AlistairCheeseman/WindTunnelApparatus/Firmware/Tests/FPGA/FPGAEchoExample/GSMBS2015.2.sdk/echo_server_bsp/microblaze_0/include/xparameters.h

#ifndef XPARAMETERS_H   /* prevent circular inclusions */
#define XPARAMETERS_H   /* by using protection macros */

/* Definitions for bus frequencies */
#define XPAR_CPU_M_AXI_DP_FREQ_HZ 100000000
/******************************************************************/

/* Canonical definitions for bus frequencies */
/******************************************************************/

#define XPAR_CPU_CORE_CLOCK_FREQ_HZ 100000000
#define XPAR_MICROBLAZE_CORE_CLOCK_FREQ_HZ 100000000

/******************************************************************/


/* Definitions for peripheral MICROBLAZE_0 */
#define XPAR_MICROBLAZE_0_ADDR_TAG_BITS 10
#define XPAR_MICROBLAZE_0_ALLOW_DCACHE_WR 1
#define XPAR_MICROBLAZE_0_ALLOW_ICACHE_WR 1
#define XPAR_MICROBLAZE_0_AREA_OPTIMIZED 0
#define XPAR_MICROBLAZE_0_ASYNC_INTERRUPT 1
#define XPAR_MICROBLAZE_0_AVOID_PRIMITIVES 0
#define XPAR_MICROBLAZE_0_BASE_VECTORS 0x00000000
#define XPAR_MICROBLAZE_0_BRANCH_TARGET_CACHE_SIZE 0
#define XPAR_MICROBLAZE_0_CACHE_BYTE_SIZE 16384
#define XPAR_MICROBLAZE_0_DATA_SIZE 32
#define XPAR_MICROBLAZE_0_DCACHE_ADDR_TAG 10
#define XPAR_MICROBLAZE_0_DCACHE_ALWAYS_USED 1
#define XPAR_MICROBLAZE_0_DCACHE_BASEADDR 0x60000000
#define XPAR_MICROBLAZE_0_DCACHE_BYTE_SIZE 16384
#define XPAR_MICROBLAZE_0_DCACHE_DATA_WIDTH 0
#define XPAR_MICROBLAZE_0_DCACHE_FORCE_TAG_LUTRAM 0
#define XPAR_MICROBLAZE_0_DCACHE_HIGHADDR 0x60FFFFFF
#define XPAR_MICROBLAZE_0_DCACHE_LINE_LEN 4
#define XPAR_MICROBLAZE_0_DCACHE_USE_WRITEBACK 0
#define XPAR_MICROBLAZE_0_DCACHE_VICTIMS 0
#define XPAR_MICROBLAZE_0_DEBUG_COUNTER_WIDTH 32
#define XPAR_MICROBLAZE_0_DEBUG_ENABLED 1
#define XPAR_MICROBLAZE_0_DEBUG_EVENT_COUNTERS 5
#define XPAR_MICROBLAZE_0_DEBUG_EXTERNAL_TRACE 0
#define XPAR_MICROBLAZE_0_DEBUG_LATENCY_COUNTERS 1
#define XPAR_MICROBLAZE_0_DEBUG_PROFILE_SIZE 0
#define XPAR_MICROBLAZE_0_DEBUG_TRACE_SIZE 8192
#define XPAR_MICROBLAZE_0_DIV_ZERO_EXCEPTION 0
#define XPAR_MICROBLAZE_0_DYNAMIC_BUS_SIZING 0
#define XPAR_MICROBLAZE_0_D_AXI 1
#define XPAR_MICROBLAZE_0_D_LMB 1
#define XPAR_MICROBLAZE_0_ECC_USE_CE_EXCEPTION 0
#define XPAR_MICROBLAZE_0_EDGE_IS_POSITIVE 1
#define XPAR_MICROBLAZE_0_ENABLE_DISCRETE_PORTS 0
#define XPAR_MICROBLAZE_0_ENDIANNESS 1
#define XPAR_MICROBLAZE_0_FAULT_TOLERANT 0
#define XPAR_MICROBLAZE_0_FPU_EXCEPTION 0
#define XPAR_MICROBLAZE_0_FREQ 100000000
#define XPAR_MICROBLAZE_0_FSL_EXCEPTION 0
#define XPAR_MICROBLAZE_0_FSL_LINKS 0
#define XPAR_MICROBLAZE_0_ICACHE_ALWAYS_USED 1
#define XPAR_MICROBLAZE_0_ICACHE_BASEADDR 0x60000000
#define XPAR_MICROBLAZE_0_ICACHE_DATA_WIDTH 0
#define XPAR_MICROBLAZE_0_ICACHE_FORCE_TAG_LUTRAM 0
#define XPAR_MICROBLAZE_0_ICACHE_HIGHADDR 0x60FFFFFF
#define XPAR_MICROBLAZE_0_ICACHE_LINE_LEN 4
#define XPAR_MICROBLAZE_0_ICACHE_STREAMS 0
#define XPAR_MICROBLAZE_0_ICACHE_VICTIMS 0
#define XPAR_MICROBLAZE_0_ILL_OPCODE_EXCEPTION 0
#define XPAR_MICROBLAZE_0_IMPRECISE_EXCEPTIONS 0
#define XPAR_MICROBLAZE_0_INTERCONNECT 2
#define XPAR_MICROBLAZE_0_INTERRUPT_IS_EDGE 0
#define XPAR_MICROBLAZE_0_I_AXI 0
#define XPAR_MICROBLAZE_0_I_LMB 1
#define XPAR_MICROBLAZE_0_LOCKSTEP_SELECT 0
#define XPAR_MICROBLAZE_0_LOCKSTEP_SLAVE 0
#define XPAR_MICROBLAZE_0_M0_AXIS_DATA_WIDTH 32
#define XPAR_MICROBLAZE_0_M0_AXIS_PROTOCOL GENERIC
#define XPAR_MICROBLAZE_0_M1_AXIS_DATA_WIDTH 32
#define XPAR_MICROBLAZE_0_M1_AXIS_PROTOCOL GENERIC
#define XPAR_MICROBLAZE_0_M2_AXIS_DATA_WIDTH 32
#define XPAR_MICROBLAZE_0_M2_AXIS_PROTOCOL GENERIC
#define XPAR_MICROBLAZE_0_M3_AXIS_DATA_WIDTH 32
#define XPAR_MICROBLAZE_0_M3_AXIS_PROTOCOL GENERIC
#define XPAR_MICROBLAZE_0_M4_AXIS_DATA_WIDTH 32
#define XPAR_MICROBLAZE_0_M4_AXIS_PROTOCOL GENERIC
#define XPAR_MICROBLAZE_0_M5_AXIS_DATA_WIDTH 32
#define XPAR_MICROBLAZE_0_M5_AXIS_PROTOCOL GENERIC
#define XPAR_MICROBLAZE_0_M6_AXIS_DATA_WIDTH 32
#define XPAR_MICROBLAZE_0_M6_AXIS_PROTOCOL GENERIC
#define XPAR_MICROBLAZE_0_M7_AXIS_DATA_WIDTH 32
#define XPAR_MICROBLAZE_0_M7_AXIS_PROTOCOL GENERIC
#define XPAR_MICROBLAZE_0_M8_AXIS_DATA_WIDTH 32
#define XPAR_MICROBLAZE_0_M8_AXIS_PROTOCOL GENERIC
#define XPAR_MICROBLAZE_0_M9_AXIS_DATA_WIDTH 32
#define XPAR_MICROBLAZE_0_M9_AXIS_PROTOCOL GENERIC
#define XPAR_MICROBLAZE_0_M10_AXIS_DATA_WIDTH 32
#define XPAR_MICROBLAZE_0_M10_AXIS_PROTOCOL GENERIC
#define XPAR_MICROBLAZE_0_M11_AXIS_DATA_WIDTH 32
#define XPAR_MICROBLAZE_0_M11_AXIS_PROTOCOL GENERIC
#define XPAR_MICROBLAZE_0_M12_AXIS_DATA_WIDTH 32
#define XPAR_MICROBLAZE_0_M12_AXIS_PROTOCOL GENERIC
#define XPAR_MICROBLAZE_0_M13_AXIS_DATA_WIDTH 32
#define XPAR_MICROBLAZE_0_M13_AXIS_PROTOCOL GENERIC
#define XPAR_MICROBLAZE_0_M14_AXIS_DATA_WIDTH 32
#define XPAR_MICROBLAZE_0_M14_AXIS_PROTOCOL GENERIC
#define XPAR_MICROBLAZE_0_M15_AXIS_DATA_WIDTH 32
#define XPAR_MICROBLAZE_0_M15_AXIS_PROTOCOL GENERIC
#define XPAR_MICROBLAZE_0_MMU_DTLB_SIZE 4
#define XPAR_MICROBLAZE_0_MMU_ITLB_SIZE 2
#define XPAR_MICROBLAZE_0_MMU_PRIVILEGED_INSTR 0
#define XPAR_MICROBLAZE_0_MMU_TLB_ACCESS 3
#define XPAR_MICROBLAZE_0_MMU_ZONES 16
#define XPAR_MICROBLAZE_0_M_AXI_DC_ADDR_WIDTH 32
#define XPAR_MICROBLAZE_0_M_AXI_DC_ARUSER_WIDTH 5
#define XPAR_MICROBLAZE_0_M_AXI_DC_AWUSER_WIDTH 5
#define XPAR_MICROBLAZE_0_M_AXI_DC_BUSER_WIDTH 1
#define XPAR_MICROBLAZE_0_M_AXI_DC_DATA_WIDTH 32
#define XPAR_MICROBLAZE_0_M_AXI_DC_EXCLUSIVE_ACCESS 0
#define XPAR_MICROBLAZE_0_M_AXI_DC_RUSER_WIDTH 1
#define XPAR_MICROBLAZE_0_M_AXI_DC_THREAD_ID_WIDTH 1
#define XPAR_MICROBLAZE_0_M_AXI_DC_USER_SIGNALS 0
#define XPAR_MICROBLAZE_0_M_AXI_DC_USER_VALUE 31
#define XPAR_MICROBLAZE_0_M_AXI_DC_WUSER_WIDTH 1
#define XPAR_MICROBLAZE_0_M_AXI_DP_ADDR_WIDTH 32
#define XPAR_MICROBLAZE_0_M_AXI_DP_DATA_WIDTH 32
#define XPAR_MICROBLAZE_0_M_AXI_DP_EXCLUSIVE_ACCESS 0
#define XPAR_MICROBLAZE_0_M_AXI_DP_THREAD_ID_WIDTH 1
#define XPAR_MICROBLAZE_0_M_AXI_D_BUS_EXCEPTION 0
#define XPAR_MICROBLAZE_0_M_AXI_IC_ADDR_WIDTH 32
#define XPAR_MICROBLAZE_0_M_AXI_IC_ARUSER_WIDTH 5
#define XPAR_MICROBLAZE_0_M_AXI_IC_AWUSER_WIDTH 5
#define XPAR_MICROBLAZE_0_M_AXI_IC_BUSER_WIDTH 1
#define XPAR_MICROBLAZE_0_M_AXI_IC_DATA_WIDTH 32
#define XPAR_MICROBLAZE_0_M_AXI_IC_RUSER_WIDTH 1
#define XPAR_MICROBLAZE_0_M_AXI_IC_THREAD_ID_WIDTH 1
#define XPAR_MICROBLAZE_0_M_AXI_IC_USER_SIGNALS 0
#define XPAR_MICROBLAZE_0_M_AXI_IC_USER_VALUE 31
#define XPAR_MICROBLAZE_0_M_AXI_IC_WUSER_WIDTH 1
#define XPAR_MICROBLAZE_0_M_AXI_IP_ADDR_WIDTH 32
#define XPAR_MICROBLAZE_0_M_AXI_IP_DATA_WIDTH 32
#define XPAR_MICROBLAZE_0_M_AXI_IP_THREAD_ID_WIDTH 1
#define XPAR_MICROBLAZE_0_M_AXI_I_BUS_EXCEPTION 0
#define XPAR_MICROBLAZE_0_NUMBER_OF_PC_BRK 1
#define XPAR_MICROBLAZE_0_NUMBER_OF_RD_ADDR_BRK 0
#define XPAR_MICROBLAZE_0_NUMBER_OF_WR_ADDR_BRK 0
#define XPAR_MICROBLAZE_0_NUM_SYNC_FF_CLK 2
#define XPAR_MICROBLAZE_0_NUM_SYNC_FF_CLK_DEBUG 2
#define XPAR_MICROBLAZE_0_NUM_SYNC_FF_CLK_IRQ 1
#define XPAR_MICROBLAZE_0_NUM_SYNC_FF_DBG_CLK 1
#define XPAR_MICROBLAZE_0_OPCODE_0X0_ILLEGAL 0
#define XPAR_MICROBLAZE_0_OPTIMIZATION 0
#define XPAR_MICROBLAZE_0_PC_WIDTH 32
#define XPAR_MICROBLAZE_0_PVR 0
#define XPAR_MICROBLAZE_0_PVR_USER1 0x00
#define XPAR_MICROBLAZE_0_PVR_USER2 0x00000000
#define XPAR_MICROBLAZE_0_RESET_MSR 0x00000000
#define XPAR_MICROBLAZE_0_S0_AXIS_DATA_WIDTH 32
#define XPAR_MICROBLAZE_0_S0_AXIS_PROTOCOL GENERIC
#define XPAR_MICROBLAZE_0_S1_AXIS_DATA_WIDTH 32
#define XPAR_MICROBLAZE_0_S1_AXIS_PROTOCOL GENERIC
#define XPAR_MICROBLAZE_0_S2_AXIS_DATA_WIDTH 32
#define XPAR_MICROBLAZE_0_S2_AXIS_PROTOCOL GENERIC
#define XPAR_MICROBLAZE_0_S3_AXIS_DATA_WIDTH 32
#define XPAR_MICROBLAZE_0_S3_AXIS_PROTOCOL GENERIC
#define XPAR_MICROBLAZE_0_S4_AXIS_DATA_WIDTH 32
#define XPAR_MICROBLAZE_0_S4_AXIS_PROTOCOL GENERIC
#define XPAR_MICROBLAZE_0_S5_AXIS_DATA_WIDTH 32
#define XPAR_MICROBLAZE_0_S5_AXIS_PROTOCOL GENERIC
#define XPAR_MICROBLAZE_0_S6_AXIS_DATA_WIDTH 32
#define XPAR_MICROBLAZE_0_S6_AXIS_PROTOCOL GENERIC
#define XPAR_MICROBLAZE_0_S7_AXIS_DATA_WIDTH 32
#define XPAR_MICROBLAZE_0_S7_AXIS_PROTOCOL GENERIC
#define XPAR_MICROBLAZE_0_S8_AXIS_DATA_WIDTH 32
#define XPAR_MICROBLAZE_0_S8_AXIS_PROTOCOL GENERIC
#define XPAR_MICROBLAZE_0_S9_AXIS_DATA_WIDTH 32
#define XPAR_MICROBLAZE_0_S9_AXIS_PROTOCOL GENERIC
#define XPAR_MICROBLAZE_0_S10_AXIS_DATA_WIDTH 32
#define XPAR_MICROBLAZE_0_S10_AXIS_PROTOCOL GENERIC
#define XPAR_MICROBLAZE_0_S11_AXIS_DATA_WIDTH 32
#define XPAR_MICROBLAZE_0_S11_AXIS_PROTOCOL GENERIC
#define XPAR_MICROBLAZE_0_S12_AXIS_DATA_WIDTH 32
#define XPAR_MICROBLAZE_0_S12_AXIS_PROTOCOL GENERIC
#define XPAR_MICROBLAZE_0_S13_AXIS_DATA_WIDTH 32
#define XPAR_MICROBLAZE_0_S13_AXIS_PROTOCOL GENERIC
#define XPAR_MICROBLAZE_0_S14_AXIS_DATA_WIDTH 32
#define XPAR_MICROBLAZE_0_S14_AXIS_PROTOCOL GENERIC
#define XPAR_MICROBLAZE_0_S15_AXIS_DATA_WIDTH 32
#define XPAR_MICROBLAZE_0_S15_AXIS_PROTOCOL GENERIC
#define XPAR_MICROBLAZE_0_SCO 0
#define XPAR_MICROBLAZE_0_TRACE 0
#define XPAR_MICROBLAZE_0_UNALIGNED_EXCEPTIONS 0
#define XPAR_MICROBLAZE_0_USE_BARREL 0
#define XPAR_MICROBLAZE_0_USE_BRANCH_TARGET_CACHE 0
#define XPAR_MICROBLAZE_0_USE_CONFIG_RESET 0
#define XPAR_MICROBLAZE_0_USE_DCACHE 1
#define XPAR_MICROBLAZE_0_USE_DIV 0
#define XPAR_MICROBLAZE_0_USE_EXTENDED_FSL_INSTR 0
#define XPAR_MICROBLAZE_0_USE_EXT_BRK 0
#define XPAR_MICROBLAZE_0_USE_EXT_NM_BRK 0
#define XPAR_MICROBLAZE_0_USE_FPU 0
#define XPAR_MICROBLAZE_0_USE_HW_MUL 0
#define XPAR_MICROBLAZE_0_USE_ICACHE 1
#define XPAR_MICROBLAZE_0_USE_INTERRUPT 2
#define XPAR_MICROBLAZE_0_USE_MMU 0
#define XPAR_MICROBLAZE_0_USE_MSR_INSTR 0
#define XPAR_MICROBLAZE_0_USE_PCMP_INSTR 0
#define XPAR_MICROBLAZE_0_USE_REORDER_INSTR 1
#define XPAR_MICROBLAZE_0_USE_STACK_PROTECTION 0
#define XPAR_MICROBLAZE_0_COMPONENT_NAME design_1_microblaze_0_0
#define XPAR_MICROBLAZE_0_EDK_IPTYPE PROCESSOR
#define XPAR_MICROBLAZE_0_EDK_SPECIAL microblaze
#define XPAR_MICROBLAZE_0_G_TEMPLATE_LIST 0
#define XPAR_MICROBLAZE_0_G_USE_EXCEPTIONS 0

/******************************************************************/

#define XPAR_CPU_ID 0
#define XPAR_MICROBLAZE_ID 0
#define XPAR_MICROBLAZE_ADDR_TAG_BITS 10
#define XPAR_MICROBLAZE_ALLOW_DCACHE_WR 1
#define XPAR_MICROBLAZE_ALLOW_ICACHE_WR 1
#define XPAR_MICROBLAZE_AREA_OPTIMIZED 0
#define XPAR_MICROBLAZE_ASYNC_INTERRUPT 1
#define XPAR_MICROBLAZE_AVOID_PRIMITIVES 0
#define XPAR_MICROBLAZE_BASE_VECTORS 0x00000000
#define XPAR_MICROBLAZE_BRANCH_TARGET_CACHE_SIZE 0
#define XPAR_MICROBLAZE_CACHE_BYTE_SIZE 16384
#define XPAR_MICROBLAZE_DATA_SIZE 32
#define XPAR_MICROBLAZE_DCACHE_ADDR_TAG 10
#define XPAR_MICROBLAZE_DCACHE_ALWAYS_USED 1
#define XPAR_MICROBLAZE_DCACHE_BASEADDR 0x60000000
#define XPAR_MICROBLAZE_DCACHE_BYTE_SIZE 16384
#define XPAR_MICROBLAZE_DCACHE_DATA_WIDTH 0
#define XPAR_MICROBLAZE_DCACHE_FORCE_TAG_LUTRAM 0
#define XPAR_MICROBLAZE_DCACHE_HIGHADDR 0x60FFFFFF
#define XPAR_MICROBLAZE_DCACHE_LINE_LEN 4
#define XPAR_MICROBLAZE_DCACHE_USE_WRITEBACK 0
#define XPAR_MICROBLAZE_DCACHE_VICTIMS 0
#define XPAR_MICROBLAZE_DEBUG_COUNTER_WIDTH 32
#define XPAR_MICROBLAZE_DEBUG_ENABLED 1
#define XPAR_MICROBLAZE_DEBUG_EVENT_COUNTERS 5
#define XPAR_MICROBLAZE_DEBUG_EXTERNAL_TRACE 0
#define XPAR_MICROBLAZE_DEBUG_LATENCY_COUNTERS 1
#define XPAR_MICROBLAZE_DEBUG_PROFILE_SIZE 0
#define XPAR_MICROBLAZE_DEBUG_TRACE_SIZE 8192
#define XPAR_MICROBLAZE_DIV_ZERO_EXCEPTION 0
#define XPAR_MICROBLAZE_DYNAMIC_BUS_SIZING 0
#define XPAR_MICROBLAZE_D_AXI 1
#define XPAR_MICROBLAZE_D_LMB 1
#define XPAR_MICROBLAZE_ECC_USE_CE_EXCEPTION 0
#define XPAR_MICROBLAZE_EDGE_IS_POSITIVE 1
#define XPAR_MICROBLAZE_ENABLE_DISCRETE_PORTS 0
#define XPAR_MICROBLAZE_ENDIANNESS 1
#define XPAR_MICROBLAZE_FAULT_TOLERANT 0
#define XPAR_MICROBLAZE_FPU_EXCEPTION 0
#define XPAR_MICROBLAZE_FREQ 100000000
#define XPAR_MICROBLAZE_FSL_EXCEPTION 0
#define XPAR_MICROBLAZE_FSL_LINKS 0
#define XPAR_MICROBLAZE_ICACHE_ALWAYS_USED 1
#define XPAR_MICROBLAZE_ICACHE_BASEADDR 0x60000000
#define XPAR_MICROBLAZE_ICACHE_DATA_WIDTH 0
#define XPAR_MICROBLAZE_ICACHE_FORCE_TAG_LUTRAM 0
#define XPAR_MICROBLAZE_ICACHE_HIGHADDR 0x60FFFFFF
#define XPAR_MICROBLAZE_ICACHE_LINE_LEN 4
#define XPAR_MICROBLAZE_ICACHE_STREAMS 0
#define XPAR_MICROBLAZE_ICACHE_VICTIMS 0
#define XPAR_MICROBLAZE_ILL_OPCODE_EXCEPTION 0
#define XPAR_MICROBLAZE_IMPRECISE_EXCEPTIONS 0
#define XPAR_MICROBLAZE_INTERCONNECT 2
#define XPAR_MICROBLAZE_INTERRUPT_IS_EDGE 0
#define XPAR_MICROBLAZE_I_AXI 0
#define XPAR_MICROBLAZE_I_LMB 1
#define XPAR_MICROBLAZE_LOCKSTEP_SELECT 0
#define XPAR_MICROBLAZE_LOCKSTEP_SLAVE 0
#define XPAR_MICROBLAZE_M0_AXIS_DATA_WIDTH 32
#define XPAR_MICROBLAZE_M0_AXIS_PROTOCOL GENERIC
#define XPAR_MICROBLAZE_M1_AXIS_DATA_WIDTH 32
#define XPAR_MICROBLAZE_M1_AXIS_PROTOCOL GENERIC
#define XPAR_MICROBLAZE_M2_AXIS_DATA_WIDTH 32
#define XPAR_MICROBLAZE_M2_AXIS_PROTOCOL GENERIC
#define XPAR_MICROBLAZE_M3_AXIS_DATA_WIDTH 32
#define XPAR_MICROBLAZE_M3_AXIS_PROTOCOL GENERIC
#define XPAR_MICROBLAZE_M4_AXIS_DATA_WIDTH 32
#define XPAR_MICROBLAZE_M4_AXIS_PROTOCOL GENERIC
#define XPAR_MICROBLAZE_M5_AXIS_DATA_WIDTH 32
#define XPAR_MICROBLAZE_M5_AXIS_PROTOCOL GENERIC
#define XPAR_MICROBLAZE_M6_AXIS_DATA_WIDTH 32
#define XPAR_MICROBLAZE_M6_AXIS_PROTOCOL GENERIC
#define XPAR_MICROBLAZE_M7_AXIS_DATA_WIDTH 32
#define XPAR_MICROBLAZE_M7_AXIS_PROTOCOL GENERIC
#define XPAR_MICROBLAZE_M8_AXIS_DATA_WIDTH 32
#define XPAR_MICROBLAZE_M8_AXIS_PROTOCOL GENERIC
#define XPAR_MICROBLAZE_M9_AXIS_DATA_WIDTH 32
#define XPAR_MICROBLAZE_M9_AXIS_PROTOCOL GENERIC
#define XPAR_MICROBLAZE_M10_AXIS_DATA_WIDTH 32
#define XPAR_MICROBLAZE_M10_AXIS_PROTOCOL GENERIC
#define XPAR_MICROBLAZE_M11_AXIS_DATA_WIDTH 32
#define XPAR_MICROBLAZE_M11_AXIS_PROTOCOL GENERIC
#define XPAR_MICROBLAZE_M12_AXIS_DATA_WIDTH 32
#define XPAR_MICROBLAZE_M12_AXIS_PROTOCOL GENERIC
#define XPAR_MICROBLAZE_M13_AXIS_DATA_WIDTH 32
#define XPAR_MICROBLAZE_M13_AXIS_PROTOCOL GENERIC
#define XPAR_MICROBLAZE_M14_AXIS_DATA_WIDTH 32
#define XPAR_MICROBLAZE_M14_AXIS_PROTOCOL GENERIC
#define XPAR_MICROBLAZE_M15_AXIS_DATA_WIDTH 32
#define XPAR_MICROBLAZE_M15_AXIS_PROTOCOL GENERIC
#define XPAR_MICROBLAZE_MMU_DTLB_SIZE 4
#define XPAR_MICROBLAZE_MMU_ITLB_SIZE 2
#define XPAR_MICROBLAZE_MMU_PRIVILEGED_INSTR 0
#define XPAR_MICROBLAZE_MMU_TLB_ACCESS 3
#define XPAR_MICROBLAZE_MMU_ZONES 16
#define XPAR_MICROBLAZE_M_AXI_DC_ADDR_WIDTH 32
#define XPAR_MICROBLAZE_M_AXI_DC_ARUSER_WIDTH 5
#define XPAR_MICROBLAZE_M_AXI_DC_AWUSER_WIDTH 5
#define XPAR_MICROBLAZE_M_AXI_DC_BUSER_WIDTH 1
#define XPAR_MICROBLAZE_M_AXI_DC_DATA_WIDTH 32
#define XPAR_MICROBLAZE_M_AXI_DC_EXCLUSIVE_ACCESS 0
#define XPAR_MICROBLAZE_M_AXI_DC_RUSER_WIDTH 1
#define XPAR_MICROBLAZE_M_AXI_DC_THREAD_ID_WIDTH 1
#define XPAR_MICROBLAZE_M_AXI_DC_USER_SIGNALS 0
#define XPAR_MICROBLAZE_M_AXI_DC_USER_VALUE 31
#define XPAR_MICROBLAZE_M_AXI_DC_WUSER_WIDTH 1
#define XPAR_MICROBLAZE_M_AXI_DP_ADDR_WIDTH 32
#define XPAR_MICROBLAZE_M_AXI_DP_DATA_WIDTH 32
#define XPAR_MICROBLAZE_M_AXI_DP_EXCLUSIVE_ACCESS 0
#define XPAR_MICROBLAZE_M_AXI_DP_THREAD_ID_WIDTH 1
#define XPAR_MICROBLAZE_M_AXI_D_BUS_EXCEPTION 0
#define XPAR_MICROBLAZE_M_AXI_IC_ADDR_WIDTH 32
#define XPAR_MICROBLAZE_M_AXI_IC_ARUSER_WIDTH 5
#define XPAR_MICROBLAZE_M_AXI_IC_AWUSER_WIDTH 5
#define XPAR_MICROBLAZE_M_AXI_IC_BUSER_WIDTH 1
#define XPAR_MICROBLAZE_M_AXI_IC_DATA_WIDTH 32
#define XPAR_MICROBLAZE_M_AXI_IC_RUSER_WIDTH 1
#define XPAR_MICROBLAZE_M_AXI_IC_THREAD_ID_WIDTH 1
#define XPAR_MICROBLAZE_M_AXI_IC_USER_SIGNALS 0
#define XPAR_MICROBLAZE_M_AXI_IC_USER_VALUE 31
#define XPAR_MICROBLAZE_M_AXI_IC_WUSER_WIDTH 1
#define XPAR_MICROBLAZE_M_AXI_IP_ADDR_WIDTH 32
#define XPAR_MICROBLAZE_M_AXI_IP_DATA_WIDTH 32
#define XPAR_MICROBLAZE_M_AXI_IP_THREAD_ID_WIDTH 1
#define XPAR_MICROBLAZE_M_AXI_I_BUS_EXCEPTION 0
#define XPAR_MICROBLAZE_NUMBER_OF_PC_BRK 1
#define XPAR_MICROBLAZE_NUMBER_OF_RD_ADDR_BRK 0
#define XPAR_MICROBLAZE_NUMBER_OF_WR_ADDR_BRK 0
#define XPAR_MICROBLAZE_NUM_SYNC_FF_CLK 2
#define XPAR_MICROBLAZE_NUM_SYNC_FF_CLK_DEBUG 2
#define XPAR_MICROBLAZE_NUM_SYNC_FF_CLK_IRQ 1
#define XPAR_MICROBLAZE_NUM_SYNC_FF_DBG_CLK 1
#define XPAR_MICROBLAZE_OPCODE_0X0_ILLEGAL 0
#define XPAR_MICROBLAZE_OPTIMIZATION 0
#define XPAR_MICROBLAZE_PC_WIDTH 32
#define XPAR_MICROBLAZE_PVR 0
#define XPAR_MICROBLAZE_PVR_USER1 0x00
#define XPAR_MICROBLAZE_PVR_USER2 0x00000000
#define XPAR_MICROBLAZE_RESET_MSR 0x00000000
#define XPAR_MICROBLAZE_S0_AXIS_DATA_WIDTH 32
#define XPAR_MICROBLAZE_S0_AXIS_PROTOCOL GENERIC
#define XPAR_MICROBLAZE_S1_AXIS_DATA_WIDTH 32
#define XPAR_MICROBLAZE_S1_AXIS_PROTOCOL GENERIC
#define XPAR_MICROBLAZE_S2_AXIS_DATA_WIDTH 32
#define XPAR_MICROBLAZE_S2_AXIS_PROTOCOL GENERIC
#define XPAR_MICROBLAZE_S3_AXIS_DATA_WIDTH 32
#define XPAR_MICROBLAZE_S3_AXIS_PROTOCOL GENERIC
#define XPAR_MICROBLAZE_S4_AXIS_DATA_WIDTH 32
#define XPAR_MICROBLAZE_S4_AXIS_PROTOCOL GENERIC
#define XPAR_MICROBLAZE_S5_AXIS_DATA_WIDTH 32
#define XPAR_MICROBLAZE_S5_AXIS_PROTOCOL GENERIC
#define XPAR_MICROBLAZE_S6_AXIS_DATA_WIDTH 32
#define XPAR_MICROBLAZE_S6_AXIS_PROTOCOL GENERIC
#define XPAR_MICROBLAZE_S7_AXIS_DATA_WIDTH 32
#define XPAR_MICROBLAZE_S7_AXIS_PROTOCOL GENERIC
#define XPAR_MICROBLAZE_S8_AXIS_DATA_WIDTH 32
#define XPAR_MICROBLAZE_S8_AXIS_PROTOCOL GENERIC
#define XPAR_MICROBLAZE_S9_AXIS_DATA_WIDTH 32
#define XPAR_MICROBLAZE_S9_AXIS_PROTOCOL GENERIC
#define XPAR_MICROBLAZE_S10_AXIS_DATA_WIDTH 32
#define XPAR_MICROBLAZE_S10_AXIS_PROTOCOL GENERIC
#define XPAR_MICROBLAZE_S11_AXIS_DATA_WIDTH 32
#define XPAR_MICROBLAZE_S11_AXIS_PROTOCOL GENERIC
#define XPAR_MICROBLAZE_S12_AXIS_DATA_WIDTH 32
#define XPAR_MICROBLAZE_S12_AXIS_PROTOCOL GENERIC
#define XPAR_MICROBLAZE_S13_AXIS_DATA_WIDTH 32
#define XPAR_MICROBLAZE_S13_AXIS_PROTOCOL GENERIC
#define XPAR_MICROBLAZE_S14_AXIS_DATA_WIDTH 32
#define XPAR_MICROBLAZE_S14_AXIS_PROTOCOL GENERIC
#define XPAR_MICROBLAZE_S15_AXIS_DATA_WIDTH 32
#define XPAR_MICROBLAZE_S15_AXIS_PROTOCOL GENERIC
#define XPAR_MICROBLAZE_SCO 0
#define XPAR_MICROBLAZE_TRACE 0
#define XPAR_MICROBLAZE_UNALIGNED_EXCEPTIONS 0
#define XPAR_MICROBLAZE_USE_BARREL 0
#define XPAR_MICROBLAZE_USE_BRANCH_TARGET_CACHE 0
#define XPAR_MICROBLAZE_USE_CONFIG_RESET 0
#define XPAR_MICROBLAZE_USE_DCACHE 1
#define XPAR_MICROBLAZE_USE_DIV 0
#define XPAR_MICROBLAZE_USE_EXTENDED_FSL_INSTR 0
#define XPAR_MICROBLAZE_USE_EXT_BRK 0
#define XPAR_MICROBLAZE_USE_EXT_NM_BRK 0
#define XPAR_MICROBLAZE_USE_FPU 0
#define XPAR_MICROBLAZE_USE_HW_MUL 0
#define XPAR_MICROBLAZE_USE_ICACHE 1
#define XPAR_MICROBLAZE_USE_INTERRUPT 2
#define XPAR_MICROBLAZE_USE_MMU 0
#define XPAR_MICROBLAZE_USE_MSR_INSTR 0
#define XPAR_MICROBLAZE_USE_PCMP_INSTR 0
#define XPAR_MICROBLAZE_USE_REORDER_INSTR 1
#define XPAR_MICROBLAZE_USE_STACK_PROTECTION 0
#define XPAR_MICROBLAZE_COMPONENT_NAME design_1_microblaze_0_0
#define XPAR_MICROBLAZE_EDK_IPTYPE PROCESSOR
#define XPAR_MICROBLAZE_EDK_SPECIAL microblaze
#define XPAR_MICROBLAZE_G_TEMPLATE_LIST 0
#define XPAR_MICROBLAZE_G_USE_EXCEPTIONS 0

/******************************************************************/

#define STDIN_BASEADDRESS 0x40600000
#define STDOUT_BASEADDRESS 0x40600000

/******************************************************************/

/* Definitions for driver BRAM */
#define XPAR_XBRAM_NUM_INSTANCES 2

/* Definitions for peripheral MICROBLAZE_0_LOCAL_MEMORY_DLMB_BRAM_IF_CNTLR */
#define XPAR_MICROBLAZE_0_LOCAL_MEMORY_DLMB_BRAM_IF_CNTLR_DEVICE_ID 0
#define XPAR_MICROBLAZE_0_LOCAL_MEMORY_DLMB_BRAM_IF_CNTLR_DATA_WIDTH 32
#define XPAR_MICROBLAZE_0_LOCAL_MEMORY_DLMB_BRAM_IF_CNTLR_ECC 0
#define XPAR_MICROBLAZE_0_LOCAL_MEMORY_DLMB_BRAM_IF_CNTLR_FAULT_INJECT 0
#define XPAR_MICROBLAZE_0_LOCAL_MEMORY_DLMB_BRAM_IF_CNTLR_CE_FAILING_REGISTERS 0
#define XPAR_MICROBLAZE_0_LOCAL_MEMORY_DLMB_BRAM_IF_CNTLR_UE_FAILING_REGISTERS 0
#define XPAR_MICROBLAZE_0_LOCAL_MEMORY_DLMB_BRAM_IF_CNTLR_ECC_STATUS_REGISTERS 0
#define XPAR_MICROBLAZE_0_LOCAL_MEMORY_DLMB_BRAM_IF_CNTLR_CE_COUNTER_WIDTH 0
#define XPAR_MICROBLAZE_0_LOCAL_MEMORY_DLMB_BRAM_IF_CNTLR_ECC_ONOFF_REGISTER 0
#define XPAR_MICROBLAZE_0_LOCAL_MEMORY_DLMB_BRAM_IF_CNTLR_ECC_ONOFF_RESET_VALUE 1
#define XPAR_MICROBLAZE_0_LOCAL_MEMORY_DLMB_BRAM_IF_CNTLR_WRITE_ACCESS 2
#define XPAR_MICROBLAZE_0_LOCAL_MEMORY_DLMB_BRAM_IF_CNTLR_BASEADDR 0x00000000
#define XPAR_MICROBLAZE_0_LOCAL_MEMORY_DLMB_BRAM_IF_CNTLR_HIGHADDR 0x00007FFF
#define XPAR_MICROBLAZE_0_LOCAL_MEMORY_DLMB_BRAM_IF_CNTLR_S_AXI_CTRL_BASEADDR 0xFFFFFFFF 
#define XPAR_MICROBLAZE_0_LOCAL_MEMORY_DLMB_BRAM_IF_CNTLR_S_AXI_CTRL_HIGHADDR 0xFFFFFFFF 


/* Definitions for peripheral MICROBLAZE_0_LOCAL_MEMORY_ILMB_BRAM_IF_CNTLR */
#define XPAR_MICROBLAZE_0_LOCAL_MEMORY_ILMB_BRAM_IF_CNTLR_DEVICE_ID 1
#define XPAR_MICROBLAZE_0_LOCAL_MEMORY_ILMB_BRAM_IF_CNTLR_DATA_WIDTH 32
#define XPAR_MICROBLAZE_0_LOCAL_MEMORY_ILMB_BRAM_IF_CNTLR_ECC 0
#define XPAR_MICROBLAZE_0_LOCAL_MEMORY_ILMB_BRAM_IF_CNTLR_FAULT_INJECT 0
#define XPAR_MICROBLAZE_0_LOCAL_MEMORY_ILMB_BRAM_IF_CNTLR_CE_FAILING_REGISTERS 0
#define XPAR_MICROBLAZE_0_LOCAL_MEMORY_ILMB_BRAM_IF_CNTLR_UE_FAILING_REGISTERS 0
#define XPAR_MICROBLAZE_0_LOCAL_MEMORY_ILMB_BRAM_IF_CNTLR_ECC_STATUS_REGISTERS 0
#define XPAR_MICROBLAZE_0_LOCAL_MEMORY_ILMB_BRAM_IF_CNTLR_CE_COUNTER_WIDTH 0
#define XPAR_MICROBLAZE_0_LOCAL_MEMORY_ILMB_BRAM_IF_CNTLR_ECC_ONOFF_REGISTER 0
#define XPAR_MICROBLAZE_0_LOCAL_MEMORY_ILMB_BRAM_IF_CNTLR_ECC_ONOFF_RESET_VALUE 1
#define XPAR_MICROBLAZE_0_LOCAL_MEMORY_ILMB_BRAM_IF_CNTLR_WRITE_ACCESS 2
#define XPAR_MICROBLAZE_0_LOCAL_MEMORY_ILMB_BRAM_IF_CNTLR_BASEADDR 0x00000000
#define XPAR_MICROBLAZE_0_LOCAL_MEMORY_ILMB_BRAM_IF_CNTLR_HIGHADDR 0x00007FFF
#define XPAR_MICROBLAZE_0_LOCAL_MEMORY_ILMB_BRAM_IF_CNTLR_S_AXI_CTRL_BASEADDR 0xFFFFFFFF 
#define XPAR_MICROBLAZE_0_LOCAL_MEMORY_ILMB_BRAM_IF_CNTLR_S_AXI_CTRL_HIGHADDR 0xFFFFFFFF 


/******************************************************************/

/* Canonical definitions for peripheral MICROBLAZE_0_LOCAL_MEMORY_DLMB_BRAM_IF_CNTLR */
#define XPAR_BRAM_0_DEVICE_ID XPAR_MICROBLAZE_0_LOCAL_MEMORY_DLMB_BRAM_IF_CNTLR_DEVICE_ID
#define XPAR_BRAM_0_DATA_WIDTH 32
#define XPAR_BRAM_0_ECC 0
#define XPAR_BRAM_0_FAULT_INJECT 0
#define XPAR_BRAM_0_CE_FAILING_REGISTERS 0
#define XPAR_BRAM_0_UE_FAILING_REGISTERS 0
#define XPAR_BRAM_0_ECC_STATUS_REGISTERS 0
#define XPAR_BRAM_0_CE_COUNTER_WIDTH 0
#define XPAR_BRAM_0_ECC_ONOFF_REGISTER 0
#define XPAR_BRAM_0_ECC_ONOFF_RESET_VALUE 1
#define XPAR_BRAM_0_WRITE_ACCESS 2
#define XPAR_BRAM_0_BASEADDR 0x00000000
#define XPAR_BRAM_0_HIGHADDR 0x00007FFF

/* Canonical definitions for peripheral MICROBLAZE_0_LOCAL_MEMORY_ILMB_BRAM_IF_CNTLR */
#define XPAR_BRAM_1_DEVICE_ID XPAR_MICROBLAZE_0_LOCAL_MEMORY_ILMB_BRAM_IF_CNTLR_DEVICE_ID
#define XPAR_BRAM_1_DATA_WIDTH 32
#define XPAR_BRAM_1_ECC 0
#define XPAR_BRAM_1_FAULT_INJECT 0
#define XPAR_BRAM_1_CE_FAILING_REGISTERS 0
#define XPAR_BRAM_1_UE_FAILING_REGISTERS 0
#define XPAR_BRAM_1_ECC_STATUS_REGISTERS 0
#define XPAR_BRAM_1_CE_COUNTER_WIDTH 0
#define XPAR_BRAM_1_ECC_ONOFF_REGISTER 0
#define XPAR_BRAM_1_ECC_ONOFF_RESET_VALUE 1
#define XPAR_BRAM_1_WRITE_ACCESS 2
#define XPAR_BRAM_1_BASEADDR 0x00000000
#define XPAR_BRAM_1_HIGHADDR 0x00007FFF


/******************************************************************/

/* Definitions for driver EMACLITE */
#define XPAR_XEMACLITE_NUM_INSTANCES 1

/* Definitions for peripheral AXI_ETHERNETLITE_0 */
#define XPAR_AXI_ETHERNETLITE_0_DEVICE_ID 0
#define XPAR_AXI_ETHERNETLITE_0_BASEADDR 0x40E00000
#define XPAR_AXI_ETHERNETLITE_0_HIGHADDR 0x40E0FFFF
#define XPAR_AXI_ETHERNETLITE_0_TX_PING_PONG 1
#define XPAR_AXI_ETHERNETLITE_0_RX_PING_PONG 1
#define XPAR_AXI_ETHERNETLITE_0_INCLUDE_MDIO 1
#define XPAR_AXI_ETHERNETLITE_0_INCLUDE_INTERNAL_LOOPBACK 0


/******************************************************************/

/* Canonical definitions for peripheral AXI_ETHERNETLITE_0 */
#define XPAR_EMACLITE_0_DEVICE_ID XPAR_AXI_ETHERNETLITE_0_DEVICE_ID
#define XPAR_EMACLITE_0_BASEADDR 0x40E00000
#define XPAR_EMACLITE_0_HIGHADDR 0x40E0FFFF
#define XPAR_EMACLITE_0_TX_PING_PONG 1
#define XPAR_EMACLITE_0_RX_PING_PONG 1
#define XPAR_EMACLITE_0_INCLUDE_MDIO 1
#define XPAR_EMACLITE_0_INCLUDE_INTERNAL_LOOPBACK 0


/******************************************************************/


/* Definitions for peripheral AXI_EMC_0 */
#define XPAR_AXI_EMC_0_NUM_BANKS_MEM 1


/******************************************************************/

/* Definitions for peripheral AXI_EMC_0 */
#define XPAR_AXI_EMC_0_S_AXI_MEM0_BASEADDR 0x60000000

/******************************************************************/

/* Canonical definitions for peripheral AXI_EMC_0 */
#define XPAR_EMC_0_NUM_BANKS_MEM 1
#define XPAR_EMC_0_S_AXI_MEM0_BASEADDR 0x60000000
#define XPAR_EMC_0_S_AXI_MEM0_HIGHADDR 0x60FFFFFF

#define XPAR_AXI_EMC

/******************************************************************/

#define XPAR_INTC_MAX_NUM_INTR_INPUTS 2
#define XPAR_XINTC_HAS_IPR 1
#define XPAR_XINTC_HAS_SIE 1
#define XPAR_XINTC_HAS_CIE 1
#define XPAR_XINTC_HAS_IVR 1
/* Definitions for driver INTC */
#define XPAR_XINTC_NUM_INSTANCES 1

/* Definitions for peripheral MICROBLAZE_0_AXI_INTC */
#define XPAR_MICROBLAZE_0_AXI_INTC_DEVICE_ID 0
#define XPAR_MICROBLAZE_0_AXI_INTC_BASEADDR 0x41200000
#define XPAR_MICROBLAZE_0_AXI_INTC_HIGHADDR 0x4120FFFF
#define XPAR_MICROBLAZE_0_AXI_INTC_KIND_OF_INTR 0xFFFFFFFE
#define XPAR_MICROBLAZE_0_AXI_INTC_HAS_FAST 1
#define XPAR_MICROBLAZE_0_AXI_INTC_IVAR_RESET_VALUE 0x00000010
#define XPAR_MICROBLAZE_0_AXI_INTC_NUM_INTR_INPUTS 2


/******************************************************************/

#define XPAR_INTC_SINGLE_BASEADDR 0x41200000
#define XPAR_INTC_SINGLE_HIGHADDR 0x4120FFFF
#define XPAR_INTC_SINGLE_DEVICE_ID XPAR_MICROBLAZE_0_AXI_INTC_DEVICE_ID
#define XPAR_MICROBLAZE_0_AXI_INTC_TYPE 0
#define XPAR_AXI_TIMER_0_INTERRUPT_MASK 0X000001
#define XPAR_MICROBLAZE_0_AXI_INTC_AXI_TIMER_0_INTERRUPT_INTR 0
#define XPAR_AXI_ETHERNETLITE_0_IP2INTC_IRPT_MASK 0X000002
#define XPAR_MICROBLAZE_0_AXI_INTC_AXI_ETHERNETLITE_0_IP2INTC_IRPT_INTR 1

/******************************************************************/

/* Canonical definitions for peripheral MICROBLAZE_0_AXI_INTC */
#define XPAR_INTC_0_DEVICE_ID XPAR_MICROBLAZE_0_AXI_INTC_DEVICE_ID
#define XPAR_INTC_0_BASEADDR 0x41200000
#define XPAR_INTC_0_HIGHADDR 0x4120FFFF
#define XPAR_INTC_0_KIND_OF_INTR 0xFFFFFFFE
#define XPAR_INTC_0_HAS_FAST 1
#define XPAR_INTC_0_IVAR_RESET_VALUE 0x00000010
#define XPAR_INTC_0_NUM_INTR_INPUTS 2
#define XPAR_INTC_0_INTC_TYPE 0

#define XPAR_INTC_0_TMRCTR_0_VEC_ID XPAR_MICROBLAZE_0_AXI_INTC_AXI_TIMER_0_INTERRUPT_INTR
#define XPAR_INTC_0_EMACLITE_0_VEC_ID XPAR_MICROBLAZE_0_AXI_INTC_AXI_ETHERNETLITE_0_IP2INTC_IRPT_INTR

/******************************************************************/

/* Definitions for driver TMRCTR */
#define XPAR_XTMRCTR_NUM_INSTANCES 1

/* Definitions for peripheral AXI_TIMER_0 */
#define XPAR_AXI_TIMER_0_DEVICE_ID 0
#define XPAR_AXI_TIMER_0_BASEADDR 0x41C00000
#define XPAR_AXI_TIMER_0_HIGHADDR 0x41C0FFFF
#define XPAR_AXI_TIMER_0_CLOCK_FREQ_HZ 100000000


/******************************************************************/

/* Canonical definitions for peripheral AXI_TIMER_0 */
#define XPAR_TMRCTR_0_DEVICE_ID 0
#define XPAR_TMRCTR_0_BASEADDR 0x41C00000
#define XPAR_TMRCTR_0_HIGHADDR 0x41C0FFFF
#define XPAR_TMRCTR_0_CLOCK_FREQ_HZ XPAR_AXI_TIMER_0_CLOCK_FREQ_HZ

/******************************************************************/

/* Definitions for driver UARTLITE */
#define XPAR_XUARTLITE_NUM_INSTANCES 1

/* Definitions for peripheral AXI_UARTLITE_0 */
#define XPAR_AXI_UARTLITE_0_BASEADDR 0x40600000
#define XPAR_AXI_UARTLITE_0_HIGHADDR 0x4060FFFF
#define XPAR_AXI_UARTLITE_0_DEVICE_ID 0
#define XPAR_AXI_UARTLITE_0_BAUDRATE 9600
#define XPAR_AXI_UARTLITE_0_USE_PARITY 0
#define XPAR_AXI_UARTLITE_0_ODD_PARITY 0
#define XPAR_AXI_UARTLITE_0_DATA_BITS 8


/******************************************************************/

/* Canonical definitions for peripheral AXI_UARTLITE_0 */
#define XPAR_UARTLITE_0_DEVICE_ID XPAR_AXI_UARTLITE_0_DEVICE_ID
#define XPAR_UARTLITE_0_BASEADDR 0x40600000
#define XPAR_UARTLITE_0_HIGHADDR 0x4060FFFF
#define XPAR_UARTLITE_0_BAUDRATE 9600
#define XPAR_UARTLITE_0_USE_PARITY 0
#define XPAR_UARTLITE_0_ODD_PARITY 0
#define XPAR_UARTLITE_0_DATA_BITS 8


/******************************************************************/

#endif  /* end of protection macro */
