AlistairCheeseman/WindTunnelApparatus/Firmware/Tests/FPGA/FPGAUDPtest/GSMBS2015.2.sdk/UDPTest/src/main.c

/******************************************************************************
*
* Copyright (C) 2009 - 2014 Xilinx, Inc.  All rights reserved.
*
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
* Use of the Software is limited solely to applications:
* (a) running on a Xilinx device, or
* (b) that interact with a Xilinx device through a bus or interconnect.
*
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
* Except as contained in this notice, the name of the Xilinx shall not be used
* in advertising or otherwise to promote the sale, use or other dealings in
* this Software without prior written authorization from Xilinx.
*
******************************************************************************/

#include <stdio.h>

#include "xparameters.h"

#include "netif/xadapter.h"

#include "platform.h"
#include "platform_config.h"
#ifdef __arm__
#include "xil_printf.h"
#endif

#include "lwip/tcp.h"

#if LWIP_DHCP==1
#include "lwip/dhcp.h"
#endif

/* defined by each RAW mode application */
void print_utxperf_app_header();
int start_utxperf_application();
int transfer_utxperf_data();

/* missing declaration in lwIP */
void lwip_init();

#if LWIP_DHCP==1
extern volatile int dhcp_timoutcntr;
err_t dhcp_start(struct netif *netif);
#endif

extern volatile int TcpFastTmrFlag;
extern volatile int TcpSlowTmrFlag;
static struct netif server_netif;
struct netif *echo_netif;

void
print_ip(char *msg, struct ip_addr *ip) 
{
	print(msg);
	xil_printf("%d.%d.%d.%d\n\r", ip4_addr1(ip), ip4_addr2(ip), 
			ip4_addr3(ip), ip4_addr4(ip));
}

void
print_ip_settings(struct ip_addr *ip, struct ip_addr *mask, struct ip_addr *gw)
{

	print_ip("Board IP: ", ip);
	print_ip("Netmask : ", mask);
	print_ip("Gateway : ", gw);
}

#ifdef __arm__
#if XPAR_GIGE_PCS_PMA_SGMII_CORE_PRESENT == 1 || XPAR_GIGE_PCS_PMA_1000BASEX_CORE_PRESENT == 1
int ProgramSi5324(void);
int ProgramSfpPhy(void);
#endif
#endif
int main()
{
	struct ip_addr ipaddr, netmask, gw;

	/* the mac address of the board. this should be unique per board */
	unsigned char mac_ethernet_address[] =
	{ 0x00, 0x0a, 0x35, 0x00, 0x01, 0x02 };

	echo_netif = &server_netif;
#ifdef __arm__
#if XPAR_GIGE_PCS_PMA_SGMII_CORE_PRESENT == 1 || XPAR_GIGE_PCS_PMA_1000BASEX_CORE_PRESENT == 1
	ProgramSi5324();
	ProgramSfpPhy();
#endif
#endif

	init_platform();

#if LWIP_DHCP==1
    ipaddr.addr = 0;
	gw.addr = 0;
	netmask.addr = 0;
#else
	/* initliaze IP addresses to be used */
	IP4_ADDR(&ipaddr,  192, 168,   1, 10);
	IP4_ADDR(&netmask, 255, 255, 255,  0);
	IP4_ADDR(&gw,      192, 168,   1,  1);
#endif	
	print_utxperf_app_header();

	lwip_init();

  	/* Add network interface to the netif_list, and set it as default */
	if (!xemac_add(echo_netif, &ipaddr, &netmask,
						&gw, mac_ethernet_address,
						PLATFORM_EMAC_BASEADDR)) {
		xil_printf("Error adding N/W interface\n\r");
		return -1;
	}
	netif_set_default(echo_netif);

	/* now enable interrupts */
	platform_enable_interrupts();

	/* specify that the network if is up */
	netif_set_up(echo_netif);

#if (LWIP_DHCP==1)
	/* Create a new DHCP client for this interface.
	 * Note: you must call dhcp_fine_tmr() and dhcp_coarse_tmr() at
	 * the predefined regular intervals after starting the client.
	 */
	dhcp_start(echo_netif);
	dhcp_timoutcntr = 24;

	while(((echo_netif->ip_addr.addr) == 0) && (dhcp_timoutcntr > 0))
		xemacif_input(echo_netif);

	if (dhcp_timoutcntr <= 0) {
		if ((echo_netif->ip_addr.addr) == 0) {
			xil_printf("DHCP Timeout\r\n");
			xil_printf("Configuring default IP of 192.168.1.10\r\n");
			IP4_ADDR(&(echo_netif->ip_addr),  192, 168,   1, 10);
			IP4_ADDR(&(echo_netif->netmask), 255, 255, 255,  0);
			IP4_ADDR(&(echo_netif->gw),      192, 168,   1,  1);
		}
	}

	ipaddr.addr = echo_netif->ip_addr.addr;
	gw.addr = echo_netif->gw.addr;
	netmask.addr = echo_netif->netmask.addr;
#endif

	print_ip_settings(&ipaddr, &netmask, &gw);

	/* start the application (web server, rxtest, txtest, etc..) */
	start_utxperf_application();

	/* receive and process packets */
	while (1) {
		if (TcpFastTmrFlag) {
			tcp_fasttmr();
			TcpFastTmrFlag = 0;
		}
		if (TcpSlowTmrFlag) {
			tcp_slowtmr();
			TcpSlowTmrFlag = 0;
		}
		xemacif_input(echo_netif);
		transfer_utxperf_data();
	}
  
	/* never reached */
	cleanup_platform();

	return 0;
}
