AlistairCheeseman/WindTunnelApparatus/Firmware/Tests/FPGA/FPGAUDPtest/GSMBS2015.2.srcs/sources_1/bd/design_1/hdl/design_1.vhd

--Copyright 1986-2015 Xilinx, Inc. All Rights Reserved.
----------------------------------------------------------------------------------
--Tool Version: Vivado v.2015.2 (win64) Build 1266856 Fri Jun 26 16:35:25 MDT 2015
--Date        : Thu Nov 19 17:38:29 2015
--Host        : ALI-WORKSTATION running 64-bit major release  (build 9200)
--Command     : generate_target design_1.bd
--Design      : design_1
--Purpose     : IP block netlist
----------------------------------------------------------------------------------
library IEEE;
use IEEE.STD_LOGIC_1164.ALL;
library UNISIM;
use UNISIM.VCOMPONENTS.ALL;
entity m00_couplers_imp_1R706YB is
  port (
    M_ACLK : in STD_LOGIC;
    M_ARESETN : in STD_LOGIC_VECTOR ( 0 to 0 );
    M_AXI_araddr : out STD_LOGIC_VECTOR ( 31 downto 0 );
    M_AXI_arburst : out STD_LOGIC_VECTOR ( 1 downto 0 );
    M_AXI_arcache : out STD_LOGIC_VECTOR ( 3 downto 0 );
    M_AXI_arid : out STD_LOGIC_VECTOR ( 0 to 0 );
    M_AXI_arlen : out STD_LOGIC_VECTOR ( 7 downto 0 );
    M_AXI_arlock : out STD_LOGIC_VECTOR ( 0 to 0 );
    M_AXI_arprot : out STD_LOGIC_VECTOR ( 2 downto 0 );
    M_AXI_arready : in STD_LOGIC_VECTOR ( 0 to 0 );
    M_AXI_arsize : out STD_LOGIC_VECTOR ( 2 downto 0 );
    M_AXI_arvalid : out STD_LOGIC_VECTOR ( 0 to 0 );
    M_AXI_awaddr : out STD_LOGIC_VECTOR ( 31 downto 0 );
    M_AXI_awburst : out STD_LOGIC_VECTOR ( 1 downto 0 );
    M_AXI_awcache : out STD_LOGIC_VECTOR ( 3 downto 0 );
    M_AXI_awid : out STD_LOGIC_VECTOR ( 0 to 0 );
    M_AXI_awlen : out STD_LOGIC_VECTOR ( 7 downto 0 );
    M_AXI_awlock : out STD_LOGIC_VECTOR ( 0 to 0 );
    M_AXI_awprot : out STD_LOGIC_VECTOR ( 2 downto 0 );
    M_AXI_awready : in STD_LOGIC_VECTOR ( 0 to 0 );
    M_AXI_awsize : out STD_LOGIC_VECTOR ( 2 downto 0 );
    M_AXI_awvalid : out STD_LOGIC_VECTOR ( 0 to 0 );
    M_AXI_bid : in STD_LOGIC_VECTOR ( 0 to 0 );
    M_AXI_bready : out STD_LOGIC_VECTOR ( 0 to 0 );
    M_AXI_bresp : in STD_LOGIC_VECTOR ( 1 downto 0 );
    M_AXI_bvalid : in STD_LOGIC_VECTOR ( 0 to 0 );
    M_AXI_rdata : in STD_LOGIC_VECTOR ( 31 downto 0 );
    M_AXI_rid : in STD_LOGIC_VECTOR ( 0 to 0 );
    M_AXI_rlast : in STD_LOGIC_VECTOR ( 0 to 0 );
    M_AXI_rready : out STD_LOGIC_VECTOR ( 0 to 0 );
    M_AXI_rresp : in STD_LOGIC_VECTOR ( 1 downto 0 );
    M_AXI_rvalid : in STD_LOGIC_VECTOR ( 0 to 0 );
    M_AXI_wdata : out STD_LOGIC_VECTOR ( 31 downto 0 );
    M_AXI_wlast : out STD_LOGIC_VECTOR ( 0 to 0 );
    M_AXI_wready : in STD_LOGIC_VECTOR ( 0 to 0 );
    M_AXI_wstrb : out STD_LOGIC_VECTOR ( 3 downto 0 );
    M_AXI_wvalid : out STD_LOGIC_VECTOR ( 0 to 0 );
    S_ACLK : in STD_LOGIC;
    S_ARESETN : in STD_LOGIC_VECTOR ( 0 to 0 );
    S_AXI_araddr : in STD_LOGIC_VECTOR ( 31 downto 0 );
    S_AXI_arburst : in STD_LOGIC_VECTOR ( 1 downto 0 );
    S_AXI_arcache : in STD_LOGIC_VECTOR ( 3 downto 0 );
    S_AXI_arid : in STD_LOGIC_VECTOR ( 0 to 0 );
    S_AXI_arlen : in STD_LOGIC_VECTOR ( 7 downto 0 );
    S_AXI_arlock : in STD_LOGIC_VECTOR ( 0 to 0 );
    S_AXI_arprot : in STD_LOGIC_VECTOR ( 2 downto 0 );
    S_AXI_arready : out STD_LOGIC_VECTOR ( 0 to 0 );
    S_AXI_arsize : in STD_LOGIC_VECTOR ( 2 downto 0 );
    S_AXI_arvalid : in STD_LOGIC_VECTOR ( 0 to 0 );
    S_AXI_awaddr : in STD_LOGIC_VECTOR ( 31 downto 0 );
    S_AXI_awburst : in STD_LOGIC_VECTOR ( 1 downto 0 );
    S_AXI_awcache : in STD_LOGIC_VECTOR ( 3 downto 0 );
    S_AXI_awid : in STD_LOGIC_VECTOR ( 0 to 0 );
    S_AXI_awlen : in STD_LOGIC_VECTOR ( 7 downto 0 );
    S_AXI_awlock : in STD_LOGIC_VECTOR ( 0 to 0 );
    S_AXI_awprot : in STD_LOGIC_VECTOR ( 2 downto 0 );
    S_AXI_awready : out STD_LOGIC_VECTOR ( 0 to 0 );
    S_AXI_awsize : in STD_LOGIC_VECTOR ( 2 downto 0 );
    S_AXI_awvalid : in STD_LOGIC_VECTOR ( 0 to 0 );
    S_AXI_bid : out STD_LOGIC_VECTOR ( 0 to 0 );
    S_AXI_bready : in STD_LOGIC_VECTOR ( 0 to 0 );
    S_AXI_bresp : out STD_LOGIC_VECTOR ( 1 downto 0 );
    S_AXI_bvalid : out STD_LOGIC_VECTOR ( 0 to 0 );
    S_AXI_rdata : out STD_LOGIC_VECTOR ( 31 downto 0 );
    S_AXI_rid : out STD_LOGIC_VECTOR ( 0 to 0 );
    S_AXI_rlast : out STD_LOGIC_VECTOR ( 0 to 0 );
    S_AXI_rready : in STD_LOGIC_VECTOR ( 0 to 0 );
    S_AXI_rresp : out STD_LOGIC_VECTOR ( 1 downto 0 );
    S_AXI_rvalid : out STD_LOGIC_VECTOR ( 0 to 0 );
    S_AXI_wdata : in STD_LOGIC_VECTOR ( 31 downto 0 );
    S_AXI_wlast : in STD_LOGIC_VECTOR ( 0 to 0 );
    S_AXI_wready : out STD_LOGIC_VECTOR ( 0 to 0 );
    S_AXI_wstrb : in STD_LOGIC_VECTOR ( 3 downto 0 );
    S_AXI_wvalid : in STD_LOGIC_VECTOR ( 0 to 0 )
  );
end m00_couplers_imp_1R706YB;

architecture STRUCTURE of m00_couplers_imp_1R706YB is
  signal m00_couplers_to_m00_couplers_ARADDR : STD_LOGIC_VECTOR ( 31 downto 0 );
  signal m00_couplers_to_m00_couplers_ARBURST : STD_LOGIC_VECTOR ( 1 downto 0 );
  signal m00_couplers_to_m00_couplers_ARCACHE : STD_LOGIC_VECTOR ( 3 downto 0 );
  signal m00_couplers_to_m00_couplers_ARID : STD_LOGIC_VECTOR ( 0 to 0 );
  signal m00_couplers_to_m00_couplers_ARLEN : STD_LOGIC_VECTOR ( 7 downto 0 );
  signal m00_couplers_to_m00_couplers_ARLOCK : STD_LOGIC_VECTOR ( 0 to 0 );
  signal m00_couplers_to_m00_couplers_ARPROT : STD_LOGIC_VECTOR ( 2 downto 0 );
  signal m00_couplers_to_m00_couplers_ARREADY : STD_LOGIC_VECTOR ( 0 to 0 );
  signal m00_couplers_to_m00_couplers_ARSIZE : STD_LOGIC_VECTOR ( 2 downto 0 );
  signal m00_couplers_to_m00_couplers_ARVALID : STD_LOGIC_VECTOR ( 0 to 0 );
  signal m00_couplers_to_m00_couplers_AWADDR : STD_LOGIC_VECTOR ( 31 downto 0 );
  signal m00_couplers_to_m00_couplers_AWBURST : STD_LOGIC_VECTOR ( 1 downto 0 );
  signal m00_couplers_to_m00_couplers_AWCACHE : STD_LOGIC_VECTOR ( 3 downto 0 );
  signal m00_couplers_to_m00_couplers_AWID : STD_LOGIC_VECTOR ( 0 to 0 );
  signal m00_couplers_to_m00_couplers_AWLEN : STD_LOGIC_VECTOR ( 7 downto 0 );
  signal m00_couplers_to_m00_couplers_AWLOCK : STD_LOGIC_VECTOR ( 0 to 0 );
  signal m00_couplers_to_m00_couplers_AWPROT : STD_LOGIC_VECTOR ( 2 downto 0 );
  signal m00_couplers_to_m00_couplers_AWREADY : STD_LOGIC_VECTOR ( 0 to 0 );
  signal m00_couplers_to_m00_couplers_AWSIZE : STD_LOGIC_VECTOR ( 2 downto 0 );
  signal m00_couplers_to_m00_couplers_AWVALID : STD_LOGIC_VECTOR ( 0 to 0 );
  signal m00_couplers_to_m00_couplers_BID : STD_LOGIC_VECTOR ( 0 to 0 );
  signal m00_couplers_to_m00_couplers_BREADY : STD_LOGIC_VECTOR ( 0 to 0 );
  signal m00_couplers_to_m00_couplers_BRESP : STD_LOGIC_VECTOR ( 1 downto 0 );
  signal m00_couplers_to_m00_couplers_BVALID : STD_LOGIC_VECTOR ( 0 to 0 );
  signal m00_couplers_to_m00_couplers_RDATA : STD_LOGIC_VECTOR ( 31 downto 0 );
  signal m00_couplers_to_m00_couplers_RID : STD_LOGIC_VECTOR ( 0 to 0 );
  signal m00_couplers_to_m00_couplers_RLAST : STD_LOGIC_VECTOR ( 0 to 0 );
  signal m00_couplers_to_m00_couplers_RREADY : STD_LOGIC_VECTOR ( 0 to 0 );
  signal m00_couplers_to_m00_couplers_RRESP : STD_LOGIC_VECTOR ( 1 downto 0 );
  signal m00_couplers_to_m00_couplers_RVALID : STD_LOGIC_VECTOR ( 0 to 0 );
  signal m00_couplers_to_m00_couplers_WDATA : STD_LOGIC_VECTOR ( 31 downto 0 );
  signal m00_couplers_to_m00_couplers_WLAST : STD_LOGIC_VECTOR ( 0 to 0 );
  signal m00_couplers_to_m00_couplers_WREADY : STD_LOGIC_VECTOR ( 0 to 0 );
  signal m00_couplers_to_m00_couplers_WSTRB : STD_LOGIC_VECTOR ( 3 downto 0 );
  signal m00_couplers_to_m00_couplers_WVALID : STD_LOGIC_VECTOR ( 0 to 0 );
begin
  M_AXI_araddr(31 downto 0) <= m00_couplers_to_m00_couplers_ARADDR(31 downto 0);
  M_AXI_arburst(1 downto 0) <= m00_couplers_to_m00_couplers_ARBURST(1 downto 0);
  M_AXI_arcache(3 downto 0) <= m00_couplers_to_m00_couplers_ARCACHE(3 downto 0);
  M_AXI_arid(0) <= m00_couplers_to_m00_couplers_ARID(0);
  M_AXI_arlen(7 downto 0) <= m00_couplers_to_m00_couplers_ARLEN(7 downto 0);
  M_AXI_arlock(0) <= m00_couplers_to_m00_couplers_ARLOCK(0);
  M_AXI_arprot(2 downto 0) <= m00_couplers_to_m00_couplers_ARPROT(2 downto 0);
  M_AXI_arsize(2 downto 0) <= m00_couplers_to_m00_couplers_ARSIZE(2 downto 0);
  M_AXI_arvalid(0) <= m00_couplers_to_m00_couplers_ARVALID(0);
  M_AXI_awaddr(31 downto 0) <= m00_couplers_to_m00_couplers_AWADDR(31 downto 0);
  M_AXI_awburst(1 downto 0) <= m00_couplers_to_m00_couplers_AWBURST(1 downto 0);
  M_AXI_awcache(3 downto 0) <= m00_couplers_to_m00_couplers_AWCACHE(3 downto 0);
  M_AXI_awid(0) <= m00_couplers_to_m00_couplers_AWID(0);
  M_AXI_awlen(7 downto 0) <= m00_couplers_to_m00_couplers_AWLEN(7 downto 0);
  M_AXI_awlock(0) <= m00_couplers_to_m00_couplers_AWLOCK(0);
  M_AXI_awprot(2 downto 0) <= m00_couplers_to_m00_couplers_AWPROT(2 downto 0);
  M_AXI_awsize(2 downto 0) <= m00_couplers_to_m00_couplers_AWSIZE(2 downto 0);
  M_AXI_awvalid(0) <= m00_couplers_to_m00_couplers_AWVALID(0);
  M_AXI_bready(0) <= m00_couplers_to_m00_couplers_BREADY(0);
  M_AXI_rready(0) <= m00_couplers_to_m00_couplers_RREADY(0);
  M_AXI_wdata(31 downto 0) <= m00_couplers_to_m00_couplers_WDATA(31 downto 0);
  M_AXI_wlast(0) <= m00_couplers_to_m00_couplers_WLAST(0);
  M_AXI_wstrb(3 downto 0) <= m00_couplers_to_m00_couplers_WSTRB(3 downto 0);
  M_AXI_wvalid(0) <= m00_couplers_to_m00_couplers_WVALID(0);
  S_AXI_arready(0) <= m00_couplers_to_m00_couplers_ARREADY(0);
  S_AXI_awready(0) <= m00_couplers_to_m00_couplers_AWREADY(0);
  S_AXI_bid(0) <= m00_couplers_to_m00_couplers_BID(0);
  S_AXI_bresp(1 downto 0) <= m00_couplers_to_m00_couplers_BRESP(1 downto 0);
  S_AXI_bvalid(0) <= m00_couplers_to_m00_couplers_BVALID(0);
  S_AXI_rdata(31 downto 0) <= m00_couplers_to_m00_couplers_RDATA(31 downto 0);
  S_AXI_rid(0) <= m00_couplers_to_m00_couplers_RID(0);
  S_AXI_rlast(0) <= m00_couplers_to_m00_couplers_RLAST(0);
  S_AXI_rresp(1 downto 0) <= m00_couplers_to_m00_couplers_RRESP(1 downto 0);
  S_AXI_rvalid(0) <= m00_couplers_to_m00_couplers_RVALID(0);
  S_AXI_wready(0) <= m00_couplers_to_m00_couplers_WREADY(0);
  m00_couplers_to_m00_couplers_ARADDR(31 downto 0) <= S_AXI_araddr(31 downto 0);
  m00_couplers_to_m00_couplers_ARBURST(1 downto 0) <= S_AXI_arburst(1 downto 0);
  m00_couplers_to_m00_couplers_ARCACHE(3 downto 0) <= S_AXI_arcache(3 downto 0);
  m00_couplers_to_m00_couplers_ARID(0) <= S_AXI_arid(0);
  m00_couplers_to_m00_couplers_ARLEN(7 downto 0) <= S_AXI_arlen(7 downto 0);
  m00_couplers_to_m00_couplers_ARLOCK(0) <= S_AXI_arlock(0);
  m00_couplers_to_m00_couplers_ARPROT(2 downto 0) <= S_AXI_arprot(2 downto 0);
  m00_couplers_to_m00_couplers_ARREADY(0) <= M_AXI_arready(0);
  m00_couplers_to_m00_couplers_ARSIZE(2 downto 0) <= S_AXI_arsize(2 downto 0);
  m00_couplers_to_m00_couplers_ARVALID(0) <= S_AXI_arvalid(0);
  m00_couplers_to_m00_couplers_AWADDR(31 downto 0) <= S_AXI_awaddr(31 downto 0);
  m00_couplers_to_m00_couplers_AWBURST(1 downto 0) <= S_AXI_awburst(1 downto 0);
  m00_couplers_to_m00_couplers_AWCACHE(3 downto 0) <= S_AXI_awcache(3 downto 0);
  m00_couplers_to_m00_couplers_AWID(0) <= S_AXI_awid(0);
  m00_couplers_to_m00_couplers_AWLEN(7 downto 0) <= S_AXI_awlen(7 downto 0);
  m00_couplers_to_m00_couplers_AWLOCK(0) <= S_AXI_awlock(0);
  m00_couplers_to_m00_couplers_AWPROT(2 downto 0) <= S_AXI_awprot(2 downto 0);
  m00_couplers_to_m00_couplers_AWREADY(0) <= M_AXI_awready(0);
  m00_couplers_to_m00_couplers_AWSIZE(2 downto 0) <= S_AXI_awsize(2 downto 0);
  m00_couplers_to_m00_couplers_AWVALID(0) <= S_AXI_awvalid(0);
  m00_couplers_to_m00_couplers_BID(0) <= M_AXI_bid(0);
  m00_couplers_to_m00_couplers_BREADY(0) <= S_AXI_bready(0);
  m00_couplers_to_m00_couplers_BRESP(1 downto 0) <= M_AXI_bresp(1 downto 0);
  m00_couplers_to_m00_couplers_BVALID(0) <= M_AXI_bvalid(0);
  m00_couplers_to_m00_couplers_RDATA(31 downto 0) <= M_AXI_rdata(31 downto 0);
  m00_couplers_to_m00_couplers_RID(0) <= M_AXI_rid(0);
  m00_couplers_to_m00_couplers_RLAST(0) <= M_AXI_rlast(0);
  m00_couplers_to_m00_couplers_RREADY(0) <= S_AXI_rready(0);
  m00_couplers_to_m00_couplers_RRESP(1 downto 0) <= M_AXI_rresp(1 downto 0);
  m00_couplers_to_m00_couplers_RVALID(0) <= M_AXI_rvalid(0);
  m00_couplers_to_m00_couplers_WDATA(31 downto 0) <= S_AXI_wdata(31 downto 0);
  m00_couplers_to_m00_couplers_WLAST(0) <= S_AXI_wlast(0);
  m00_couplers_to_m00_couplers_WREADY(0) <= M_AXI_wready(0);
  m00_couplers_to_m00_couplers_WSTRB(3 downto 0) <= S_AXI_wstrb(3 downto 0);
  m00_couplers_to_m00_couplers_WVALID(0) <= S_AXI_wvalid(0);
end STRUCTURE;
library IEEE;
use IEEE.STD_LOGIC_1164.ALL;
library UNISIM;
use UNISIM.VCOMPONENTS.ALL;
entity m00_couplers_imp_8RVYHO is
  port (
    M_ACLK : in STD_LOGIC;
    M_ARESETN : in STD_LOGIC_VECTOR ( 0 to 0 );
    M_AXI_araddr : out STD_LOGIC_VECTOR ( 8 downto 0 );
    M_AXI_arready : in STD_LOGIC;
    M_AXI_arvalid : out STD_LOGIC;
    M_AXI_awaddr : out STD_LOGIC_VECTOR ( 8 downto 0 );
    M_AXI_awready : in STD_LOGIC;
    M_AXI_awvalid : out STD_LOGIC;
    M_AXI_bready : out STD_LOGIC;
    M_AXI_bresp : in STD_LOGIC_VECTOR ( 1 downto 0 );
    M_AXI_bvalid : in STD_LOGIC;
    M_AXI_rdata : in STD_LOGIC_VECTOR ( 31 downto 0 );
    M_AXI_rready : out STD_LOGIC;
    M_AXI_rresp : in STD_LOGIC_VECTOR ( 1 downto 0 );
    M_AXI_rvalid : in STD_LOGIC;
    M_AXI_wdata : out STD_LOGIC_VECTOR ( 31 downto 0 );
    M_AXI_wready : in STD_LOGIC;
    M_AXI_wstrb : out STD_LOGIC_VECTOR ( 3 downto 0 );
    M_AXI_wvalid : out STD_LOGIC;
    S_ACLK : in STD_LOGIC;
    S_ARESETN : in STD_LOGIC_VECTOR ( 0 to 0 );
    S_AXI_araddr : in STD_LOGIC_VECTOR ( 8 downto 0 );
    S_AXI_arready : out STD_LOGIC;
    S_AXI_arvalid : in STD_LOGIC;
    S_AXI_awaddr : in STD_LOGIC_VECTOR ( 8 downto 0 );
    S_AXI_awready : out STD_LOGIC;
    S_AXI_awvalid : in STD_LOGIC;
    S_AXI_bready : in STD_LOGIC;
    S_AXI_bresp : out STD_LOGIC_VECTOR ( 1 downto 0 );
    S_AXI_bvalid : out STD_LOGIC;
    S_AXI_rdata : out STD_LOGIC_VECTOR ( 31 downto 0 );
    S_AXI_rready : in STD_LOGIC;
    S_AXI_rresp : out STD_LOGIC_VECTOR ( 1 downto 0 );
    S_AXI_rvalid : out STD_LOGIC;
    S_AXI_wdata : in STD_LOGIC_VECTOR ( 31 downto 0 );
    S_AXI_wready : out STD_LOGIC;
    S_AXI_wstrb : in STD_LOGIC_VECTOR ( 3 downto 0 );
    S_AXI_wvalid : in STD_LOGIC
  );
end m00_couplers_imp_8RVYHO;

architecture STRUCTURE of m00_couplers_imp_8RVYHO is
  signal m00_couplers_to_m00_couplers_ARADDR : STD_LOGIC_VECTOR ( 8 downto 0 );
  signal m00_couplers_to_m00_couplers_ARREADY : STD_LOGIC;
  signal m00_couplers_to_m00_couplers_ARVALID : STD_LOGIC;
  signal m00_couplers_to_m00_couplers_AWADDR : STD_LOGIC_VECTOR ( 8 downto 0 );
  signal m00_couplers_to_m00_couplers_AWREADY : STD_LOGIC;
  signal m00_couplers_to_m00_couplers_AWVALID : STD_LOGIC;
  signal m00_couplers_to_m00_couplers_BREADY : STD_LOGIC;
  signal m00_couplers_to_m00_couplers_BRESP : STD_LOGIC_VECTOR ( 1 downto 0 );
  signal m00_couplers_to_m00_couplers_BVALID : STD_LOGIC;
  signal m00_couplers_to_m00_couplers_RDATA : STD_LOGIC_VECTOR ( 31 downto 0 );
  signal m00_couplers_to_m00_couplers_RREADY : STD_LOGIC;
  signal m00_couplers_to_m00_couplers_RRESP : STD_LOGIC_VECTOR ( 1 downto 0 );
  signal m00_couplers_to_m00_couplers_RVALID : STD_LOGIC;
  signal m00_couplers_to_m00_couplers_WDATA : STD_LOGIC_VECTOR ( 31 downto 0 );
  signal m00_couplers_to_m00_couplers_WREADY : STD_LOGIC;
  signal m00_couplers_to_m00_couplers_WSTRB : STD_LOGIC_VECTOR ( 3 downto 0 );
  signal m00_couplers_to_m00_couplers_WVALID : STD_LOGIC;
begin
  M_AXI_araddr(8 downto 0) <= m00_couplers_to_m00_couplers_ARADDR(8 downto 0);
  M_AXI_arvalid <= m00_couplers_to_m00_couplers_ARVALID;
  M_AXI_awaddr(8 downto 0) <= m00_couplers_to_m00_couplers_AWADDR(8 downto 0);
  M_AXI_awvalid <= m00_couplers_to_m00_couplers_AWVALID;
  M_AXI_bready <= m00_couplers_to_m00_couplers_BREADY;
  M_AXI_rready <= m00_couplers_to_m00_couplers_RREADY;
  M_AXI_wdata(31 downto 0) <= m00_couplers_to_m00_couplers_WDATA(31 downto 0);
  M_AXI_wstrb(3 downto 0) <= m00_couplers_to_m00_couplers_WSTRB(3 downto 0);
  M_AXI_wvalid <= m00_couplers_to_m00_couplers_WVALID;
  S_AXI_arready <= m00_couplers_to_m00_couplers_ARREADY;
  S_AXI_awready <= m00_couplers_to_m00_couplers_AWREADY;
  S_AXI_bresp(1 downto 0) <= m00_couplers_to_m00_couplers_BRESP(1 downto 0);
  S_AXI_bvalid <= m00_couplers_to_m00_couplers_BVALID;
  S_AXI_rdata(31 downto 0) <= m00_couplers_to_m00_couplers_RDATA(31 downto 0);
  S_AXI_rresp(1 downto 0) <= m00_couplers_to_m00_couplers_RRESP(1 downto 0);
  S_AXI_rvalid <= m00_couplers_to_m00_couplers_RVALID;
  S_AXI_wready <= m00_couplers_to_m00_couplers_WREADY;
  m00_couplers_to_m00_couplers_ARADDR(8 downto 0) <= S_AXI_araddr(8 downto 0);
  m00_couplers_to_m00_couplers_ARREADY <= M_AXI_arready;
  m00_couplers_to_m00_couplers_ARVALID <= S_AXI_arvalid;
  m00_couplers_to_m00_couplers_AWADDR(8 downto 0) <= S_AXI_awaddr(8 downto 0);
  m00_couplers_to_m00_couplers_AWREADY <= M_AXI_awready;
  m00_couplers_to_m00_couplers_AWVALID <= S_AXI_awvalid;
  m00_couplers_to_m00_couplers_BREADY <= S_AXI_bready;
  m00_couplers_to_m00_couplers_BRESP(1 downto 0) <= M_AXI_bresp(1 downto 0);
  m00_couplers_to_m00_couplers_BVALID <= M_AXI_bvalid;
  m00_couplers_to_m00_couplers_RDATA(31 downto 0) <= M_AXI_rdata(31 downto 0);
  m00_couplers_to_m00_couplers_RREADY <= S_AXI_rready;
  m00_couplers_to_m00_couplers_RRESP(1 downto 0) <= M_AXI_rresp(1 downto 0);
  m00_couplers_to_m00_couplers_RVALID <= M_AXI_rvalid;
  m00_couplers_to_m00_couplers_WDATA(31 downto 0) <= S_AXI_wdata(31 downto 0);
  m00_couplers_to_m00_couplers_WREADY <= M_AXI_wready;
  m00_couplers_to_m00_couplers_WSTRB(3 downto 0) <= S_AXI_wstrb(3 downto 0);
  m00_couplers_to_m00_couplers_WVALID <= S_AXI_wvalid;
end STRUCTURE;
library IEEE;
use IEEE.STD_LOGIC_1164.ALL;
library UNISIM;
use UNISIM.VCOMPONENTS.ALL;
entity m01_couplers_imp_1UTB3Y5 is
  port (
    M_ACLK : in STD_LOGIC;
    M_ARESETN : in STD_LOGIC_VECTOR ( 0 to 0 );
    M_AXI_araddr : out STD_LOGIC_VECTOR ( 3 downto 0 );
    M_AXI_arready : in STD_LOGIC;
    M_AXI_arvalid : out STD_LOGIC;
    M_AXI_awaddr : out STD_LOGIC_VECTOR ( 3 downto 0 );
    M_AXI_awready : in STD_LOGIC;
    M_AXI_awvalid : out STD_LOGIC;
    M_AXI_bready : out STD_LOGIC;
    M_AXI_bresp : in STD_LOGIC_VECTOR ( 1 downto 0 );
    M_AXI_bvalid : in STD_LOGIC;
    M_AXI_rdata : in STD_LOGIC_VECTOR ( 31 downto 0 );
    M_AXI_rready : out STD_LOGIC;
    M_AXI_rresp : in STD_LOGIC_VECTOR ( 1 downto 0 );
    M_AXI_rvalid : in STD_LOGIC;
    M_AXI_wdata : out STD_LOGIC_VECTOR ( 31 downto 0 );
    M_AXI_wready : in STD_LOGIC;
    M_AXI_wstrb : out STD_LOGIC_VECTOR ( 3 downto 0 );
    M_AXI_wvalid : out STD_LOGIC;
    S_ACLK : in STD_LOGIC;
    S_ARESETN : in STD_LOGIC_VECTOR ( 0 to 0 );
    S_AXI_araddr : in STD_LOGIC_VECTOR ( 3 downto 0 );
    S_AXI_arready : out STD_LOGIC;
    S_AXI_arvalid : in STD_LOGIC;
    S_AXI_awaddr : in STD_LOGIC_VECTOR ( 3 downto 0 );
    S_AXI_awready : out STD_LOGIC;
    S_AXI_awvalid : in STD_LOGIC;
    S_AXI_bready : in STD_LOGIC;
    S_AXI_bresp : out STD_LOGIC_VECTOR ( 1 downto 0 );
    S_AXI_bvalid : out STD_LOGIC;
    S_AXI_rdata : out STD_LOGIC_VECTOR ( 31 downto 0 );
    S_AXI_rready : in STD_LOGIC;
    S_AXI_rresp : out STD_LOGIC_VECTOR ( 1 downto 0 );
    S_AXI_rvalid : out STD_LOGIC;
    S_AXI_wdata : in STD_LOGIC_VECTOR ( 31 downto 0 );
    S_AXI_wready : out STD_LOGIC;
    S_AXI_wstrb : in STD_LOGIC_VECTOR ( 3 downto 0 );
    S_AXI_wvalid : in STD_LOGIC
  );
end m01_couplers_imp_1UTB3Y5;

architecture STRUCTURE of m01_couplers_imp_1UTB3Y5 is
  signal m01_couplers_to_m01_couplers_ARADDR : STD_LOGIC_VECTOR ( 3 downto 0 );
  signal m01_couplers_to_m01_couplers_ARREADY : STD_LOGIC;
  signal m01_couplers_to_m01_couplers_ARVALID : STD_LOGIC;
  signal m01_couplers_to_m01_couplers_AWADDR : STD_LOGIC_VECTOR ( 3 downto 0 );
  signal m01_couplers_to_m01_couplers_AWREADY : STD_LOGIC;
  signal m01_couplers_to_m01_couplers_AWVALID : STD_LOGIC;
  signal m01_couplers_to_m01_couplers_BREADY : STD_LOGIC;
  signal m01_couplers_to_m01_couplers_BRESP : STD_LOGIC_VECTOR ( 1 downto 0 );
  signal m01_couplers_to_m01_couplers_BVALID : STD_LOGIC;
  signal m01_couplers_to_m01_couplers_RDATA : STD_LOGIC_VECTOR ( 31 downto 0 );
  signal m01_couplers_to_m01_couplers_RREADY : STD_LOGIC;
  signal m01_couplers_to_m01_couplers_RRESP : STD_LOGIC_VECTOR ( 1 downto 0 );
  signal m01_couplers_to_m01_couplers_RVALID : STD_LOGIC;
  signal m01_couplers_to_m01_couplers_WDATA : STD_LOGIC_VECTOR ( 31 downto 0 );
  signal m01_couplers_to_m01_couplers_WREADY : STD_LOGIC;
  signal m01_couplers_to_m01_couplers_WSTRB : STD_LOGIC_VECTOR ( 3 downto 0 );
  signal m01_couplers_to_m01_couplers_WVALID : STD_LOGIC;
begin
  M_AXI_araddr(3 downto 0) <= m01_couplers_to_m01_couplers_ARADDR(3 downto 0);
  M_AXI_arvalid <= m01_couplers_to_m01_couplers_ARVALID;
  M_AXI_awaddr(3 downto 0) <= m01_couplers_to_m01_couplers_AWADDR(3 downto 0);
  M_AXI_awvalid <= m01_couplers_to_m01_couplers_AWVALID;
  M_AXI_bready <= m01_couplers_to_m01_couplers_BREADY;
  M_AXI_rready <= m01_couplers_to_m01_couplers_RREADY;
  M_AXI_wdata(31 downto 0) <= m01_couplers_to_m01_couplers_WDATA(31 downto 0);
  M_AXI_wstrb(3 downto 0) <= m01_couplers_to_m01_couplers_WSTRB(3 downto 0);
  M_AXI_wvalid <= m01_couplers_to_m01_couplers_WVALID;
  S_AXI_arready <= m01_couplers_to_m01_couplers_ARREADY;
  S_AXI_awready <= m01_couplers_to_m01_couplers_AWREADY;
  S_AXI_bresp(1 downto 0) <= m01_couplers_to_m01_couplers_BRESP(1 downto 0);
  S_AXI_bvalid <= m01_couplers_to_m01_couplers_BVALID;
  S_AXI_rdata(31 downto 0) <= m01_couplers_to_m01_couplers_RDATA(31 downto 0);
  S_AXI_rresp(1 downto 0) <= m01_couplers_to_m01_couplers_RRESP(1 downto 0);
  S_AXI_rvalid <= m01_couplers_to_m01_couplers_RVALID;
  S_AXI_wready <= m01_couplers_to_m01_couplers_WREADY;
  m01_couplers_to_m01_couplers_ARADDR(3 downto 0) <= S_AXI_araddr(3 downto 0);
  m01_couplers_to_m01_couplers_ARREADY <= M_AXI_arready;
  m01_couplers_to_m01_couplers_ARVALID <= S_AXI_arvalid;
  m01_couplers_to_m01_couplers_AWADDR(3 downto 0) <= S_AXI_awaddr(3 downto 0);
  m01_couplers_to_m01_couplers_AWREADY <= M_AXI_awready;
  m01_couplers_to_m01_couplers_AWVALID <= S_AXI_awvalid;
  m01_couplers_to_m01_couplers_BREADY <= S_AXI_bready;
  m01_couplers_to_m01_couplers_BRESP(1 downto 0) <= M_AXI_bresp(1 downto 0);
  m01_couplers_to_m01_couplers_BVALID <= M_AXI_bvalid;
  m01_couplers_to_m01_couplers_RDATA(31 downto 0) <= M_AXI_rdata(31 downto 0);
  m01_couplers_to_m01_couplers_RREADY <= S_AXI_rready;
  m01_couplers_to_m01_couplers_RRESP(1 downto 0) <= M_AXI_rresp(1 downto 0);
  m01_couplers_to_m01_couplers_RVALID <= M_AXI_rvalid;
  m01_couplers_to_m01_couplers_WDATA(31 downto 0) <= S_AXI_wdata(31 downto 0);
  m01_couplers_to_m01_couplers_WREADY <= M_AXI_wready;
  m01_couplers_to_m01_couplers_WSTRB(3 downto 0) <= S_AXI_wstrb(3 downto 0);
  m01_couplers_to_m01_couplers_WVALID <= S_AXI_wvalid;
end STRUCTURE;
library IEEE;
use IEEE.STD_LOGIC_1164.ALL;
library UNISIM;
use UNISIM.VCOMPONENTS.ALL;
entity m02_couplers_imp_7ANRHB is
  port (
    M_ACLK : in STD_LOGIC;
    M_ARESETN : in STD_LOGIC_VECTOR ( 0 to 0 );
    M_AXI_araddr : out STD_LOGIC_VECTOR ( 12 downto 0 );
    M_AXI_arready : in STD_LOGIC;
    M_AXI_arvalid : out STD_LOGIC;
    M_AXI_awaddr : out STD_LOGIC_VECTOR ( 12 downto 0 );
    M_AXI_awready : in STD_LOGIC;
    M_AXI_awvalid : out STD_LOGIC;
    M_AXI_bready : out STD_LOGIC;
    M_AXI_bresp : in STD_LOGIC_VECTOR ( 1 downto 0 );
    M_AXI_bvalid : in STD_LOGIC;
    M_AXI_rdata : in STD_LOGIC_VECTOR ( 31 downto 0 );
    M_AXI_rready : out STD_LOGIC;
    M_AXI_rresp : in STD_LOGIC_VECTOR ( 1 downto 0 );
    M_AXI_rvalid : in STD_LOGIC;
    M_AXI_wdata : out STD_LOGIC_VECTOR ( 31 downto 0 );
    M_AXI_wready : in STD_LOGIC;
    M_AXI_wstrb : out STD_LOGIC_VECTOR ( 3 downto 0 );
    M_AXI_wvalid : out STD_LOGIC;
    S_ACLK : in STD_LOGIC;
    S_ARESETN : in STD_LOGIC_VECTOR ( 0 to 0 );
    S_AXI_araddr : in STD_LOGIC_VECTOR ( 12 downto 0 );
    S_AXI_arready : out STD_LOGIC;
    S_AXI_arvalid : in STD_LOGIC;
    S_AXI_awaddr : in STD_LOGIC_VECTOR ( 12 downto 0 );
    S_AXI_awready : out STD_LOGIC;
    S_AXI_awvalid : in STD_LOGIC;
    S_AXI_bready : in STD_LOGIC;
    S_AXI_bresp : out STD_LOGIC_VECTOR ( 1 downto 0 );
    S_AXI_bvalid : out STD_LOGIC;
    S_AXI_rdata : out STD_LOGIC_VECTOR ( 31 downto 0 );
    S_AXI_rready : in STD_LOGIC;
    S_AXI_rresp : out STD_LOGIC_VECTOR ( 1 downto 0 );
    S_AXI_rvalid : out STD_LOGIC;
    S_AXI_wdata : in STD_LOGIC_VECTOR ( 31 downto 0 );
    S_AXI_wready : out STD_LOGIC;
    S_AXI_wstrb : in STD_LOGIC_VECTOR ( 3 downto 0 );
    S_AXI_wvalid : in STD_LOGIC
  );
end m02_couplers_imp_7ANRHB;

architecture STRUCTURE of m02_couplers_imp_7ANRHB is
  signal m02_couplers_to_m02_couplers_ARADDR : STD_LOGIC_VECTOR ( 12 downto 0 );
  signal m02_couplers_to_m02_couplers_ARREADY : STD_LOGIC;
  signal m02_couplers_to_m02_couplers_ARVALID : STD_LOGIC;
  signal m02_couplers_to_m02_couplers_AWADDR : STD_LOGIC_VECTOR ( 12 downto 0 );
  signal m02_couplers_to_m02_couplers_AWREADY : STD_LOGIC;
  signal m02_couplers_to_m02_couplers_AWVALID : STD_LOGIC;
  signal m02_couplers_to_m02_couplers_BREADY : STD_LOGIC;
  signal m02_couplers_to_m02_couplers_BRESP : STD_LOGIC_VECTOR ( 1 downto 0 );
  signal m02_couplers_to_m02_couplers_BVALID : STD_LOGIC;
  signal m02_couplers_to_m02_couplers_RDATA : STD_LOGIC_VECTOR ( 31 downto 0 );
  signal m02_couplers_to_m02_couplers_RREADY : STD_LOGIC;
  signal m02_couplers_to_m02_couplers_RRESP : STD_LOGIC_VECTOR ( 1 downto 0 );
  signal m02_couplers_to_m02_couplers_RVALID : STD_LOGIC;
  signal m02_couplers_to_m02_couplers_WDATA : STD_LOGIC_VECTOR ( 31 downto 0 );
  signal m02_couplers_to_m02_couplers_WREADY : STD_LOGIC;
  signal m02_couplers_to_m02_couplers_WSTRB : STD_LOGIC_VECTOR ( 3 downto 0 );
  signal m02_couplers_to_m02_couplers_WVALID : STD_LOGIC;
begin
  M_AXI_araddr(12 downto 0) <= m02_couplers_to_m02_couplers_ARADDR(12 downto 0);
  M_AXI_arvalid <= m02_couplers_to_m02_couplers_ARVALID;
  M_AXI_awaddr(12 downto 0) <= m02_couplers_to_m02_couplers_AWADDR(12 downto 0);
  M_AXI_awvalid <= m02_couplers_to_m02_couplers_AWVALID;
  M_AXI_bready <= m02_couplers_to_m02_couplers_BREADY;
  M_AXI_rready <= m02_couplers_to_m02_couplers_RREADY;
  M_AXI_wdata(31 downto 0) <= m02_couplers_to_m02_couplers_WDATA(31 downto 0);
  M_AXI_wstrb(3 downto 0) <= m02_couplers_to_m02_couplers_WSTRB(3 downto 0);
  M_AXI_wvalid <= m02_couplers_to_m02_couplers_WVALID;
  S_AXI_arready <= m02_couplers_to_m02_couplers_ARREADY;
  S_AXI_awready <= m02_couplers_to_m02_couplers_AWREADY;
  S_AXI_bresp(1 downto 0) <= m02_couplers_to_m02_couplers_BRESP(1 downto 0);
  S_AXI_bvalid <= m02_couplers_to_m02_couplers_BVALID;
  S_AXI_rdata(31 downto 0) <= m02_couplers_to_m02_couplers_RDATA(31 downto 0);
  S_AXI_rresp(1 downto 0) <= m02_couplers_to_m02_couplers_RRESP(1 downto 0);
  S_AXI_rvalid <= m02_couplers_to_m02_couplers_RVALID;
  S_AXI_wready <= m02_couplers_to_m02_couplers_WREADY;
  m02_couplers_to_m02_couplers_ARADDR(12 downto 0) <= S_AXI_araddr(12 downto 0);
  m02_couplers_to_m02_couplers_ARREADY <= M_AXI_arready;
  m02_couplers_to_m02_couplers_ARVALID <= S_AXI_arvalid;
  m02_couplers_to_m02_couplers_AWADDR(12 downto 0) <= S_AXI_awaddr(12 downto 0);
  m02_couplers_to_m02_couplers_AWREADY <= M_AXI_awready;
  m02_couplers_to_m02_couplers_AWVALID <= S_AXI_awvalid;
  m02_couplers_to_m02_couplers_BREADY <= S_AXI_bready;
  m02_couplers_to_m02_couplers_BRESP(1 downto 0) <= M_AXI_bresp(1 downto 0);
  m02_couplers_to_m02_couplers_BVALID <= M_AXI_bvalid;
  m02_couplers_to_m02_couplers_RDATA(31 downto 0) <= M_AXI_rdata(31 downto 0);
  m02_couplers_to_m02_couplers_RREADY <= S_AXI_rready;
  m02_couplers_to_m02_couplers_RRESP(1 downto 0) <= M_AXI_rresp(1 downto 0);
  m02_couplers_to_m02_couplers_RVALID <= M_AXI_rvalid;
  m02_couplers_to_m02_couplers_WDATA(31 downto 0) <= S_AXI_wdata(31 downto 0);
  m02_couplers_to_m02_couplers_WREADY <= M_AXI_wready;
  m02_couplers_to_m02_couplers_WSTRB(3 downto 0) <= S_AXI_wstrb(3 downto 0);
  m02_couplers_to_m02_couplers_WVALID <= S_AXI_wvalid;
end STRUCTURE;
library IEEE;
use IEEE.STD_LOGIC_1164.ALL;
library UNISIM;
use UNISIM.VCOMPONENTS.ALL;
entity m03_couplers_imp_1W07O72 is
  port (
    M_ACLK : in STD_LOGIC;
    M_ARESETN : in STD_LOGIC_VECTOR ( 0 to 0 );
    M_AXI_araddr : out STD_LOGIC_VECTOR ( 4 downto 0 );
    M_AXI_arready : in STD_LOGIC;
    M_AXI_arvalid : out STD_LOGIC;
    M_AXI_awaddr : out STD_LOGIC_VECTOR ( 4 downto 0 );
    M_AXI_awready : in STD_LOGIC;
    M_AXI_awvalid : out STD_LOGIC;
    M_AXI_bready : out STD_LOGIC;
    M_AXI_bresp : in STD_LOGIC_VECTOR ( 1 downto 0 );
    M_AXI_bvalid : in STD_LOGIC;
    M_AXI_rdata : in STD_LOGIC_VECTOR ( 31 downto 0 );
    M_AXI_rready : out STD_LOGIC;
    M_AXI_rresp : in STD_LOGIC_VECTOR ( 1 downto 0 );
    M_AXI_rvalid : in STD_LOGIC;
    M_AXI_wdata : out STD_LOGIC_VECTOR ( 31 downto 0 );
    M_AXI_wready : in STD_LOGIC;
    M_AXI_wstrb : out STD_LOGIC_VECTOR ( 3 downto 0 );
    M_AXI_wvalid : out STD_LOGIC;
    S_ACLK : in STD_LOGIC;
    S_ARESETN : in STD_LOGIC_VECTOR ( 0 to 0 );
    S_AXI_araddr : in STD_LOGIC_VECTOR ( 4 downto 0 );
    S_AXI_arready : out STD_LOGIC;
    S_AXI_arvalid : in STD_LOGIC;
    S_AXI_awaddr : in STD_LOGIC_VECTOR ( 4 downto 0 );
    S_AXI_awready : out STD_LOGIC;
    S_AXI_awvalid : in STD_LOGIC;
    S_AXI_bready : in STD_LOGIC;
    S_AXI_bresp : out STD_LOGIC_VECTOR ( 1 downto 0 );
    S_AXI_bvalid : out STD_LOGIC;
    S_AXI_rdata : out STD_LOGIC_VECTOR ( 31 downto 0 );
    S_AXI_rready : in STD_LOGIC;
    S_AXI_rresp : out STD_LOGIC_VECTOR ( 1 downto 0 );
    S_AXI_rvalid : out STD_LOGIC;
    S_AXI_wdata : in STD_LOGIC_VECTOR ( 31 downto 0 );
    S_AXI_wready : out STD_LOGIC;
    S_AXI_wstrb : in STD_LOGIC_VECTOR ( 3 downto 0 );
    S_AXI_wvalid : in STD_LOGIC
  );
end m03_couplers_imp_1W07O72;

architecture STRUCTURE of m03_couplers_imp_1W07O72 is
  signal m03_couplers_to_m03_couplers_ARADDR : STD_LOGIC_VECTOR ( 4 downto 0 );
  signal m03_couplers_to_m03_couplers_ARREADY : STD_LOGIC;
  signal m03_couplers_to_m03_couplers_ARVALID : STD_LOGIC;
  signal m03_couplers_to_m03_couplers_AWADDR : STD_LOGIC_VECTOR ( 4 downto 0 );
  signal m03_couplers_to_m03_couplers_AWREADY : STD_LOGIC;
  signal m03_couplers_to_m03_couplers_AWVALID : STD_LOGIC;
  signal m03_couplers_to_m03_couplers_BREADY : STD_LOGIC;
  signal m03_couplers_to_m03_couplers_BRESP : STD_LOGIC_VECTOR ( 1 downto 0 );
  signal m03_couplers_to_m03_couplers_BVALID : STD_LOGIC;
  signal m03_couplers_to_m03_couplers_RDATA : STD_LOGIC_VECTOR ( 31 downto 0 );
  signal m03_couplers_to_m03_couplers_RREADY : STD_LOGIC;
  signal m03_couplers_to_m03_couplers_RRESP : STD_LOGIC_VECTOR ( 1 downto 0 );
  signal m03_couplers_to_m03_couplers_RVALID : STD_LOGIC;
  signal m03_couplers_to_m03_couplers_WDATA : STD_LOGIC_VECTOR ( 31 downto 0 );
  signal m03_couplers_to_m03_couplers_WREADY : STD_LOGIC;
  signal m03_couplers_to_m03_couplers_WSTRB : STD_LOGIC_VECTOR ( 3 downto 0 );
  signal m03_couplers_to_m03_couplers_WVALID : STD_LOGIC;
begin
  M_AXI_araddr(4 downto 0) <= m03_couplers_to_m03_couplers_ARADDR(4 downto 0);
  M_AXI_arvalid <= m03_couplers_to_m03_couplers_ARVALID;
  M_AXI_awaddr(4 downto 0) <= m03_couplers_to_m03_couplers_AWADDR(4 downto 0);
  M_AXI_awvalid <= m03_couplers_to_m03_couplers_AWVALID;
  M_AXI_bready <= m03_couplers_to_m03_couplers_BREADY;
  M_AXI_rready <= m03_couplers_to_m03_couplers_RREADY;
  M_AXI_wdata(31 downto 0) <= m03_couplers_to_m03_couplers_WDATA(31 downto 0);
  M_AXI_wstrb(3 downto 0) <= m03_couplers_to_m03_couplers_WSTRB(3 downto 0);
  M_AXI_wvalid <= m03_couplers_to_m03_couplers_WVALID;
  S_AXI_arready <= m03_couplers_to_m03_couplers_ARREADY;
  S_AXI_awready <= m03_couplers_to_m03_couplers_AWREADY;
  S_AXI_bresp(1 downto 0) <= m03_couplers_to_m03_couplers_BRESP(1 downto 0);
  S_AXI_bvalid <= m03_couplers_to_m03_couplers_BVALID;
  S_AXI_rdata(31 downto 0) <= m03_couplers_to_m03_couplers_RDATA(31 downto 0);
  S_AXI_rresp(1 downto 0) <= m03_couplers_to_m03_couplers_RRESP(1 downto 0);
  S_AXI_rvalid <= m03_couplers_to_m03_couplers_RVALID;
  S_AXI_wready <= m03_couplers_to_m03_couplers_WREADY;
  m03_couplers_to_m03_couplers_ARADDR(4 downto 0) <= S_AXI_araddr(4 downto 0);
  m03_couplers_to_m03_couplers_ARREADY <= M_AXI_arready;
  m03_couplers_to_m03_couplers_ARVALID <= S_AXI_arvalid;
  m03_couplers_to_m03_couplers_AWADDR(4 downto 0) <= S_AXI_awaddr(4 downto 0);
  m03_couplers_to_m03_couplers_AWREADY <= M_AXI_awready;
  m03_couplers_to_m03_couplers_AWVALID <= S_AXI_awvalid;
  m03_couplers_to_m03_couplers_BREADY <= S_AXI_bready;
  m03_couplers_to_m03_couplers_BRESP(1 downto 0) <= M_AXI_bresp(1 downto 0);
  m03_couplers_to_m03_couplers_BVALID <= M_AXI_bvalid;
  m03_couplers_to_m03_couplers_RDATA(31 downto 0) <= M_AXI_rdata(31 downto 0);
  m03_couplers_to_m03_couplers_RREADY <= S_AXI_rready;
  m03_couplers_to_m03_couplers_RRESP(1 downto 0) <= M_AXI_rresp(1 downto 0);
  m03_couplers_to_m03_couplers_RVALID <= M_AXI_rvalid;
  m03_couplers_to_m03_couplers_WDATA(31 downto 0) <= S_AXI_wdata(31 downto 0);
  m03_couplers_to_m03_couplers_WREADY <= M_AXI_wready;
  m03_couplers_to_m03_couplers_WSTRB(3 downto 0) <= S_AXI_wstrb(3 downto 0);
  m03_couplers_to_m03_couplers_WVALID <= S_AXI_wvalid;
end STRUCTURE;
library IEEE;
use IEEE.STD_LOGIC_1164.ALL;
library UNISIM;
use UNISIM.VCOMPONENTS.ALL;
entity microblaze_0_local_memory_imp_1K0VQXK is
  port (
    DLMB_abus : in STD_LOGIC_VECTOR ( 0 to 31 );
    DLMB_addrstrobe : in STD_LOGIC;
    DLMB_be : in STD_LOGIC_VECTOR ( 0 to 3 );
    DLMB_ce : out STD_LOGIC;
    DLMB_readdbus : out STD_LOGIC_VECTOR ( 0 to 31 );
    DLMB_readstrobe : in STD_LOGIC;
    DLMB_ready : out STD_LOGIC;
    DLMB_ue : out STD_LOGIC;
    DLMB_wait : out STD_LOGIC;
    DLMB_writedbus : in STD_LOGIC_VECTOR ( 0 to 31 );
    DLMB_writestrobe : in STD_LOGIC;
    ILMB_abus : in STD_LOGIC_VECTOR ( 0 to 31 );
    ILMB_addrstrobe : in STD_LOGIC;
    ILMB_ce : out STD_LOGIC;
    ILMB_readdbus : out STD_LOGIC_VECTOR ( 0 to 31 );
    ILMB_readstrobe : in STD_LOGIC;
    ILMB_ready : out STD_LOGIC;
    ILMB_ue : out STD_LOGIC;
    ILMB_wait : out STD_LOGIC;
    LMB_Clk : in STD_LOGIC;
    SYS_Rst : in STD_LOGIC_VECTOR ( 0 to 0 )
  );
end microblaze_0_local_memory_imp_1K0VQXK;

architecture STRUCTURE of microblaze_0_local_memory_imp_1K0VQXK is
  component design_1_dlmb_v10_0 is
  port (
    LMB_Clk : in STD_LOGIC;
    SYS_Rst : in STD_LOGIC;
    LMB_Rst : out STD_LOGIC;
    M_ABus : in STD_LOGIC_VECTOR ( 0 to 31 );
    M_ReadStrobe : in STD_LOGIC;
    M_WriteStrobe : in STD_LOGIC;
    M_AddrStrobe : in STD_LOGIC;
    M_DBus : in STD_LOGIC_VECTOR ( 0 to 31 );
    M_BE : in STD_LOGIC_VECTOR ( 0 to 3 );
    Sl_DBus : in STD_LOGIC_VECTOR ( 0 to 31 );
    Sl_Ready : in STD_LOGIC_VECTOR ( 0 to 0 );
    Sl_Wait : in STD_LOGIC_VECTOR ( 0 to 0 );
    Sl_UE : in STD_LOGIC_VECTOR ( 0 to 0 );
    Sl_CE : in STD_LOGIC_VECTOR ( 0 to 0 );
    LMB_ABus : out STD_LOGIC_VECTOR ( 0 to 31 );
    LMB_ReadStrobe : out STD_LOGIC;
    LMB_WriteStrobe : out STD_LOGIC;
    LMB_AddrStrobe : out STD_LOGIC;
    LMB_ReadDBus : out STD_LOGIC_VECTOR ( 0 to 31 );
    LMB_WriteDBus : out STD_LOGIC_VECTOR ( 0 to 31 );
    LMB_Ready : out STD_LOGIC;
    LMB_Wait : out STD_LOGIC;
    LMB_UE : out STD_LOGIC;
    LMB_CE : out STD_LOGIC;
    LMB_BE : out STD_LOGIC_VECTOR ( 0 to 3 )
  );
  end component design_1_dlmb_v10_0;
  component design_1_ilmb_v10_0 is
  port (
    LMB_Clk : in STD_LOGIC;
    SYS_Rst : in STD_LOGIC;
    LMB_Rst : out STD_LOGIC;
    M_ABus : in STD_LOGIC_VECTOR ( 0 to 31 );
    M_ReadStrobe : in STD_LOGIC;
    M_WriteStrobe : in STD_LOGIC;
    M_AddrStrobe : in STD_LOGIC;
    M_DBus : in STD_LOGIC_VECTOR ( 0 to 31 );
    M_BE : in STD_LOGIC_VECTOR ( 0 to 3 );
    Sl_DBus : in STD_LOGIC_VECTOR ( 0 to 31 );
    Sl_Ready : in STD_LOGIC_VECTOR ( 0 to 0 );
    Sl_Wait : in STD_LOGIC_VECTOR ( 0 to 0 );
    Sl_UE : in STD_LOGIC_VECTOR ( 0 to 0 );
    Sl_CE : in STD_LOGIC_VECTOR ( 0 to 0 );
    LMB_ABus : out STD_LOGIC_VECTOR ( 0 to 31 );
    LMB_ReadStrobe : out STD_LOGIC;
    LMB_WriteStrobe : out STD_LOGIC;
    LMB_AddrStrobe : out STD_LOGIC;
    LMB_ReadDBus : out STD_LOGIC_VECTOR ( 0 to 31 );
    LMB_WriteDBus : out STD_LOGIC_VECTOR ( 0 to 31 );
    LMB_Ready : out STD_LOGIC;
    LMB_Wait : out STD_LOGIC;
    LMB_UE : out STD_LOGIC;
    LMB_CE : out STD_LOGIC;
    LMB_BE : out STD_LOGIC_VECTOR ( 0 to 3 )
  );
  end component design_1_ilmb_v10_0;
  component design_1_dlmb_bram_if_cntlr_0 is
  port (
    LMB_Clk : in STD_LOGIC;
    LMB_Rst : in STD_LOGIC;
    LMB_ABus : in STD_LOGIC_VECTOR ( 0 to 31 );
    LMB_WriteDBus : in STD_LOGIC_VECTOR ( 0 to 31 );
    LMB_AddrStrobe : in STD_LOGIC;
    LMB_ReadStrobe : in STD_LOGIC;
    LMB_WriteStrobe : in STD_LOGIC;
    LMB_BE : in STD_LOGIC_VECTOR ( 0 to 3 );
    Sl_DBus : out STD_LOGIC_VECTOR ( 0 to 31 );
    Sl_Ready : out STD_LOGIC;
    Sl_Wait : out STD_LOGIC;
    Sl_UE : out STD_LOGIC;
    Sl_CE : out STD_LOGIC;
    BRAM_Rst_A : out STD_LOGIC;
    BRAM_Clk_A : out STD_LOGIC;
    BRAM_Addr_A : out STD_LOGIC_VECTOR ( 0 to 31 );
    BRAM_EN_A : out STD_LOGIC;
    BRAM_WEN_A : out STD_LOGIC_VECTOR ( 0 to 3 );
    BRAM_Dout_A : out STD_LOGIC_VECTOR ( 0 to 31 );
    BRAM_Din_A : in STD_LOGIC_VECTOR ( 0 to 31 )
  );
  end component design_1_dlmb_bram_if_cntlr_0;
  component design_1_ilmb_bram_if_cntlr_0 is
  port (
    LMB_Clk : in STD_LOGIC;
    LMB_Rst : in STD_LOGIC;
    LMB_ABus : in STD_LOGIC_VECTOR ( 0 to 31 );
    LMB_WriteDBus : in STD_LOGIC_VECTOR ( 0 to 31 );
    LMB_AddrStrobe : in STD_LOGIC;
    LMB_ReadStrobe : in STD_LOGIC;
    LMB_WriteStrobe : in STD_LOGIC;
    LMB_BE : in STD_LOGIC_VECTOR ( 0 to 3 );
    Sl_DBus : out STD_LOGIC_VECTOR ( 0 to 31 );
    Sl_Ready : out STD_LOGIC;
    Sl_Wait : out STD_LOGIC;
    Sl_UE : out STD_LOGIC;
    Sl_CE : out STD_LOGIC;
    BRAM_Rst_A : out STD_LOGIC;
    BRAM_Clk_A : out STD_LOGIC;
    BRAM_Addr_A : out STD_LOGIC_VECTOR ( 0 to 31 );
    BRAM_EN_A : out STD_LOGIC;
    BRAM_WEN_A : out STD_LOGIC_VECTOR ( 0 to 3 );
    BRAM_Dout_A : out STD_LOGIC_VECTOR ( 0 to 31 );
    BRAM_Din_A : in STD_LOGIC_VECTOR ( 0 to 31 )
  );
  end component design_1_ilmb_bram_if_cntlr_0;
  component design_1_lmb_bram_0 is
  port (
    clka : in STD_LOGIC;
    rsta : in STD_LOGIC;
    ena : in STD_LOGIC;
    wea : in STD_LOGIC_VECTOR ( 3 downto 0 );
    addra : in STD_LOGIC_VECTOR ( 31 downto 0 );
    dina : in STD_LOGIC_VECTOR ( 31 downto 0 );
    douta : out STD_LOGIC_VECTOR ( 31 downto 0 );
    clkb : in STD_LOGIC;
    rstb : in STD_LOGIC;
    enb : in STD_LOGIC;
    web : in STD_LOGIC_VECTOR ( 3 downto 0 );
    addrb : in STD_LOGIC_VECTOR ( 31 downto 0 );
    dinb : in STD_LOGIC_VECTOR ( 31 downto 0 );
    doutb : out STD_LOGIC_VECTOR ( 31 downto 0 )
  );
  end component design_1_lmb_bram_0;
  signal GND_1 : STD_LOGIC;
  signal SYS_Rst_1 : STD_LOGIC_VECTOR ( 0 to 0 );
  signal microblaze_0_Clk : STD_LOGIC;
  signal microblaze_0_dlmb_ABUS : STD_LOGIC_VECTOR ( 0 to 31 );
  signal microblaze_0_dlmb_ADDRSTROBE : STD_LOGIC;
  signal microblaze_0_dlmb_BE : STD_LOGIC_VECTOR ( 0 to 3 );
  signal microblaze_0_dlmb_CE : STD_LOGIC;
  signal microblaze_0_dlmb_READDBUS : STD_LOGIC_VECTOR ( 0 to 31 );
  signal microblaze_0_dlmb_READSTROBE : STD_LOGIC;
  signal microblaze_0_dlmb_READY : STD_LOGIC;
  signal microblaze_0_dlmb_UE : STD_LOGIC;
  signal microblaze_0_dlmb_WAIT : STD_LOGIC;
  signal microblaze_0_dlmb_WRITEDBUS : STD_LOGIC_VECTOR ( 0 to 31 );
  signal microblaze_0_dlmb_WRITESTROBE : STD_LOGIC;
  signal microblaze_0_dlmb_bus_ABUS : STD_LOGIC_VECTOR ( 0 to 31 );
  signal microblaze_0_dlmb_bus_ADDRSTROBE : STD_LOGIC;
  signal microblaze_0_dlmb_bus_BE : STD_LOGIC_VECTOR ( 0 to 3 );
  signal microblaze_0_dlmb_bus_CE : STD_LOGIC;
  signal microblaze_0_dlmb_bus_READDBUS : STD_LOGIC_VECTOR ( 0 to 31 );
  signal microblaze_0_dlmb_bus_READSTROBE : STD_LOGIC;
  signal microblaze_0_dlmb_bus_READY : STD_LOGIC;
  signal microblaze_0_dlmb_bus_UE : STD_LOGIC;
  signal microblaze_0_dlmb_bus_WAIT : STD_LOGIC;
  signal microblaze_0_dlmb_bus_WRITEDBUS : STD_LOGIC_VECTOR ( 0 to 31 );
  signal microblaze_0_dlmb_bus_WRITESTROBE : STD_LOGIC;
  signal microblaze_0_dlmb_cntlr_ADDR : STD_LOGIC_VECTOR ( 0 to 31 );
  signal microblaze_0_dlmb_cntlr_CLK : STD_LOGIC;
  signal microblaze_0_dlmb_cntlr_DIN : STD_LOGIC_VECTOR ( 0 to 31 );
  signal microblaze_0_dlmb_cntlr_DOUT : STD_LOGIC_VECTOR ( 31 downto 0 );
  signal microblaze_0_dlmb_cntlr_EN : STD_LOGIC;
  signal microblaze_0_dlmb_cntlr_RST : STD_LOGIC;
  signal microblaze_0_dlmb_cntlr_WE : STD_LOGIC_VECTOR ( 0 to 3 );
  signal microblaze_0_ilmb_ABUS : STD_LOGIC_VECTOR ( 0 to 31 );
  signal microblaze_0_ilmb_ADDRSTROBE : STD_LOGIC;
  signal microblaze_0_ilmb_CE : STD_LOGIC;
  signal microblaze_0_ilmb_READDBUS : STD_LOGIC_VECTOR ( 0 to 31 );
  signal microblaze_0_ilmb_READSTROBE : STD_LOGIC;
  signal microblaze_0_ilmb_READY : STD_LOGIC;
  signal microblaze_0_ilmb_UE : STD_LOGIC;
  signal microblaze_0_ilmb_WAIT : STD_LOGIC;
  signal microblaze_0_ilmb_bus_ABUS : STD_LOGIC_VECTOR ( 0 to 31 );
  signal microblaze_0_ilmb_bus_ADDRSTROBE : STD_LOGIC;
  signal microblaze_0_ilmb_bus_BE : STD_LOGIC_VECTOR ( 0 to 3 );
  signal microblaze_0_ilmb_bus_CE : STD_LOGIC;
  signal microblaze_0_ilmb_bus_READDBUS : STD_LOGIC_VECTOR ( 0 to 31 );
  signal microblaze_0_ilmb_bus_READSTROBE : STD_LOGIC;
  signal microblaze_0_ilmb_bus_READY : STD_LOGIC;
  signal microblaze_0_ilmb_bus_UE : STD_LOGIC;
  signal microblaze_0_ilmb_bus_WAIT : STD_LOGIC;
  signal microblaze_0_ilmb_bus_WRITEDBUS : STD_LOGIC_VECTOR ( 0 to 31 );
  signal microblaze_0_ilmb_bus_WRITESTROBE : STD_LOGIC;
  signal microblaze_0_ilmb_cntlr_ADDR : STD_LOGIC_VECTOR ( 0 to 31 );
  signal microblaze_0_ilmb_cntlr_CLK : STD_LOGIC;
  signal microblaze_0_ilmb_cntlr_DIN : STD_LOGIC_VECTOR ( 0 to 31 );
  signal microblaze_0_ilmb_cntlr_DOUT : STD_LOGIC_VECTOR ( 31 downto 0 );
  signal microblaze_0_ilmb_cntlr_EN : STD_LOGIC;
  signal microblaze_0_ilmb_cntlr_RST : STD_LOGIC;
  signal microblaze_0_ilmb_cntlr_WE : STD_LOGIC_VECTOR ( 0 to 3 );
  signal NLW_dlmb_v10_LMB_Rst_UNCONNECTED : STD_LOGIC;
  signal NLW_ilmb_v10_LMB_Rst_UNCONNECTED : STD_LOGIC;
  attribute BMM_INFO_ADDRESS_SPACE : string;
  attribute BMM_INFO_ADDRESS_SPACE of dlmb_bram_if_cntlr : label is "byte  0x0 32 >  design_1 microblaze_0_local_memory/lmb_bram";
  attribute KEEP_HIERARCHY : string;
  attribute KEEP_HIERARCHY of dlmb_bram_if_cntlr : label is "yes";
begin
  DLMB_ce <= microblaze_0_dlmb_CE;
  DLMB_readdbus(0 to 31) <= microblaze_0_dlmb_READDBUS(0 to 31);
  DLMB_ready <= microblaze_0_dlmb_READY;
  DLMB_ue <= microblaze_0_dlmb_UE;
  DLMB_wait <= microblaze_0_dlmb_WAIT;
  ILMB_ce <= microblaze_0_ilmb_CE;
  ILMB_readdbus(0 to 31) <= microblaze_0_ilmb_READDBUS(0 to 31);
  ILMB_ready <= microblaze_0_ilmb_READY;
  ILMB_ue <= microblaze_0_ilmb_UE;
  ILMB_wait <= microblaze_0_ilmb_WAIT;
  SYS_Rst_1(0) <= SYS_Rst(0);
  microblaze_0_Clk <= LMB_Clk;
  microblaze_0_dlmb_ABUS(0 to 31) <= DLMB_abus(0 to 31);
  microblaze_0_dlmb_ADDRSTROBE <= DLMB_addrstrobe;
  microblaze_0_dlmb_BE(0 to 3) <= DLMB_be(0 to 3);
  microblaze_0_dlmb_READSTROBE <= DLMB_readstrobe;
  microblaze_0_dlmb_WRITEDBUS(0 to 31) <= DLMB_writedbus(0 to 31);
  microblaze_0_dlmb_WRITESTROBE <= DLMB_writestrobe;
  microblaze_0_ilmb_ABUS(0 to 31) <= ILMB_abus(0 to 31);
  microblaze_0_ilmb_ADDRSTROBE <= ILMB_addrstrobe;
  microblaze_0_ilmb_READSTROBE <= ILMB_readstrobe;
GND: unisim.vcomponents.GND
     port map (
      G => GND_1
    );
dlmb_bram_if_cntlr: component design_1_dlmb_bram_if_cntlr_0
     port map (
      BRAM_Addr_A(0 to 31) => microblaze_0_dlmb_cntlr_ADDR(0 to 31),
      BRAM_Clk_A => microblaze_0_dlmb_cntlr_CLK,
      BRAM_Din_A(0) => microblaze_0_dlmb_cntlr_DOUT(31),
      BRAM_Din_A(1) => microblaze_0_dlmb_cntlr_DOUT(30),
      BRAM_Din_A(2) => microblaze_0_dlmb_cntlr_DOUT(29),
      BRAM_Din_A(3) => microblaze_0_dlmb_cntlr_DOUT(28),
      BRAM_Din_A(4) => microblaze_0_dlmb_cntlr_DOUT(27),
      BRAM_Din_A(5) => microblaze_0_dlmb_cntlr_DOUT(26),
      BRAM_Din_A(6) => microblaze_0_dlmb_cntlr_DOUT(25),
      BRAM_Din_A(7) => microblaze_0_dlmb_cntlr_DOUT(24),
      BRAM_Din_A(8) => microblaze_0_dlmb_cntlr_DOUT(23),
      BRAM_Din_A(9) => microblaze_0_dlmb_cntlr_DOUT(22),
      BRAM_Din_A(10) => microblaze_0_dlmb_cntlr_DOUT(21),
      BRAM_Din_A(11) => microblaze_0_dlmb_cntlr_DOUT(20),
      BRAM_Din_A(12) => microblaze_0_dlmb_cntlr_DOUT(19),
      BRAM_Din_A(13) => microblaze_0_dlmb_cntlr_DOUT(18),
      BRAM_Din_A(14) => microblaze_0_dlmb_cntlr_DOUT(17),
      BRAM_Din_A(15) => microblaze_0_dlmb_cntlr_DOUT(16),
      BRAM_Din_A(16) => microblaze_0_dlmb_cntlr_DOUT(15),
      BRAM_Din_A(17) => microblaze_0_dlmb_cntlr_DOUT(14),
      BRAM_Din_A(18) => microblaze_0_dlmb_cntlr_DOUT(13),
      BRAM_Din_A(19) => microblaze_0_dlmb_cntlr_DOUT(12),
      BRAM_Din_A(20) => microblaze_0_dlmb_cntlr_DOUT(11),
      BRAM_Din_A(21) => microblaze_0_dlmb_cntlr_DOUT(10),
      BRAM_Din_A(22) => microblaze_0_dlmb_cntlr_DOUT(9),
      BRAM_Din_A(23) => microblaze_0_dlmb_cntlr_DOUT(8),
      BRAM_Din_A(24) => microblaze_0_dlmb_cntlr_DOUT(7),
      BRAM_Din_A(25) => microblaze_0_dlmb_cntlr_DOUT(6),
      BRAM_Din_A(26) => microblaze_0_dlmb_cntlr_DOUT(5),
      BRAM_Din_A(27) => microblaze_0_dlmb_cntlr_DOUT(4),
      BRAM_Din_A(28) => microblaze_0_dlmb_cntlr_DOUT(3),
      BRAM_Din_A(29) => microblaze_0_dlmb_cntlr_DOUT(2),
      BRAM_Din_A(30) => microblaze_0_dlmb_cntlr_DOUT(1),
      BRAM_Din_A(31) => microblaze_0_dlmb_cntlr_DOUT(0),
      BRAM_Dout_A(0 to 31) => microblaze_0_dlmb_cntlr_DIN(0 to 31),
      BRAM_EN_A => microblaze_0_dlmb_cntlr_EN,
      BRAM_Rst_A => microblaze_0_dlmb_cntlr_RST,
      BRAM_WEN_A(0 to 3) => microblaze_0_dlmb_cntlr_WE(0 to 3),
      LMB_ABus(0 to 31) => microblaze_0_dlmb_bus_ABUS(0 to 31),
      LMB_AddrStrobe => microblaze_0_dlmb_bus_ADDRSTROBE,
      LMB_BE(0 to 3) => microblaze_0_dlmb_bus_BE(0 to 3),
      LMB_Clk => microblaze_0_Clk,
      LMB_ReadStrobe => microblaze_0_dlmb_bus_READSTROBE,
      LMB_Rst => SYS_Rst_1(0),
      LMB_WriteDBus(0 to 31) => microblaze_0_dlmb_bus_WRITEDBUS(0 to 31),
      LMB_WriteStrobe => microblaze_0_dlmb_bus_WRITESTROBE,
      Sl_CE => microblaze_0_dlmb_bus_CE,
      Sl_DBus(0 to 31) => microblaze_0_dlmb_bus_READDBUS(0 to 31),
      Sl_Ready => microblaze_0_dlmb_bus_READY,
      Sl_UE => microblaze_0_dlmb_bus_UE,
      Sl_Wait => microblaze_0_dlmb_bus_WAIT
    );
dlmb_v10: component design_1_dlmb_v10_0
     port map (
      LMB_ABus(0 to 31) => microblaze_0_dlmb_bus_ABUS(0 to 31),
      LMB_AddrStrobe => microblaze_0_dlmb_bus_ADDRSTROBE,
      LMB_BE(0 to 3) => microblaze_0_dlmb_bus_BE(0 to 3),
      LMB_CE => microblaze_0_dlmb_CE,
      LMB_Clk => microblaze_0_Clk,
      LMB_ReadDBus(0 to 31) => microblaze_0_dlmb_READDBUS(0 to 31),
      LMB_ReadStrobe => microblaze_0_dlmb_bus_READSTROBE,
      LMB_Ready => microblaze_0_dlmb_READY,
      LMB_Rst => NLW_dlmb_v10_LMB_Rst_UNCONNECTED,
      LMB_UE => microblaze_0_dlmb_UE,
      LMB_Wait => microblaze_0_dlmb_WAIT,
      LMB_WriteDBus(0 to 31) => microblaze_0_dlmb_bus_WRITEDBUS(0 to 31),
      LMB_WriteStrobe => microblaze_0_dlmb_bus_WRITESTROBE,
      M_ABus(0 to 31) => microblaze_0_dlmb_ABUS(0 to 31),
      M_AddrStrobe => microblaze_0_dlmb_ADDRSTROBE,
      M_BE(0 to 3) => microblaze_0_dlmb_BE(0 to 3),
      M_DBus(0 to 31) => microblaze_0_dlmb_WRITEDBUS(0 to 31),
      M_ReadStrobe => microblaze_0_dlmb_READSTROBE,
      M_WriteStrobe => microblaze_0_dlmb_WRITESTROBE,
      SYS_Rst => SYS_Rst_1(0),
      Sl_CE(0) => microblaze_0_dlmb_bus_CE,
      Sl_DBus(0 to 31) => microblaze_0_dlmb_bus_READDBUS(0 to 31),
      Sl_Ready(0) => microblaze_0_dlmb_bus_READY,
      Sl_UE(0) => microblaze_0_dlmb_bus_UE,
      Sl_Wait(0) => microblaze_0_dlmb_bus_WAIT
    );
ilmb_bram_if_cntlr: component design_1_ilmb_bram_if_cntlr_0
     port map (
      BRAM_Addr_A(0 to 31) => microblaze_0_ilmb_cntlr_ADDR(0 to 31),
      BRAM_Clk_A => microblaze_0_ilmb_cntlr_CLK,
      BRAM_Din_A(0) => microblaze_0_ilmb_cntlr_DOUT(31),
      BRAM_Din_A(1) => microblaze_0_ilmb_cntlr_DOUT(30),
      BRAM_Din_A(2) => microblaze_0_ilmb_cntlr_DOUT(29),
      BRAM_Din_A(3) => microblaze_0_ilmb_cntlr_DOUT(28),
      BRAM_Din_A(4) => microblaze_0_ilmb_cntlr_DOUT(27),
      BRAM_Din_A(5) => microblaze_0_ilmb_cntlr_DOUT(26),
      BRAM_Din_A(6) => microblaze_0_ilmb_cntlr_DOUT(25),
      BRAM_Din_A(7) => microblaze_0_ilmb_cntlr_DOUT(24),
      BRAM_Din_A(8) => microblaze_0_ilmb_cntlr_DOUT(23),
      BRAM_Din_A(9) => microblaze_0_ilmb_cntlr_DOUT(22),
      BRAM_Din_A(10) => microblaze_0_ilmb_cntlr_DOUT(21),
      BRAM_Din_A(11) => microblaze_0_ilmb_cntlr_DOUT(20),
      BRAM_Din_A(12) => microblaze_0_ilmb_cntlr_DOUT(19),
      BRAM_Din_A(13) => microblaze_0_ilmb_cntlr_DOUT(18),
      BRAM_Din_A(14) => microblaze_0_ilmb_cntlr_DOUT(17),
      BRAM_Din_A(15) => microblaze_0_ilmb_cntlr_DOUT(16),
      BRAM_Din_A(16) => microblaze_0_ilmb_cntlr_DOUT(15),
      BRAM_Din_A(17) => microblaze_0_ilmb_cntlr_DOUT(14),
      BRAM_Din_A(18) => microblaze_0_ilmb_cntlr_DOUT(13),
      BRAM_Din_A(19) => microblaze_0_ilmb_cntlr_DOUT(12),
      BRAM_Din_A(20) => microblaze_0_ilmb_cntlr_DOUT(11),
      BRAM_Din_A(21) => microblaze_0_ilmb_cntlr_DOUT(10),
      BRAM_Din_A(22) => microblaze_0_ilmb_cntlr_DOUT(9),
      BRAM_Din_A(23) => microblaze_0_ilmb_cntlr_DOUT(8),
      BRAM_Din_A(24) => microblaze_0_ilmb_cntlr_DOUT(7),
      BRAM_Din_A(25) => microblaze_0_ilmb_cntlr_DOUT(6),
      BRAM_Din_A(26) => microblaze_0_ilmb_cntlr_DOUT(5),
      BRAM_Din_A(27) => microblaze_0_ilmb_cntlr_DOUT(4),
      BRAM_Din_A(28) => microblaze_0_ilmb_cntlr_DOUT(3),
      BRAM_Din_A(29) => microblaze_0_ilmb_cntlr_DOUT(2),
      BRAM_Din_A(30) => microblaze_0_ilmb_cntlr_DOUT(1),
      BRAM_Din_A(31) => microblaze_0_ilmb_cntlr_DOUT(0),
      BRAM_Dout_A(0 to 31) => microblaze_0_ilmb_cntlr_DIN(0 to 31),
      BRAM_EN_A => microblaze_0_ilmb_cntlr_EN,
      BRAM_Rst_A => microblaze_0_ilmb_cntlr_RST,
      BRAM_WEN_A(0 to 3) => microblaze_0_ilmb_cntlr_WE(0 to 3),
      LMB_ABus(0 to 31) => microblaze_0_ilmb_bus_ABUS(0 to 31),
      LMB_AddrStrobe => microblaze_0_ilmb_bus_ADDRSTROBE,
      LMB_BE(0 to 3) => microblaze_0_ilmb_bus_BE(0 to 3),
      LMB_Clk => microblaze_0_Clk,
      LMB_ReadStrobe => microblaze_0_ilmb_bus_READSTROBE,
      LMB_Rst => SYS_Rst_1(0),
      LMB_WriteDBus(0 to 31) => microblaze_0_ilmb_bus_WRITEDBUS(0 to 31),
      LMB_WriteStrobe => microblaze_0_ilmb_bus_WRITESTROBE,
      Sl_CE => microblaze_0_ilmb_bus_CE,
      Sl_DBus(0 to 31) => microblaze_0_ilmb_bus_READDBUS(0 to 31),
      Sl_Ready => microblaze_0_ilmb_bus_READY,
      Sl_UE => microblaze_0_ilmb_bus_UE,
      Sl_Wait => microblaze_0_ilmb_bus_WAIT
    );
ilmb_v10: component design_1_ilmb_v10_0
     port map (
      LMB_ABus(0 to 31) => microblaze_0_ilmb_bus_ABUS(0 to 31),
      LMB_AddrStrobe => microblaze_0_ilmb_bus_ADDRSTROBE,
      LMB_BE(0 to 3) => microblaze_0_ilmb_bus_BE(0 to 3),
      LMB_CE => microblaze_0_ilmb_CE,
      LMB_Clk => microblaze_0_Clk,
      LMB_ReadDBus(0 to 31) => microblaze_0_ilmb_READDBUS(0 to 31),
      LMB_ReadStrobe => microblaze_0_ilmb_bus_READSTROBE,
      LMB_Ready => microblaze_0_ilmb_READY,
      LMB_Rst => NLW_ilmb_v10_LMB_Rst_UNCONNECTED,
      LMB_UE => microblaze_0_ilmb_UE,
      LMB_Wait => microblaze_0_ilmb_WAIT,
      LMB_WriteDBus(0 to 31) => microblaze_0_ilmb_bus_WRITEDBUS(0 to 31),
      LMB_WriteStrobe => microblaze_0_ilmb_bus_WRITESTROBE,
      M_ABus(0 to 31) => microblaze_0_ilmb_ABUS(0 to 31),
      M_AddrStrobe => microblaze_0_ilmb_ADDRSTROBE,
      M_BE(0) => GND_1,
      M_BE(1) => GND_1,
      M_BE(2) => GND_1,
      M_BE(3) => GND_1,
      M_DBus(0) => GND_1,
      M_DBus(1) => GND_1,
      M_DBus(2) => GND_1,
      M_DBus(3) => GND_1,
      M_DBus(4) => GND_1,
      M_DBus(5) => GND_1,
      M_DBus(6) => GND_1,
      M_DBus(7) => GND_1,
      M_DBus(8) => GND_1,
      M_DBus(9) => GND_1,
      M_DBus(10) => GND_1,
      M_DBus(11) => GND_1,
      M_DBus(12) => GND_1,
      M_DBus(13) => GND_1,
      M_DBus(14) => GND_1,
      M_DBus(15) => GND_1,
      M_DBus(16) => GND_1,
      M_DBus(17) => GND_1,
      M_DBus(18) => GND_1,
      M_DBus(19) => GND_1,
      M_DBus(20) => GND_1,
      M_DBus(21) => GND_1,
      M_DBus(22) => GND_1,
      M_DBus(23) => GND_1,
      M_DBus(24) => GND_1,
      M_DBus(25) => GND_1,
      M_DBus(26) => GND_1,
      M_DBus(27) => GND_1,
      M_DBus(28) => GND_1,
      M_DBus(29) => GND_1,
      M_DBus(30) => GND_1,
      M_DBus(31) => GND_1,
      M_ReadStrobe => microblaze_0_ilmb_READSTROBE,
      M_WriteStrobe => GND_1,
      SYS_Rst => SYS_Rst_1(0),
      Sl_CE(0) => microblaze_0_ilmb_bus_CE,
      Sl_DBus(0 to 31) => microblaze_0_ilmb_bus_READDBUS(0 to 31),
      Sl_Ready(0) => microblaze_0_ilmb_bus_READY,
      Sl_UE(0) => microblaze_0_ilmb_bus_UE,
      Sl_Wait(0) => microblaze_0_ilmb_bus_WAIT
    );
lmb_bram: component design_1_lmb_bram_0
     port map (
      addra(31) => microblaze_0_dlmb_cntlr_ADDR(0),
      addra(30) => microblaze_0_dlmb_cntlr_ADDR(1),
      addra(29) => microblaze_0_dlmb_cntlr_ADDR(2),
      addra(28) => microblaze_0_dlmb_cntlr_ADDR(3),
      addra(27) => microblaze_0_dlmb_cntlr_ADDR(4),
      addra(26) => microblaze_0_dlmb_cntlr_ADDR(5),
      addra(25) => microblaze_0_dlmb_cntlr_ADDR(6),
      addra(24) => microblaze_0_dlmb_cntlr_ADDR(7),
      addra(23) => microblaze_0_dlmb_cntlr_ADDR(8),
      addra(22) => microblaze_0_dlmb_cntlr_ADDR(9),
      addra(21) => microblaze_0_dlmb_cntlr_ADDR(10),
      addra(20) => microblaze_0_dlmb_cntlr_ADDR(11),
      addra(19) => microblaze_0_dlmb_cntlr_ADDR(12),
      addra(18) => microblaze_0_dlmb_cntlr_ADDR(13),
      addra(17) => microblaze_0_dlmb_cntlr_ADDR(14),
      addra(16) => microblaze_0_dlmb_cntlr_ADDR(15),
      addra(15) => microblaze_0_dlmb_cntlr_ADDR(16),
      addra(14) => microblaze_0_dlmb_cntlr_ADDR(17),
      addra(13) => microblaze_0_dlmb_cntlr_ADDR(18),
      addra(12) => microblaze_0_dlmb_cntlr_ADDR(19),
      addra(11) => microblaze_0_dlmb_cntlr_ADDR(20),
      addra(10) => microblaze_0_dlmb_cntlr_ADDR(21),
      addra(9) => microblaze_0_dlmb_cntlr_ADDR(22),
      addra(8) => microblaze_0_dlmb_cntlr_ADDR(23),
      addra(7) => microblaze_0_dlmb_cntlr_ADDR(24),
      addra(6) => microblaze_0_dlmb_cntlr_ADDR(25),
      addra(5) => microblaze_0_dlmb_cntlr_ADDR(26),
      addra(4) => microblaze_0_dlmb_cntlr_ADDR(27),
      addra(3) => microblaze_0_dlmb_cntlr_ADDR(28),
      addra(2) => microblaze_0_dlmb_cntlr_ADDR(29),
      addra(1) => microblaze_0_dlmb_cntlr_ADDR(30),
      addra(0) => microblaze_0_dlmb_cntlr_ADDR(31),
      addrb(31) => microblaze_0_ilmb_cntlr_ADDR(0),
      addrb(30) => microblaze_0_ilmb_cntlr_ADDR(1),
      addrb(29) => microblaze_0_ilmb_cntlr_ADDR(2),
      addrb(28) => microblaze_0_ilmb_cntlr_ADDR(3),
      addrb(27) => microblaze_0_ilmb_cntlr_ADDR(4),
      addrb(26) => microblaze_0_ilmb_cntlr_ADDR(5),
      addrb(25) => microblaze_0_ilmb_cntlr_ADDR(6),
      addrb(24) => microblaze_0_ilmb_cntlr_ADDR(7),
      addrb(23) => microblaze_0_ilmb_cntlr_ADDR(8),
      addrb(22) => microblaze_0_ilmb_cntlr_ADDR(9),
      addrb(21) => microblaze_0_ilmb_cntlr_ADDR(10),
      addrb(20) => microblaze_0_ilmb_cntlr_ADDR(11),
      addrb(19) => microblaze_0_ilmb_cntlr_ADDR(12),
      addrb(18) => microblaze_0_ilmb_cntlr_ADDR(13),
      addrb(17) => microblaze_0_ilmb_cntlr_ADDR(14),
      addrb(16) => microblaze_0_ilmb_cntlr_ADDR(15),
      addrb(15) => microblaze_0_ilmb_cntlr_ADDR(16),
      addrb(14) => microblaze_0_ilmb_cntlr_ADDR(17),
      addrb(13) => microblaze_0_ilmb_cntlr_ADDR(18),
      addrb(12) => microblaze_0_ilmb_cntlr_ADDR(19),
      addrb(11) => microblaze_0_ilmb_cntlr_ADDR(20),
      addrb(10) => microblaze_0_ilmb_cntlr_ADDR(21),
      addrb(9) => microblaze_0_ilmb_cntlr_ADDR(22),
      addrb(8) => microblaze_0_ilmb_cntlr_ADDR(23),
      addrb(7) => microblaze_0_ilmb_cntlr_ADDR(24),
      addrb(6) => microblaze_0_ilmb_cntlr_ADDR(25),
      addrb(5) => microblaze_0_ilmb_cntlr_ADDR(26),
      addrb(4) => microblaze_0_ilmb_cntlr_ADDR(27),
      addrb(3) => microblaze_0_ilmb_cntlr_ADDR(28),
      addrb(2) => microblaze_0_ilmb_cntlr_ADDR(29),
      addrb(1) => microblaze_0_ilmb_cntlr_ADDR(30),
      addrb(0) => microblaze_0_ilmb_cntlr_ADDR(31),
      clka => microblaze_0_dlmb_cntlr_CLK,
      clkb => microblaze_0_ilmb_cntlr_CLK,
      dina(31) => microblaze_0_dlmb_cntlr_DIN(0),
      dina(30) => microblaze_0_dlmb_cntlr_DIN(1),
      dina(29) => microblaze_0_dlmb_cntlr_DIN(2),
      dina(28) => microblaze_0_dlmb_cntlr_DIN(3),
      dina(27) => microblaze_0_dlmb_cntlr_DIN(4),
      dina(26) => microblaze_0_dlmb_cntlr_DIN(5),
      dina(25) => microblaze_0_dlmb_cntlr_DIN(6),
      dina(24) => microblaze_0_dlmb_cntlr_DIN(7),
      dina(23) => microblaze_0_dlmb_cntlr_DIN(8),
      dina(22) => microblaze_0_dlmb_cntlr_DIN(9),
      dina(21) => microblaze_0_dlmb_cntlr_DIN(10),
      dina(20) => microblaze_0_dlmb_cntlr_DIN(11),
      dina(19) => microblaze_0_dlmb_cntlr_DIN(12),
      dina(18) => microblaze_0_dlmb_cntlr_DIN(13),
      dina(17) => microblaze_0_dlmb_cntlr_DIN(14),
      dina(16) => microblaze_0_dlmb_cntlr_DIN(15),
      dina(15) => microblaze_0_dlmb_cntlr_DIN(16),
      dina(14) => microblaze_0_dlmb_cntlr_DIN(17),
      dina(13) => microblaze_0_dlmb_cntlr_DIN(18),
      dina(12) => microblaze_0_dlmb_cntlr_DIN(19),
      dina(11) => microblaze_0_dlmb_cntlr_DIN(20),
      dina(10) => microblaze_0_dlmb_cntlr_DIN(21),
      dina(9) => microblaze_0_dlmb_cntlr_DIN(22),
      dina(8) => microblaze_0_dlmb_cntlr_DIN(23),
      dina(7) => microblaze_0_dlmb_cntlr_DIN(24),
      dina(6) => microblaze_0_dlmb_cntlr_DIN(25),
      dina(5) => microblaze_0_dlmb_cntlr_DIN(26),
      dina(4) => microblaze_0_dlmb_cntlr_DIN(27),
      dina(3) => microblaze_0_dlmb_cntlr_DIN(28),
      dina(2) => microblaze_0_dlmb_cntlr_DIN(29),
      dina(1) => microblaze_0_dlmb_cntlr_DIN(30),
      dina(0) => microblaze_0_dlmb_cntlr_DIN(31),
      dinb(31) => microblaze_0_ilmb_cntlr_DIN(0),
      dinb(30) => microblaze_0_ilmb_cntlr_DIN(1),
      dinb(29) => microblaze_0_ilmb_cntlr_DIN(2),
      dinb(28) => microblaze_0_ilmb_cntlr_DIN(3),
      dinb(27) => microblaze_0_ilmb_cntlr_DIN(4),
      dinb(26) => microblaze_0_ilmb_cntlr_DIN(5),
      dinb(25) => microblaze_0_ilmb_cntlr_DIN(6),
      dinb(24) => microblaze_0_ilmb_cntlr_DIN(7),
      dinb(23) => microblaze_0_ilmb_cntlr_DIN(8),
      dinb(22) => microblaze_0_ilmb_cntlr_DIN(9),
      dinb(21) => microblaze_0_ilmb_cntlr_DIN(10),
      dinb(20) => microblaze_0_ilmb_cntlr_DIN(11),
      dinb(19) => microblaze_0_ilmb_cntlr_DIN(12),
      dinb(18) => microblaze_0_ilmb_cntlr_DIN(13),
      dinb(17) => microblaze_0_ilmb_cntlr_DIN(14),
      dinb(16) => microblaze_0_ilmb_cntlr_DIN(15),
      dinb(15) => microblaze_0_ilmb_cntlr_DIN(16),
      dinb(14) => microblaze_0_ilmb_cntlr_DIN(17),
      dinb(13) => microblaze_0_ilmb_cntlr_DIN(18),
      dinb(12) => microblaze_0_ilmb_cntlr_DIN(19),
      dinb(11) => microblaze_0_ilmb_cntlr_DIN(20),
      dinb(10) => microblaze_0_ilmb_cntlr_DIN(21),
      dinb(9) => microblaze_0_ilmb_cntlr_DIN(22),
      dinb(8) => microblaze_0_ilmb_cntlr_DIN(23),
      dinb(7) => microblaze_0_ilmb_cntlr_DIN(24),
      dinb(6) => microblaze_0_ilmb_cntlr_DIN(25),
      dinb(5) => microblaze_0_ilmb_cntlr_DIN(26),
      dinb(4) => microblaze_0_ilmb_cntlr_DIN(27),
      dinb(3) => microblaze_0_ilmb_cntlr_DIN(28),
      dinb(2) => microblaze_0_ilmb_cntlr_DIN(29),
      dinb(1) => microblaze_0_ilmb_cntlr_DIN(30),
      dinb(0) => microblaze_0_ilmb_cntlr_DIN(31),
      douta(31 downto 0) => microblaze_0_dlmb_cntlr_DOUT(31 downto 0),
      doutb(31 downto 0) => microblaze_0_ilmb_cntlr_DOUT(31 downto 0),
      ena => microblaze_0_dlmb_cntlr_EN,
      enb => microblaze_0_ilmb_cntlr_EN,
      rsta => microblaze_0_dlmb_cntlr_RST,
      rstb => microblaze_0_ilmb_cntlr_RST,
      wea(3) => microblaze_0_dlmb_cntlr_WE(0),
      wea(2) => microblaze_0_dlmb_cntlr_WE(1),
      wea(1) => microblaze_0_dlmb_cntlr_WE(2),
      wea(0) => microblaze_0_dlmb_cntlr_WE(3),
      web(3) => microblaze_0_ilmb_cntlr_WE(0),
      web(2) => microblaze_0_ilmb_cntlr_WE(1),
      web(1) => microblaze_0_ilmb_cntlr_WE(2),
      web(0) => microblaze_0_ilmb_cntlr_WE(3)
    );
end STRUCTURE;
library IEEE;
use IEEE.STD_LOGIC_1164.ALL;
library UNISIM;
use UNISIM.VCOMPONENTS.ALL;
entity s00_couplers_imp_1RZP34U is
  port (
    M_ACLK : in STD_LOGIC;
    M_ARESETN : in STD_LOGIC_VECTOR ( 0 to 0 );
    M_AXI_araddr : out STD_LOGIC_VECTOR ( 31 downto 0 );
    M_AXI_arprot : out STD_LOGIC_VECTOR ( 2 downto 0 );
    M_AXI_arready : in STD_LOGIC_VECTOR ( 0 to 0 );
    M_AXI_arvalid : out STD_LOGIC_VECTOR ( 0 to 0 );
    M_AXI_awaddr : out STD_LOGIC_VECTOR ( 31 downto 0 );
    M_AXI_awprot : out STD_LOGIC_VECTOR ( 2 downto 0 );
    M_AXI_awready : in STD_LOGIC_VECTOR ( 0 to 0 );
    M_AXI_awvalid : out STD_LOGIC_VECTOR ( 0 to 0 );
    M_AXI_bready : out STD_LOGIC_VECTOR ( 0 to 0 );
    M_AXI_bresp : in STD_LOGIC_VECTOR ( 1 downto 0 );
    M_AXI_bvalid : in STD_LOGIC_VECTOR ( 0 to 0 );
    M_AXI_rdata : in STD_LOGIC_VECTOR ( 31 downto 0 );
    M_AXI_rready : out STD_LOGIC_VECTOR ( 0 to 0 );
    M_AXI_rresp : in STD_LOGIC_VECTOR ( 1 downto 0 );
    M_AXI_rvalid : in STD_LOGIC_VECTOR ( 0 to 0 );
    M_AXI_wdata : out STD_LOGIC_VECTOR ( 31 downto 0 );
    M_AXI_wready : in STD_LOGIC_VECTOR ( 0 to 0 );
    M_AXI_wstrb : out STD_LOGIC_VECTOR ( 3 downto 0 );
    M_AXI_wvalid : out STD_LOGIC_VECTOR ( 0 to 0 );
    S_ACLK : in STD_LOGIC;
    S_ARESETN : in STD_LOGIC_VECTOR ( 0 to 0 );
    S_AXI_araddr : in STD_LOGIC_VECTOR ( 31 downto 0 );
    S_AXI_arprot : in STD_LOGIC_VECTOR ( 2 downto 0 );
    S_AXI_arready : out STD_LOGIC_VECTOR ( 0 to 0 );
    S_AXI_arvalid : in STD_LOGIC_VECTOR ( 0 to 0 );
    S_AXI_awaddr : in STD_LOGIC_VECTOR ( 31 downto 0 );
    S_AXI_awprot : in STD_LOGIC_VECTOR ( 2 downto 0 );
    S_AXI_awready : out STD_LOGIC_VECTOR ( 0 to 0 );
    S_AXI_awvalid : in STD_LOGIC_VECTOR ( 0 to 0 );
    S_AXI_bready : in STD_LOGIC_VECTOR ( 0 to 0 );
    S_AXI_bresp : out STD_LOGIC_VECTOR ( 1 downto 0 );
    S_AXI_bvalid : out STD_LOGIC_VECTOR ( 0 to 0 );
    S_AXI_rdata : out STD_LOGIC_VECTOR ( 31 downto 0 );
    S_AXI_rready : in STD_LOGIC_VECTOR ( 0 to 0 );
    S_AXI_rresp : out STD_LOGIC_VECTOR ( 1 downto 0 );
    S_AXI_rvalid : out STD_LOGIC_VECTOR ( 0 to 0 );
    S_AXI_wdata : in STD_LOGIC_VECTOR ( 31 downto 0 );
    S_AXI_wready : out STD_LOGIC_VECTOR ( 0 to 0 );
    S_AXI_wstrb : in STD_LOGIC_VECTOR ( 3 downto 0 );
    S_AXI_wvalid : in STD_LOGIC_VECTOR ( 0 to 0 )
  );
end s00_couplers_imp_1RZP34U;

architecture STRUCTURE of s00_couplers_imp_1RZP34U is
  signal s00_couplers_to_s00_couplers_ARADDR : STD_LOGIC_VECTOR ( 31 downto 0 );
  signal s00_couplers_to_s00_couplers_ARPROT : STD_LOGIC_VECTOR ( 2 downto 0 );
  signal s00_couplers_to_s00_couplers_ARREADY : STD_LOGIC_VECTOR ( 0 to 0 );
  signal s00_couplers_to_s00_couplers_ARVALID : STD_LOGIC_VECTOR ( 0 to 0 );
  signal s00_couplers_to_s00_couplers_AWADDR : STD_LOGIC_VECTOR ( 31 downto 0 );
  signal s00_couplers_to_s00_couplers_AWPROT : STD_LOGIC_VECTOR ( 2 downto 0 );
  signal s00_couplers_to_s00_couplers_AWREADY : STD_LOGIC_VECTOR ( 0 to 0 );
  signal s00_couplers_to_s00_couplers_AWVALID : STD_LOGIC_VECTOR ( 0 to 0 );
  signal s00_couplers_to_s00_couplers_BREADY : STD_LOGIC_VECTOR ( 0 to 0 );
  signal s00_couplers_to_s00_couplers_BRESP : STD_LOGIC_VECTOR ( 1 downto 0 );
  signal s00_couplers_to_s00_couplers_BVALID : STD_LOGIC_VECTOR ( 0 to 0 );
  signal s00_couplers_to_s00_couplers_RDATA : STD_LOGIC_VECTOR ( 31 downto 0 );
  signal s00_couplers_to_s00_couplers_RREADY : STD_LOGIC_VECTOR ( 0 to 0 );
  signal s00_couplers_to_s00_couplers_RRESP : STD_LOGIC_VECTOR ( 1 downto 0 );
  signal s00_couplers_to_s00_couplers_RVALID : STD_LOGIC_VECTOR ( 0 to 0 );
  signal s00_couplers_to_s00_couplers_WDATA : STD_LOGIC_VECTOR ( 31 downto 0 );
  signal s00_couplers_to_s00_couplers_WREADY : STD_LOGIC_VECTOR ( 0 to 0 );
  signal s00_couplers_to_s00_couplers_WSTRB : STD_LOGIC_VECTOR ( 3 downto 0 );
  signal s00_couplers_to_s00_couplers_WVALID : STD_LOGIC_VECTOR ( 0 to 0 );
begin
  M_AXI_araddr(31 downto 0) <= s00_couplers_to_s00_couplers_ARADDR(31 downto 0);
  M_AXI_arprot(2 downto 0) <= s00_couplers_to_s00_couplers_ARPROT(2 downto 0);
  M_AXI_arvalid(0) <= s00_couplers_to_s00_couplers_ARVALID(0);
  M_AXI_awaddr(31 downto 0) <= s00_couplers_to_s00_couplers_AWADDR(31 downto 0);
  M_AXI_awprot(2 downto 0) <= s00_couplers_to_s00_couplers_AWPROT(2 downto 0);
  M_AXI_awvalid(0) <= s00_couplers_to_s00_couplers_AWVALID(0);
  M_AXI_bready(0) <= s00_couplers_to_s00_couplers_BREADY(0);
  M_AXI_rready(0) <= s00_couplers_to_s00_couplers_RREADY(0);
  M_AXI_wdata(31 downto 0) <= s00_couplers_to_s00_couplers_WDATA(31 downto 0);
  M_AXI_wstrb(3 downto 0) <= s00_couplers_to_s00_couplers_WSTRB(3 downto 0);
  M_AXI_wvalid(0) <= s00_couplers_to_s00_couplers_WVALID(0);
  S_AXI_arready(0) <= s00_couplers_to_s00_couplers_ARREADY(0);
  S_AXI_awready(0) <= s00_couplers_to_s00_couplers_AWREADY(0);
  S_AXI_bresp(1 downto 0) <= s00_couplers_to_s00_couplers_BRESP(1 downto 0);
  S_AXI_bvalid(0) <= s00_couplers_to_s00_couplers_BVALID(0);
  S_AXI_rdata(31 downto 0) <= s00_couplers_to_s00_couplers_RDATA(31 downto 0);
  S_AXI_rresp(1 downto 0) <= s00_couplers_to_s00_couplers_RRESP(1 downto 0);
  S_AXI_rvalid(0) <= s00_couplers_to_s00_couplers_RVALID(0);
  S_AXI_wready(0) <= s00_couplers_to_s00_couplers_WREADY(0);
  s00_couplers_to_s00_couplers_ARADDR(31 downto 0) <= S_AXI_araddr(31 downto 0);
  s00_couplers_to_s00_couplers_ARPROT(2 downto 0) <= S_AXI_arprot(2 downto 0);
  s00_couplers_to_s00_couplers_ARREADY(0) <= M_AXI_arready(0);
  s00_couplers_to_s00_couplers_ARVALID(0) <= S_AXI_arvalid(0);
  s00_couplers_to_s00_couplers_AWADDR(31 downto 0) <= S_AXI_awaddr(31 downto 0);
  s00_couplers_to_s00_couplers_AWPROT(2 downto 0) <= S_AXI_awprot(2 downto 0);
  s00_couplers_to_s00_couplers_AWREADY(0) <= M_AXI_awready(0);
  s00_couplers_to_s00_couplers_AWVALID(0) <= S_AXI_awvalid(0);
  s00_couplers_to_s00_couplers_BREADY(0) <= S_AXI_bready(0);
  s00_couplers_to_s00_couplers_BRESP(1 downto 0) <= M_AXI_bresp(1 downto 0);
  s00_couplers_to_s00_couplers_BVALID(0) <= M_AXI_bvalid(0);
  s00_couplers_to_s00_couplers_RDATA(31 downto 0) <= M_AXI_rdata(31 downto 0);
  s00_couplers_to_s00_couplers_RREADY(0) <= S_AXI_rready(0);
  s00_couplers_to_s00_couplers_RRESP(1 downto 0) <= M_AXI_rresp(1 downto 0);
  s00_couplers_to_s00_couplers_RVALID(0) <= M_AXI_rvalid(0);
  s00_couplers_to_s00_couplers_WDATA(31 downto 0) <= S_AXI_wdata(31 downto 0);
  s00_couplers_to_s00_couplers_WREADY(0) <= M_AXI_wready(0);
  s00_couplers_to_s00_couplers_WSTRB(3 downto 0) <= S_AXI_wstrb(3 downto 0);
  s00_couplers_to_s00_couplers_WVALID(0) <= S_AXI_wvalid(0);
end STRUCTURE;
library IEEE;
use IEEE.STD_LOGIC_1164.ALL;
library UNISIM;
use UNISIM.VCOMPONENTS.ALL;
entity s00_couplers_imp_7HNO1D is
  port (
    M_ACLK : in STD_LOGIC;
    M_ARESETN : in STD_LOGIC_VECTOR ( 0 to 0 );
    M_AXI_araddr : out STD_LOGIC_VECTOR ( 31 downto 0 );
    M_AXI_arburst : out STD_LOGIC_VECTOR ( 1 downto 0 );
    M_AXI_arcache : out STD_LOGIC_VECTOR ( 3 downto 0 );
    M_AXI_arid : out STD_LOGIC_VECTOR ( 0 to 0 );
    M_AXI_arlen : out STD_LOGIC_VECTOR ( 7 downto 0 );
    M_AXI_arlock : out STD_LOGIC_VECTOR ( 0 to 0 );
    M_AXI_arprot : out STD_LOGIC_VECTOR ( 2 downto 0 );
    M_AXI_arqos : out STD_LOGIC_VECTOR ( 3 downto 0 );
    M_AXI_arready : in STD_LOGIC_VECTOR ( 0 to 0 );
    M_AXI_arsize : out STD_LOGIC_VECTOR ( 2 downto 0 );
    M_AXI_arvalid : out STD_LOGIC_VECTOR ( 0 to 0 );
    M_AXI_awaddr : out STD_LOGIC_VECTOR ( 31 downto 0 );
    M_AXI_awburst : out STD_LOGIC_VECTOR ( 1 downto 0 );
    M_AXI_awcache : out STD_LOGIC_VECTOR ( 3 downto 0 );
    M_AXI_awid : out STD_LOGIC_VECTOR ( 0 to 0 );
    M_AXI_awlen : out STD_LOGIC_VECTOR ( 7 downto 0 );
    M_AXI_awlock : out STD_LOGIC_VECTOR ( 0 to 0 );
    M_AXI_awprot : out STD_LOGIC_VECTOR ( 2 downto 0 );
    M_AXI_awqos : out STD_LOGIC_VECTOR ( 3 downto 0 );
    M_AXI_awready : in STD_LOGIC_VECTOR ( 0 to 0 );
    M_AXI_awsize : out STD_LOGIC_VECTOR ( 2 downto 0 );
    M_AXI_awvalid : out STD_LOGIC_VECTOR ( 0 to 0 );
    M_AXI_bid : in STD_LOGIC_VECTOR ( 0 to 0 );
    M_AXI_bready : out STD_LOGIC_VECTOR ( 0 to 0 );
    M_AXI_bresp : in STD_LOGIC_VECTOR ( 1 downto 0 );
    M_AXI_bvalid : in STD_LOGIC_VECTOR ( 0 to 0 );
    M_AXI_rdata : in STD_LOGIC_VECTOR ( 31 downto 0 );
    M_AXI_rid : in STD_LOGIC_VECTOR ( 0 to 0 );
    M_AXI_rlast : in STD_LOGIC_VECTOR ( 0 to 0 );
    M_AXI_rready : out STD_LOGIC_VECTOR ( 0 to 0 );
    M_AXI_rresp : in STD_LOGIC_VECTOR ( 1 downto 0 );
    M_AXI_rvalid : in STD_LOGIC_VECTOR ( 0 to 0 );
    M_AXI_wdata : out STD_LOGIC_VECTOR ( 31 downto 0 );
    M_AXI_wlast : out STD_LOGIC_VECTOR ( 0 to 0 );
    M_AXI_wready : in STD_LOGIC_VECTOR ( 0 to 0 );
    M_AXI_wstrb : out STD_LOGIC_VECTOR ( 3 downto 0 );
    M_AXI_wvalid : out STD_LOGIC_VECTOR ( 0 to 0 );
    S_ACLK : in STD_LOGIC;
    S_ARESETN : in STD_LOGIC_VECTOR ( 0 to 0 );
    S_AXI_araddr : in STD_LOGIC_VECTOR ( 31 downto 0 );
    S_AXI_arburst : in STD_LOGIC_VECTOR ( 1 downto 0 );
    S_AXI_arcache : in STD_LOGIC_VECTOR ( 3 downto 0 );
    S_AXI_arid : in STD_LOGIC_VECTOR ( 0 to 0 );
    S_AXI_arlen : in STD_LOGIC_VECTOR ( 7 downto 0 );
    S_AXI_arlock : in STD_LOGIC_VECTOR ( 0 to 0 );
    S_AXI_arprot : in STD_LOGIC_VECTOR ( 2 downto 0 );
    S_AXI_arqos : in STD_LOGIC_VECTOR ( 3 downto 0 );
    S_AXI_arready : out STD_LOGIC_VECTOR ( 0 to 0 );
    S_AXI_arsize : in STD_LOGIC_VECTOR ( 2 downto 0 );
    S_AXI_arvalid : in STD_LOGIC_VECTOR ( 0 to 0 );
    S_AXI_awaddr : in STD_LOGIC_VECTOR ( 31 downto 0 );
    S_AXI_awburst : in STD_LOGIC_VECTOR ( 1 downto 0 );
    S_AXI_awcache : in STD_LOGIC_VECTOR ( 3 downto 0 );
    S_AXI_awid : in STD_LOGIC_VECTOR ( 0 to 0 );
    S_AXI_awlen : in STD_LOGIC_VECTOR ( 7 downto 0 );
    S_AXI_awlock : in STD_LOGIC_VECTOR ( 0 to 0 );
    S_AXI_awprot : in STD_LOGIC_VECTOR ( 2 downto 0 );
    S_AXI_awqos : in STD_LOGIC_VECTOR ( 3 downto 0 );
    S_AXI_awready : out STD_LOGIC_VECTOR ( 0 to 0 );
    S_AXI_awsize : in STD_LOGIC_VECTOR ( 2 downto 0 );
    S_AXI_awvalid : in STD_LOGIC_VECTOR ( 0 to 0 );
    S_AXI_bid : out STD_LOGIC_VECTOR ( 0 to 0 );
    S_AXI_bready : in STD_LOGIC_VECTOR ( 0 to 0 );
    S_AXI_bresp : out STD_LOGIC_VECTOR ( 1 downto 0 );
    S_AXI_bvalid : out STD_LOGIC_VECTOR ( 0 to 0 );
    S_AXI_rdata : out STD_LOGIC_VECTOR ( 31 downto 0 );
    S_AXI_rid : out STD_LOGIC_VECTOR ( 0 to 0 );
    S_AXI_rlast : out STD_LOGIC_VECTOR ( 0 to 0 );
    S_AXI_rready : in STD_LOGIC_VECTOR ( 0 to 0 );
    S_AXI_rresp : out STD_LOGIC_VECTOR ( 1 downto 0 );
    S_AXI_rvalid : out STD_LOGIC_VECTOR ( 0 to 0 );
    S_AXI_wdata : in STD_LOGIC_VECTOR ( 31 downto 0 );
    S_AXI_wlast : in STD_LOGIC_VECTOR ( 0 to 0 );
    S_AXI_wready : out STD_LOGIC_VECTOR ( 0 to 0 );
    S_AXI_wstrb : in STD_LOGIC_VECTOR ( 3 downto 0 );
    S_AXI_wvalid : in STD_LOGIC_VECTOR ( 0 to 0 )
  );
end s00_couplers_imp_7HNO1D;

architecture STRUCTURE of s00_couplers_imp_7HNO1D is
  signal s00_couplers_to_s00_couplers_ARADDR : STD_LOGIC_VECTOR ( 31 downto 0 );
  signal s00_couplers_to_s00_couplers_ARBURST : STD_LOGIC_VECTOR ( 1 downto 0 );
  signal s00_couplers_to_s00_couplers_ARCACHE : STD_LOGIC_VECTOR ( 3 downto 0 );
  signal s00_couplers_to_s00_couplers_ARID : STD_LOGIC_VECTOR ( 0 to 0 );
  signal s00_couplers_to_s00_couplers_ARLEN : STD_LOGIC_VECTOR ( 7 downto 0 );
  signal s00_couplers_to_s00_couplers_ARLOCK : STD_LOGIC_VECTOR ( 0 to 0 );
  signal s00_couplers_to_s00_couplers_ARPROT : STD_LOGIC_VECTOR ( 2 downto 0 );
  signal s00_couplers_to_s00_couplers_ARQOS : STD_LOGIC_VECTOR ( 3 downto 0 );
  signal s00_couplers_to_s00_couplers_ARREADY : STD_LOGIC_VECTOR ( 0 to 0 );
  signal s00_couplers_to_s00_couplers_ARSIZE : STD_LOGIC_VECTOR ( 2 downto 0 );
  signal s00_couplers_to_s00_couplers_ARVALID : STD_LOGIC_VECTOR ( 0 to 0 );
  signal s00_couplers_to_s00_couplers_AWADDR : STD_LOGIC_VECTOR ( 31 downto 0 );
  signal s00_couplers_to_s00_couplers_AWBURST : STD_LOGIC_VECTOR ( 1 downto 0 );
  signal s00_couplers_to_s00_couplers_AWCACHE : STD_LOGIC_VECTOR ( 3 downto 0 );
  signal s00_couplers_to_s00_couplers_AWID : STD_LOGIC_VECTOR ( 0 to 0 );
  signal s00_couplers_to_s00_couplers_AWLEN : STD_LOGIC_VECTOR ( 7 downto 0 );
  signal s00_couplers_to_s00_couplers_AWLOCK : STD_LOGIC_VECTOR ( 0 to 0 );
  signal s00_couplers_to_s00_couplers_AWPROT : STD_LOGIC_VECTOR ( 2 downto 0 );
  signal s00_couplers_to_s00_couplers_AWQOS : STD_LOGIC_VECTOR ( 3 downto 0 );
  signal s00_couplers_to_s00_couplers_AWREADY : STD_LOGIC_VECTOR ( 0 to 0 );
  signal s00_couplers_to_s00_couplers_AWSIZE : STD_LOGIC_VECTOR ( 2 downto 0 );
  signal s00_couplers_to_s00_couplers_AWVALID : STD_LOGIC_VECTOR ( 0 to 0 );
  signal s00_couplers_to_s00_couplers_BID : STD_LOGIC_VECTOR ( 0 to 0 );
  signal s00_couplers_to_s00_couplers_BREADY : STD_LOGIC_VECTOR ( 0 to 0 );
  signal s00_couplers_to_s00_couplers_BRESP : STD_LOGIC_VECTOR ( 1 downto 0 );
  signal s00_couplers_to_s00_couplers_BVALID : STD_LOGIC_VECTOR ( 0 to 0 );
  signal s00_couplers_to_s00_couplers_RDATA : STD_LOGIC_VECTOR ( 31 downto 0 );
  signal s00_couplers_to_s00_couplers_RID : STD_LOGIC_VECTOR ( 0 to 0 );
  signal s00_couplers_to_s00_couplers_RLAST : STD_LOGIC_VECTOR ( 0 to 0 );
  signal s00_couplers_to_s00_couplers_RREADY : STD_LOGIC_VECTOR ( 0 to 0 );
  signal s00_couplers_to_s00_couplers_RRESP : STD_LOGIC_VECTOR ( 1 downto 0 );
  signal s00_couplers_to_s00_couplers_RVALID : STD_LOGIC_VECTOR ( 0 to 0 );
  signal s00_couplers_to_s00_couplers_WDATA : STD_LOGIC_VECTOR ( 31 downto 0 );
  signal s00_couplers_to_s00_couplers_WLAST : STD_LOGIC_VECTOR ( 0 to 0 );
  signal s00_couplers_to_s00_couplers_WREADY : STD_LOGIC_VECTOR ( 0 to 0 );
  signal s00_couplers_to_s00_couplers_WSTRB : STD_LOGIC_VECTOR ( 3 downto 0 );
  signal s00_couplers_to_s00_couplers_WVALID : STD_LOGIC_VECTOR ( 0 to 0 );
begin
  M_AXI_araddr(31 downto 0) <= s00_couplers_to_s00_couplers_ARADDR(31 downto 0);
  M_AXI_arburst(1 downto 0) <= s00_couplers_to_s00_couplers_ARBURST(1 downto 0);
  M_AXI_arcache(3 downto 0) <= s00_couplers_to_s00_couplers_ARCACHE(3 downto 0);
  M_AXI_arid(0) <= s00_couplers_to_s00_couplers_ARID(0);
  M_AXI_arlen(7 downto 0) <= s00_couplers_to_s00_couplers_ARLEN(7 downto 0);
  M_AXI_arlock(0) <= s00_couplers_to_s00_couplers_ARLOCK(0);
  M_AXI_arprot(2 downto 0) <= s00_couplers_to_s00_couplers_ARPROT(2 downto 0);
  M_AXI_arqos(3 downto 0) <= s00_couplers_to_s00_couplers_ARQOS(3 downto 0);
  M_AXI_arsize(2 downto 0) <= s00_couplers_to_s00_couplers_ARSIZE(2 downto 0);
  M_AXI_arvalid(0) <= s00_couplers_to_s00_couplers_ARVALID(0);
  M_AXI_awaddr(31 downto 0) <= s00_couplers_to_s00_couplers_AWADDR(31 downto 0);
  M_AXI_awburst(1 downto 0) <= s00_couplers_to_s00_couplers_AWBURST(1 downto 0);
  M_AXI_awcache(3 downto 0) <= s00_couplers_to_s00_couplers_AWCACHE(3 downto 0);
  M_AXI_awid(0) <= s00_couplers_to_s00_couplers_AWID(0);
  M_AXI_awlen(7 downto 0) <= s00_couplers_to_s00_couplers_AWLEN(7 downto 0);
  M_AXI_awlock(0) <= s00_couplers_to_s00_couplers_AWLOCK(0);
  M_AXI_awprot(2 downto 0) <= s00_couplers_to_s00_couplers_AWPROT(2 downto 0);
  M_AXI_awqos(3 downto 0) <= s00_couplers_to_s00_couplers_AWQOS(3 downto 0);
  M_AXI_awsize(2 downto 0) <= s00_couplers_to_s00_couplers_AWSIZE(2 downto 0);
  M_AXI_awvalid(0) <= s00_couplers_to_s00_couplers_AWVALID(0);
  M_AXI_bready(0) <= s00_couplers_to_s00_couplers_BREADY(0);
  M_AXI_rready(0) <= s00_couplers_to_s00_couplers_RREADY(0);
  M_AXI_wdata(31 downto 0) <= s00_couplers_to_s00_couplers_WDATA(31 downto 0);
  M_AXI_wlast(0) <= s00_couplers_to_s00_couplers_WLAST(0);
  M_AXI_wstrb(3 downto 0) <= s00_couplers_to_s00_couplers_WSTRB(3 downto 0);
  M_AXI_wvalid(0) <= s00_couplers_to_s00_couplers_WVALID(0);
  S_AXI_arready(0) <= s00_couplers_to_s00_couplers_ARREADY(0);
  S_AXI_awready(0) <= s00_couplers_to_s00_couplers_AWREADY(0);
  S_AXI_bid(0) <= s00_couplers_to_s00_couplers_BID(0);
  S_AXI_bresp(1 downto 0) <= s00_couplers_to_s00_couplers_BRESP(1 downto 0);
  S_AXI_bvalid(0) <= s00_couplers_to_s00_couplers_BVALID(0);
  S_AXI_rdata(31 downto 0) <= s00_couplers_to_s00_couplers_RDATA(31 downto 0);
  S_AXI_rid(0) <= s00_couplers_to_s00_couplers_RID(0);
  S_AXI_rlast(0) <= s00_couplers_to_s00_couplers_RLAST(0);
  S_AXI_rresp(1 downto 0) <= s00_couplers_to_s00_couplers_RRESP(1 downto 0);
  S_AXI_rvalid(0) <= s00_couplers_to_s00_couplers_RVALID(0);
  S_AXI_wready(0) <= s00_couplers_to_s00_couplers_WREADY(0);
  s00_couplers_to_s00_couplers_ARADDR(31 downto 0) <= S_AXI_araddr(31 downto 0);
  s00_couplers_to_s00_couplers_ARBURST(1 downto 0) <= S_AXI_arburst(1 downto 0);
  s00_couplers_to_s00_couplers_ARCACHE(3 downto 0) <= S_AXI_arcache(3 downto 0);
  s00_couplers_to_s00_couplers_ARID(0) <= S_AXI_arid(0);
  s00_couplers_to_s00_couplers_ARLEN(7 downto 0) <= S_AXI_arlen(7 downto 0);
  s00_couplers_to_s00_couplers_ARLOCK(0) <= S_AXI_arlock(0);
  s00_couplers_to_s00_couplers_ARPROT(2 downto 0) <= S_AXI_arprot(2 downto 0);
  s00_couplers_to_s00_couplers_ARQOS(3 downto 0) <= S_AXI_arqos(3 downto 0);
  s00_couplers_to_s00_couplers_ARREADY(0) <= M_AXI_arready(0);
  s00_couplers_to_s00_couplers_ARSIZE(2 downto 0) <= S_AXI_arsize(2 downto 0);
  s00_couplers_to_s00_couplers_ARVALID(0) <= S_AXI_arvalid(0);
  s00_couplers_to_s00_couplers_AWADDR(31 downto 0) <= S_AXI_awaddr(31 downto 0);
  s00_couplers_to_s00_couplers_AWBURST(1 downto 0) <= S_AXI_awburst(1 downto 0);
  s00_couplers_to_s00_couplers_AWCACHE(3 downto 0) <= S_AXI_awcache(3 downto 0);
  s00_couplers_to_s00_couplers_AWID(0) <= S_AXI_awid(0);
  s00_couplers_to_s00_couplers_AWLEN(7 downto 0) <= S_AXI_awlen(7 downto 0);
  s00_couplers_to_s00_couplers_AWLOCK(0) <= S_AXI_awlock(0);
  s00_couplers_to_s00_couplers_AWPROT(2 downto 0) <= S_AXI_awprot(2 downto 0);
  s00_couplers_to_s00_couplers_AWQOS(3 downto 0) <= S_AXI_awqos(3 downto 0);
  s00_couplers_to_s00_couplers_AWREADY(0) <= M_AXI_awready(0);
  s00_couplers_to_s00_couplers_AWSIZE(2 downto 0) <= S_AXI_awsize(2 downto 0);
  s00_couplers_to_s00_couplers_AWVALID(0) <= S_AXI_awvalid(0);
  s00_couplers_to_s00_couplers_BID(0) <= M_AXI_bid(0);
  s00_couplers_to_s00_couplers_BREADY(0) <= S_AXI_bready(0);
  s00_couplers_to_s00_couplers_BRESP(1 downto 0) <= M_AXI_bresp(1 downto 0);
  s00_couplers_to_s00_couplers_BVALID(0) <= M_AXI_bvalid(0);
  s00_couplers_to_s00_couplers_RDATA(31 downto 0) <= M_AXI_rdata(31 downto 0);
  s00_couplers_to_s00_couplers_RID(0) <= M_AXI_rid(0);
  s00_couplers_to_s00_couplers_RLAST(0) <= M_AXI_rlast(0);
  s00_couplers_to_s00_couplers_RREADY(0) <= S_AXI_rready(0);
  s00_couplers_to_s00_couplers_RRESP(1 downto 0) <= M_AXI_rresp(1 downto 0);
  s00_couplers_to_s00_couplers_RVALID(0) <= M_AXI_rvalid(0);
  s00_couplers_to_s00_couplers_WDATA(31 downto 0) <= S_AXI_wdata(31 downto 0);
  s00_couplers_to_s00_couplers_WLAST(0) <= S_AXI_wlast(0);
  s00_couplers_to_s00_couplers_WREADY(0) <= M_AXI_wready(0);
  s00_couplers_to_s00_couplers_WSTRB(3 downto 0) <= S_AXI_wstrb(3 downto 0);
  s00_couplers_to_s00_couplers_WVALID(0) <= S_AXI_wvalid(0);
end STRUCTURE;
library IEEE;
use IEEE.STD_LOGIC_1164.ALL;
library UNISIM;
use UNISIM.VCOMPONENTS.ALL;
entity s01_couplers_imp_1W60HW0 is
  port (
    M_ACLK : in STD_LOGIC;
    M_ARESETN : in STD_LOGIC_VECTOR ( 0 to 0 );
    M_AXI_araddr : out STD_LOGIC_VECTOR ( 31 downto 0 );
    M_AXI_arburst : out STD_LOGIC_VECTOR ( 1 downto 0 );
    M_AXI_arcache : out STD_LOGIC_VECTOR ( 3 downto 0 );
    M_AXI_arid : out STD_LOGIC_VECTOR ( 0 to 0 );
    M_AXI_arlen : out STD_LOGIC_VECTOR ( 7 downto 0 );
    M_AXI_arlock : out STD_LOGIC_VECTOR ( 0 to 0 );
    M_AXI_arprot : out STD_LOGIC_VECTOR ( 2 downto 0 );
    M_AXI_arqos : out STD_LOGIC_VECTOR ( 3 downto 0 );
    M_AXI_arready : in STD_LOGIC_VECTOR ( 0 to 0 );
    M_AXI_arsize : out STD_LOGIC_VECTOR ( 2 downto 0 );
    M_AXI_arvalid : out STD_LOGIC_VECTOR ( 0 to 0 );
    M_AXI_awaddr : out STD_LOGIC_VECTOR ( 31 downto 0 );
    M_AXI_awburst : out STD_LOGIC_VECTOR ( 1 downto 0 );
    M_AXI_awcache : out STD_LOGIC_VECTOR ( 3 downto 0 );
    M_AXI_awid : out STD_LOGIC_VECTOR ( 0 to 0 );
    M_AXI_awlen : out STD_LOGIC_VECTOR ( 7 downto 0 );
    M_AXI_awlock : out STD_LOGIC_VECTOR ( 0 to 0 );
    M_AXI_awprot : out STD_LOGIC_VECTOR ( 2 downto 0 );
    M_AXI_awqos : out STD_LOGIC_VECTOR ( 3 downto 0 );
    M_AXI_awready : in STD_LOGIC_VECTOR ( 0 to 0 );
    M_AXI_awsize : out STD_LOGIC_VECTOR ( 2 downto 0 );
    M_AXI_awvalid : out STD_LOGIC_VECTOR ( 0 to 0 );
    M_AXI_bid : in STD_LOGIC_VECTOR ( 0 to 0 );
    M_AXI_bready : out STD_LOGIC_VECTOR ( 0 to 0 );
    M_AXI_bresp : in STD_LOGIC_VECTOR ( 1 downto 0 );
    M_AXI_bvalid : in STD_LOGIC_VECTOR ( 0 to 0 );
    M_AXI_rdata : in STD_LOGIC_VECTOR ( 31 downto 0 );
    M_AXI_rid : in STD_LOGIC_VECTOR ( 0 to 0 );
    M_AXI_rlast : in STD_LOGIC_VECTOR ( 0 to 0 );
    M_AXI_rready : out STD_LOGIC_VECTOR ( 0 to 0 );
    M_AXI_rresp : in STD_LOGIC_VECTOR ( 1 downto 0 );
    M_AXI_rvalid : in STD_LOGIC_VECTOR ( 0 to 0 );
    M_AXI_wdata : out STD_LOGIC_VECTOR ( 31 downto 0 );
    M_AXI_wlast : out STD_LOGIC_VECTOR ( 0 to 0 );
    M_AXI_wready : in STD_LOGIC_VECTOR ( 0 to 0 );
    M_AXI_wstrb : out STD_LOGIC_VECTOR ( 3 downto 0 );
    M_AXI_wvalid : out STD_LOGIC_VECTOR ( 0 to 0 );
    S_ACLK : in STD_LOGIC;
    S_ARESETN : in STD_LOGIC_VECTOR ( 0 to 0 );
    S_AXI_araddr : in STD_LOGIC_VECTOR ( 31 downto 0 );
    S_AXI_arburst : in STD_LOGIC_VECTOR ( 1 downto 0 );
    S_AXI_arcache : in STD_LOGIC_VECTOR ( 3 downto 0 );
    S_AXI_arid : in STD_LOGIC_VECTOR ( 0 to 0 );
    S_AXI_arlen : in STD_LOGIC_VECTOR ( 7 downto 0 );
    S_AXI_arlock : in STD_LOGIC_VECTOR ( 0 to 0 );
    S_AXI_arprot : in STD_LOGIC_VECTOR ( 2 downto 0 );
    S_AXI_arqos : in STD_LOGIC_VECTOR ( 3 downto 0 );
    S_AXI_arready : out STD_LOGIC_VECTOR ( 0 to 0 );
    S_AXI_arsize : in STD_LOGIC_VECTOR ( 2 downto 0 );
    S_AXI_arvalid : in STD_LOGIC_VECTOR ( 0 to 0 );
    S_AXI_awaddr : in STD_LOGIC_VECTOR ( 31 downto 0 );
    S_AXI_awburst : in STD_LOGIC_VECTOR ( 1 downto 0 );
    S_AXI_awcache : in STD_LOGIC_VECTOR ( 3 downto 0 );
    S_AXI_awid : in STD_LOGIC_VECTOR ( 0 to 0 );
    S_AXI_awlen : in STD_LOGIC_VECTOR ( 7 downto 0 );
    S_AXI_awlock : in STD_LOGIC_VECTOR ( 0 to 0 );
    S_AXI_awprot : in STD_LOGIC_VECTOR ( 2 downto 0 );
    S_AXI_awqos : in STD_LOGIC_VECTOR ( 3 downto 0 );
    S_AXI_awready : out STD_LOGIC_VECTOR ( 0 to 0 );
    S_AXI_awsize : in STD_LOGIC_VECTOR ( 2 downto 0 );
    S_AXI_awvalid : in STD_LOGIC_VECTOR ( 0 to 0 );
    S_AXI_bid : out STD_LOGIC_VECTOR ( 0 to 0 );
    S_AXI_bready : in STD_LOGIC_VECTOR ( 0 to 0 );
    S_AXI_bresp : out STD_LOGIC_VECTOR ( 1 downto 0 );
    S_AXI_bvalid : out STD_LOGIC_VECTOR ( 0 to 0 );
    S_AXI_rdata : out STD_LOGIC_VECTOR ( 31 downto 0 );
    S_AXI_rid : out STD_LOGIC_VECTOR ( 0 to 0 );
    S_AXI_rlast : out STD_LOGIC_VECTOR ( 0 to 0 );
    S_AXI_rready : in STD_LOGIC_VECTOR ( 0 to 0 );
    S_AXI_rresp : out STD_LOGIC_VECTOR ( 1 downto 0 );
    S_AXI_rvalid : out STD_LOGIC_VECTOR ( 0 to 0 );
    S_AXI_wdata : in STD_LOGIC_VECTOR ( 31 downto 0 );
    S_AXI_wlast : in STD_LOGIC_VECTOR ( 0 to 0 );
    S_AXI_wready : out STD_LOGIC_VECTOR ( 0 to 0 );
    S_AXI_wstrb : in STD_LOGIC_VECTOR ( 3 downto 0 );
    S_AXI_wvalid : in STD_LOGIC_VECTOR ( 0 to 0 )
  );
end s01_couplers_imp_1W60HW0;

architecture STRUCTURE of s01_couplers_imp_1W60HW0 is
  signal s01_couplers_to_s01_couplers_ARADDR : STD_LOGIC_VECTOR ( 31 downto 0 );
  signal s01_couplers_to_s01_couplers_ARBURST : STD_LOGIC_VECTOR ( 1 downto 0 );
  signal s01_couplers_to_s01_couplers_ARCACHE : STD_LOGIC_VECTOR ( 3 downto 0 );
  signal s01_couplers_to_s01_couplers_ARID : STD_LOGIC_VECTOR ( 0 to 0 );
  signal s01_couplers_to_s01_couplers_ARLEN : STD_LOGIC_VECTOR ( 7 downto 0 );
  signal s01_couplers_to_s01_couplers_ARLOCK : STD_LOGIC_VECTOR ( 0 to 0 );
  signal s01_couplers_to_s01_couplers_ARPROT : STD_LOGIC_VECTOR ( 2 downto 0 );
  signal s01_couplers_to_s01_couplers_ARQOS : STD_LOGIC_VECTOR ( 3 downto 0 );
  signal s01_couplers_to_s01_couplers_ARREADY : STD_LOGIC_VECTOR ( 0 to 0 );
  signal s01_couplers_to_s01_couplers_ARSIZE : STD_LOGIC_VECTOR ( 2 downto 0 );
  signal s01_couplers_to_s01_couplers_ARVALID : STD_LOGIC_VECTOR ( 0 to 0 );
  signal s01_couplers_to_s01_couplers_AWADDR : STD_LOGIC_VECTOR ( 31 downto 0 );
  signal s01_couplers_to_s01_couplers_AWBURST : STD_LOGIC_VECTOR ( 1 downto 0 );
  signal s01_couplers_to_s01_couplers_AWCACHE : STD_LOGIC_VECTOR ( 3 downto 0 );
  signal s01_couplers_to_s01_couplers_AWID : STD_LOGIC_VECTOR ( 0 to 0 );
  signal s01_couplers_to_s01_couplers_AWLEN : STD_LOGIC_VECTOR ( 7 downto 0 );
  signal s01_couplers_to_s01_couplers_AWLOCK : STD_LOGIC_VECTOR ( 0 to 0 );
  signal s01_couplers_to_s01_couplers_AWPROT : STD_LOGIC_VECTOR ( 2 downto 0 );
  signal s01_couplers_to_s01_couplers_AWQOS : STD_LOGIC_VECTOR ( 3 downto 0 );
  signal s01_couplers_to_s01_couplers_AWREADY : STD_LOGIC_VECTOR ( 0 to 0 );
  signal s01_couplers_to_s01_couplers_AWSIZE : STD_LOGIC_VECTOR ( 2 downto 0 );
  signal s01_couplers_to_s01_couplers_AWVALID : STD_LOGIC_VECTOR ( 0 to 0 );
  signal s01_couplers_to_s01_couplers_BID : STD_LOGIC_VECTOR ( 0 to 0 );
  signal s01_couplers_to_s01_couplers_BREADY : STD_LOGIC_VECTOR ( 0 to 0 );
  signal s01_couplers_to_s01_couplers_BRESP : STD_LOGIC_VECTOR ( 1 downto 0 );
  signal s01_couplers_to_s01_couplers_BVALID : STD_LOGIC_VECTOR ( 0 to 0 );
  signal s01_couplers_to_s01_couplers_RDATA : STD_LOGIC_VECTOR ( 31 downto 0 );
  signal s01_couplers_to_s01_couplers_RID : STD_LOGIC_VECTOR ( 0 to 0 );
  signal s01_couplers_to_s01_couplers_RLAST : STD_LOGIC_VECTOR ( 0 to 0 );
  signal s01_couplers_to_s01_couplers_RREADY : STD_LOGIC_VECTOR ( 0 to 0 );
  signal s01_couplers_to_s01_couplers_RRESP : STD_LOGIC_VECTOR ( 1 downto 0 );
  signal s01_couplers_to_s01_couplers_RVALID : STD_LOGIC_VECTOR ( 0 to 0 );
  signal s01_couplers_to_s01_couplers_WDATA : STD_LOGIC_VECTOR ( 31 downto 0 );
  signal s01_couplers_to_s01_couplers_WLAST : STD_LOGIC_VECTOR ( 0 to 0 );
  signal s01_couplers_to_s01_couplers_WREADY : STD_LOGIC_VECTOR ( 0 to 0 );
  signal s01_couplers_to_s01_couplers_WSTRB : STD_LOGIC_VECTOR ( 3 downto 0 );
  signal s01_couplers_to_s01_couplers_WVALID : STD_LOGIC_VECTOR ( 0 to 0 );
begin
  M_AXI_araddr(31 downto 0) <= s01_couplers_to_s01_couplers_ARADDR(31 downto 0);
  M_AXI_arburst(1 downto 0) <= s01_couplers_to_s01_couplers_ARBURST(1 downto 0);
  M_AXI_arcache(3 downto 0) <= s01_couplers_to_s01_couplers_ARCACHE(3 downto 0);
  M_AXI_arid(0) <= s01_couplers_to_s01_couplers_ARID(0);
  M_AXI_arlen(7 downto 0) <= s01_couplers_to_s01_couplers_ARLEN(7 downto 0);
  M_AXI_arlock(0) <= s01_couplers_to_s01_couplers_ARLOCK(0);
  M_AXI_arprot(2 downto 0) <= s01_couplers_to_s01_couplers_ARPROT(2 downto 0);
  M_AXI_arqos(3 downto 0) <= s01_couplers_to_s01_couplers_ARQOS(3 downto 0);
  M_AXI_arsize(2 downto 0) <= s01_couplers_to_s01_couplers_ARSIZE(2 downto 0);
  M_AXI_arvalid(0) <= s01_couplers_to_s01_couplers_ARVALID(0);
  M_AXI_awaddr(31 downto 0) <= s01_couplers_to_s01_couplers_AWADDR(31 downto 0);
  M_AXI_awburst(1 downto 0) <= s01_couplers_to_s01_couplers_AWBURST(1 downto 0);
  M_AXI_awcache(3 downto 0) <= s01_couplers_to_s01_couplers_AWCACHE(3 downto 0);
  M_AXI_awid(0) <= s01_couplers_to_s01_couplers_AWID(0);
  M_AXI_awlen(7 downto 0) <= s01_couplers_to_s01_couplers_AWLEN(7 downto 0);
  M_AXI_awlock(0) <= s01_couplers_to_s01_couplers_AWLOCK(0);
  M_AXI_awprot(2 downto 0) <= s01_couplers_to_s01_couplers_AWPROT(2 downto 0);
  M_AXI_awqos(3 downto 0) <= s01_couplers_to_s01_couplers_AWQOS(3 downto 0);
  M_AXI_awsize(2 downto 0) <= s01_couplers_to_s01_couplers_AWSIZE(2 downto 0);
  M_AXI_awvalid(0) <= s01_couplers_to_s01_couplers_AWVALID(0);
  M_AXI_bready(0) <= s01_couplers_to_s01_couplers_BREADY(0);
  M_AXI_rready(0) <= s01_couplers_to_s01_couplers_RREADY(0);
  M_AXI_wdata(31 downto 0) <= s01_couplers_to_s01_couplers_WDATA(31 downto 0);
  M_AXI_wlast(0) <= s01_couplers_to_s01_couplers_WLAST(0);
  M_AXI_wstrb(3 downto 0) <= s01_couplers_to_s01_couplers_WSTRB(3 downto 0);
  M_AXI_wvalid(0) <= s01_couplers_to_s01_couplers_WVALID(0);
  S_AXI_arready(0) <= s01_couplers_to_s01_couplers_ARREADY(0);
  S_AXI_awready(0) <= s01_couplers_to_s01_couplers_AWREADY(0);
  S_AXI_bid(0) <= s01_couplers_to_s01_couplers_BID(0);
  S_AXI_bresp(1 downto 0) <= s01_couplers_to_s01_couplers_BRESP(1 downto 0);
  S_AXI_bvalid(0) <= s01_couplers_to_s01_couplers_BVALID(0);
  S_AXI_rdata(31 downto 0) <= s01_couplers_to_s01_couplers_RDATA(31 downto 0);
  S_AXI_rid(0) <= s01_couplers_to_s01_couplers_RID(0);
  S_AXI_rlast(0) <= s01_couplers_to_s01_couplers_RLAST(0);
  S_AXI_rresp(1 downto 0) <= s01_couplers_to_s01_couplers_RRESP(1 downto 0);
  S_AXI_rvalid(0) <= s01_couplers_to_s01_couplers_RVALID(0);
  S_AXI_wready(0) <= s01_couplers_to_s01_couplers_WREADY(0);
  s01_couplers_to_s01_couplers_ARADDR(31 downto 0) <= S_AXI_araddr(31 downto 0);
  s01_couplers_to_s01_couplers_ARBURST(1 downto 0) <= S_AXI_arburst(1 downto 0);
  s01_couplers_to_s01_couplers_ARCACHE(3 downto 0) <= S_AXI_arcache(3 downto 0);
  s01_couplers_to_s01_couplers_ARID(0) <= S_AXI_arid(0);
  s01_couplers_to_s01_couplers_ARLEN(7 downto 0) <= S_AXI_arlen(7 downto 0);
  s01_couplers_to_s01_couplers_ARLOCK(0) <= S_AXI_arlock(0);
  s01_couplers_to_s01_couplers_ARPROT(2 downto 0) <= S_AXI_arprot(2 downto 0);
  s01_couplers_to_s01_couplers_ARQOS(3 downto 0) <= S_AXI_arqos(3 downto 0);
  s01_couplers_to_s01_couplers_ARREADY(0) <= M_AXI_arready(0);
  s01_couplers_to_s01_couplers_ARSIZE(2 downto 0) <= S_AXI_arsize(2 downto 0);
  s01_couplers_to_s01_couplers_ARVALID(0) <= S_AXI_arvalid(0);
  s01_couplers_to_s01_couplers_AWADDR(31 downto 0) <= S_AXI_awaddr(31 downto 0);
  s01_couplers_to_s01_couplers_AWBURST(1 downto 0) <= S_AXI_awburst(1 downto 0);
  s01_couplers_to_s01_couplers_AWCACHE(3 downto 0) <= S_AXI_awcache(3 downto 0);
  s01_couplers_to_s01_couplers_AWID(0) <= S_AXI_awid(0);
  s01_couplers_to_s01_couplers_AWLEN(7 downto 0) <= S_AXI_awlen(7 downto 0);
  s01_couplers_to_s01_couplers_AWLOCK(0) <= S_AXI_awlock(0);
  s01_couplers_to_s01_couplers_AWPROT(2 downto 0) <= S_AXI_awprot(2 downto 0);
  s01_couplers_to_s01_couplers_AWQOS(3 downto 0) <= S_AXI_awqos(3 downto 0);
  s01_couplers_to_s01_couplers_AWREADY(0) <= M_AXI_awready(0);
  s01_couplers_to_s01_couplers_AWSIZE(2 downto 0) <= S_AXI_awsize(2 downto 0);
  s01_couplers_to_s01_couplers_AWVALID(0) <= S_AXI_awvalid(0);
  s01_couplers_to_s01_couplers_BID(0) <= M_AXI_bid(0);
  s01_couplers_to_s01_couplers_BREADY(0) <= S_AXI_bready(0);
  s01_couplers_to_s01_couplers_BRESP(1 downto 0) <= M_AXI_bresp(1 downto 0);
  s01_couplers_to_s01_couplers_BVALID(0) <= M_AXI_bvalid(0);
  s01_couplers_to_s01_couplers_RDATA(31 downto 0) <= M_AXI_rdata(31 downto 0);
  s01_couplers_to_s01_couplers_RID(0) <= M_AXI_rid(0);
  s01_couplers_to_s01_couplers_RLAST(0) <= M_AXI_rlast(0);
  s01_couplers_to_s01_couplers_RREADY(0) <= S_AXI_rready(0);
  s01_couplers_to_s01_couplers_RRESP(1 downto 0) <= M_AXI_rresp(1 downto 0);
  s01_couplers_to_s01_couplers_RVALID(0) <= M_AXI_rvalid(0);
  s01_couplers_to_s01_couplers_WDATA(31 downto 0) <= S_AXI_wdata(31 downto 0);
  s01_couplers_to_s01_couplers_WLAST(0) <= S_AXI_wlast(0);
  s01_couplers_to_s01_couplers_WREADY(0) <= M_AXI_wready(0);
  s01_couplers_to_s01_couplers_WSTRB(3 downto 0) <= S_AXI_wstrb(3 downto 0);
  s01_couplers_to_s01_couplers_WVALID(0) <= S_AXI_wvalid(0);
end STRUCTURE;
library IEEE;
use IEEE.STD_LOGIC_1164.ALL;
library UNISIM;
use UNISIM.VCOMPONENTS.ALL;
entity design_1_axi_mem_intercon_0 is
  port (
    ACLK : in STD_LOGIC;
    ARESETN : in STD_LOGIC_VECTOR ( 0 to 0 );
    M00_ACLK : in STD_LOGIC;
    M00_ARESETN : in STD_LOGIC_VECTOR ( 0 to 0 );
    M00_AXI_araddr : out STD_LOGIC_VECTOR ( 31 downto 0 );
    M00_AXI_arburst : out STD_LOGIC_VECTOR ( 1 downto 0 );
    M00_AXI_arcache : out STD_LOGIC_VECTOR ( 3 downto 0 );
    M00_AXI_arid : out STD_LOGIC_VECTOR ( 0 to 0 );
    M00_AXI_arlen : out STD_LOGIC_VECTOR ( 7 downto 0 );
    M00_AXI_arlock : out STD_LOGIC_VECTOR ( 0 to 0 );
    M00_AXI_arprot : out STD_LOGIC_VECTOR ( 2 downto 0 );
    M00_AXI_arready : in STD_LOGIC_VECTOR ( 0 to 0 );
    M00_AXI_arsize : out STD_LOGIC_VECTOR ( 2 downto 0 );
    M00_AXI_arvalid : out STD_LOGIC_VECTOR ( 0 to 0 );
    M00_AXI_awaddr : out STD_LOGIC_VECTOR ( 31 downto 0 );
    M00_AXI_awburst : out STD_LOGIC_VECTOR ( 1 downto 0 );
    M00_AXI_awcache : out STD_LOGIC_VECTOR ( 3 downto 0 );
    M00_AXI_awid : out STD_LOGIC_VECTOR ( 0 to 0 );
    M00_AXI_awlen : out STD_LOGIC_VECTOR ( 7 downto 0 );
    M00_AXI_awlock : out STD_LOGIC_VECTOR ( 0 to 0 );
    M00_AXI_awprot : out STD_LOGIC_VECTOR ( 2 downto 0 );
    M00_AXI_awready : in STD_LOGIC_VECTOR ( 0 to 0 );
    M00_AXI_awsize : out STD_LOGIC_VECTOR ( 2 downto 0 );
    M00_AXI_awvalid : out STD_LOGIC_VECTOR ( 0 to 0 );
    M00_AXI_bid : in STD_LOGIC_VECTOR ( 0 to 0 );
    M00_AXI_bready : out STD_LOGIC_VECTOR ( 0 to 0 );
    M00_AXI_bresp : in STD_LOGIC_VECTOR ( 1 downto 0 );
    M00_AXI_bvalid : in STD_LOGIC_VECTOR ( 0 to 0 );
    M00_AXI_rdata : in STD_LOGIC_VECTOR ( 31 downto 0 );
    M00_AXI_rid : in STD_LOGIC_VECTOR ( 0 to 0 );
    M00_AXI_rlast : in STD_LOGIC_VECTOR ( 0 to 0 );
    M00_AXI_rready : out STD_LOGIC_VECTOR ( 0 to 0 );
    M00_AXI_rresp : in STD_LOGIC_VECTOR ( 1 downto 0 );
    M00_AXI_rvalid : in STD_LOGIC_VECTOR ( 0 to 0 );
    M00_AXI_wdata : out STD_LOGIC_VECTOR ( 31 downto 0 );
    M00_AXI_wlast : out STD_LOGIC_VECTOR ( 0 to 0 );
    M00_AXI_wready : in STD_LOGIC_VECTOR ( 0 to 0 );
    M00_AXI_wstrb : out STD_LOGIC_VECTOR ( 3 downto 0 );
    M00_AXI_wvalid : out STD_LOGIC_VECTOR ( 0 to 0 );
    S00_ACLK : in STD_LOGIC;
    S00_ARESETN : in STD_LOGIC_VECTOR ( 0 to 0 );
    S00_AXI_araddr : in STD_LOGIC_VECTOR ( 31 downto 0 );
    S00_AXI_arburst : in STD_LOGIC_VECTOR ( 1 downto 0 );
    S00_AXI_arcache : in STD_LOGIC_VECTOR ( 3 downto 0 );
    S00_AXI_arid : in STD_LOGIC_VECTOR ( 0 to 0 );
    S00_AXI_arlen : in STD_LOGIC_VECTOR ( 7 downto 0 );
    S00_AXI_arlock : in STD_LOGIC_VECTOR ( 0 to 0 );
    S00_AXI_arprot : in STD_LOGIC_VECTOR ( 2 downto 0 );
    S00_AXI_arqos : in STD_LOGIC_VECTOR ( 3 downto 0 );
    S00_AXI_arready : out STD_LOGIC_VECTOR ( 0 to 0 );
    S00_AXI_arsize : in STD_LOGIC_VECTOR ( 2 downto 0 );
    S00_AXI_arvalid : in STD_LOGIC_VECTOR ( 0 to 0 );
    S00_AXI_awaddr : in STD_LOGIC_VECTOR ( 31 downto 0 );
    S00_AXI_awburst : in STD_LOGIC_VECTOR ( 1 downto 0 );
    S00_AXI_awcache : in STD_LOGIC_VECTOR ( 3 downto 0 );
    S00_AXI_awid : in STD_LOGIC_VECTOR ( 0 to 0 );
    S00_AXI_awlen : in STD_LOGIC_VECTOR ( 7 downto 0 );
    S00_AXI_awlock : in STD_LOGIC_VECTOR ( 0 to 0 );
    S00_AXI_awprot : in STD_LOGIC_VECTOR ( 2 downto 0 );
    S00_AXI_awqos : in STD_LOGIC_VECTOR ( 3 downto 0 );
    S00_AXI_awready : out STD_LOGIC_VECTOR ( 0 to 0 );
    S00_AXI_awsize : in STD_LOGIC_VECTOR ( 2 downto 0 );
    S00_AXI_awvalid : in STD_LOGIC_VECTOR ( 0 to 0 );
    S00_AXI_bid : out STD_LOGIC_VECTOR ( 0 to 0 );
    S00_AXI_bready : in STD_LOGIC_VECTOR ( 0 to 0 );
    S00_AXI_bresp : out STD_LOGIC_VECTOR ( 1 downto 0 );
    S00_AXI_bvalid : out STD_LOGIC_VECTOR ( 0 to 0 );
    S00_AXI_rdata : out STD_LOGIC_VECTOR ( 31 downto 0 );
    S00_AXI_rid : out STD_LOGIC_VECTOR ( 0 to 0 );
    S00_AXI_rlast : out STD_LOGIC_VECTOR ( 0 to 0 );
    S00_AXI_rready : in STD_LOGIC_VECTOR ( 0 to 0 );
    S00_AXI_rresp : out STD_LOGIC_VECTOR ( 1 downto 0 );
    S00_AXI_rvalid : out STD_LOGIC_VECTOR ( 0 to 0 );
    S00_AXI_wdata : in STD_LOGIC_VECTOR ( 31 downto 0 );
    S00_AXI_wlast : in STD_LOGIC_VECTOR ( 0 to 0 );
    S00_AXI_wready : out STD_LOGIC_VECTOR ( 0 to 0 );
    S00_AXI_wstrb : in STD_LOGIC_VECTOR ( 3 downto 0 );
    S00_AXI_wvalid : in STD_LOGIC_VECTOR ( 0 to 0 );
    S01_ACLK : in STD_LOGIC;
    S01_ARESETN : in STD_LOGIC_VECTOR ( 0 to 0 );
    S01_AXI_araddr : in STD_LOGIC_VECTOR ( 31 downto 0 );
    S01_AXI_arburst : in STD_LOGIC_VECTOR ( 1 downto 0 );
    S01_AXI_arcache : in STD_LOGIC_VECTOR ( 3 downto 0 );
    S01_AXI_arid : in STD_LOGIC_VECTOR ( 0 to 0 );
    S01_AXI_arlen : in STD_LOGIC_VECTOR ( 7 downto 0 );
    S01_AXI_arlock : in STD_LOGIC_VECTOR ( 0 to 0 );
    S01_AXI_arprot : in STD_LOGIC_VECTOR ( 2 downto 0 );
    S01_AXI_arqos : in STD_LOGIC_VECTOR ( 3 downto 0 );
    S01_AXI_arready : out STD_LOGIC_VECTOR ( 0 to 0 );
    S01_AXI_arsize : in STD_LOGIC_VECTOR ( 2 downto 0 );
    S01_AXI_arvalid : in STD_LOGIC_VECTOR ( 0 to 0 );
    S01_AXI_awaddr : in STD_LOGIC_VECTOR ( 31 downto 0 );
    S01_AXI_awburst : in STD_LOGIC_VECTOR ( 1 downto 0 );
    S01_AXI_awcache : in STD_LOGIC_VECTOR ( 3 downto 0 );
    S01_AXI_awid : in STD_LOGIC_VECTOR ( 0 to 0 );
    S01_AXI_awlen : in STD_LOGIC_VECTOR ( 7 downto 0 );
    S01_AXI_awlock : in STD_LOGIC_VECTOR ( 0 to 0 );
    S01_AXI_awprot : in STD_LOGIC_VECTOR ( 2 downto 0 );
    S01_AXI_awqos : in STD_LOGIC_VECTOR ( 3 downto 0 );
    S01_AXI_awready : out STD_LOGIC_VECTOR ( 0 to 0 );
    S01_AXI_awsize : in STD_LOGIC_VECTOR ( 2 downto 0 );
    S01_AXI_awvalid : in STD_LOGIC_VECTOR ( 0 to 0 );
    S01_AXI_bid : out STD_LOGIC_VECTOR ( 0 to 0 );
    S01_AXI_bready : in STD_LOGIC_VECTOR ( 0 to 0 );
    S01_AXI_bresp : out STD_LOGIC_VECTOR ( 1 downto 0 );
    S01_AXI_bvalid : out STD_LOGIC_VECTOR ( 0 to 0 );
    S01_AXI_rdata : out STD_LOGIC_VECTOR ( 31 downto 0 );
    S01_AXI_rid : out STD_LOGIC_VECTOR ( 0 to 0 );
    S01_AXI_rlast : out STD_LOGIC_VECTOR ( 0 to 0 );
    S01_AXI_rready : in STD_LOGIC_VECTOR ( 0 to 0 );
    S01_AXI_rresp : out STD_LOGIC_VECTOR ( 1 downto 0 );
    S01_AXI_rvalid : out STD_LOGIC_VECTOR ( 0 to 0 );
    S01_AXI_wdata : in STD_LOGIC_VECTOR ( 31 downto 0 );
    S01_AXI_wlast : in STD_LOGIC_VECTOR ( 0 to 0 );
    S01_AXI_wready : out STD_LOGIC_VECTOR ( 0 to 0 );
    S01_AXI_wstrb : in STD_LOGIC_VECTOR ( 3 downto 0 );
    S01_AXI_wvalid : in STD_LOGIC_VECTOR ( 0 to 0 )
  );
end design_1_axi_mem_intercon_0;
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
