AlistairCheeseman/WindTunnelApparatus/Firmware/Tests/FPGA/FPGAUDPtest/GSMBS2015.2.srcs/sources_1/bd/design_1/hdl/design_1_wrapper.vhd

--Copyright 1986-2015 Xilinx, Inc. All Rights Reserved.
----------------------------------------------------------------------------------
--Tool Version: Vivado v.2015.2 (win64) Build 1266856 Fri Jun 26 16:35:25 MDT 2015
--Date        : Thu Nov 19 17:38:29 2015
--Host        : ALI-WORKSTATION running 64-bit major release  (build 9200)
--Command     : generate_target design_1_wrapper.bd
--Design      : design_1_wrapper
--Purpose     : IP block netlist
----------------------------------------------------------------------------------
library IEEE;
use IEEE.STD_LOGIC_1164.ALL;
library UNISIM;
use UNISIM.VCOMPONENTS.ALL;
entity design_1_wrapper is
  port (
    cellular_ram_addr : out STD_LOGIC_VECTOR ( 22 downto 0 );
    cellular_ram_adv_ldn : out STD_LOGIC;
    cellular_ram_ben : out STD_LOGIC_VECTOR ( 1 downto 0 );
    cellular_ram_ce_n : out STD_LOGIC;
    cellular_ram_cre : out STD_LOGIC;
    cellular_ram_dq_io : inout STD_LOGIC_VECTOR ( 15 downto 0 );
    cellular_ram_oen : out STD_LOGIC;
    cellular_ram_wait : in STD_LOGIC;
    cellular_ram_wen : out STD_LOGIC;
    eth_mdio_mdc_mdc : out STD_LOGIC;
    eth_mdio_mdc_mdio_io : inout STD_LOGIC;
    eth_ref_clk : out STD_LOGIC;
    eth_rmii_crs_dv : in STD_LOGIC;
    eth_rmii_rx_er : in STD_LOGIC;
    eth_rmii_rxd : in STD_LOGIC_VECTOR ( 1 downto 0 );
    eth_rmii_tx_en : out STD_LOGIC;
    eth_rmii_txd : out STD_LOGIC_VECTOR ( 1 downto 0 );
    reset : in STD_LOGIC;
    sys_clock : in STD_LOGIC;
    usb_uart_rxd : in STD_LOGIC;
    usb_uart_txd : out STD_LOGIC
  );
end design_1_wrapper;

architecture STRUCTURE of design_1_wrapper is
  component design_1 is
  port (
    cellular_ram_addr : out STD_LOGIC_VECTOR ( 22 downto 0 );
    cellular_ram_adv_ldn : out STD_LOGIC;
    cellular_ram_ben : out STD_LOGIC_VECTOR ( 1 downto 0 );
    cellular_ram_ce_n : out STD_LOGIC;
    cellular_ram_cre : out STD_LOGIC;
    cellular_ram_dq_i : in STD_LOGIC_VECTOR ( 15 downto 0 );
    cellular_ram_dq_o : out STD_LOGIC_VECTOR ( 15 downto 0 );
    cellular_ram_dq_t : out STD_LOGIC_VECTOR ( 15 downto 0 );
    cellular_ram_oen : out STD_LOGIC;
    cellular_ram_wait : in STD_LOGIC;
    cellular_ram_wen : out STD_LOGIC;
    usb_uart_rxd : in STD_LOGIC;
    usb_uart_txd : out STD_LOGIC;
    eth_rmii_crs_dv : in STD_LOGIC;
    eth_rmii_rx_er : in STD_LOGIC;
    eth_rmii_rxd : in STD_LOGIC_VECTOR ( 1 downto 0 );
    eth_rmii_tx_en : out STD_LOGIC;
    eth_rmii_txd : out STD_LOGIC_VECTOR ( 1 downto 0 );
    eth_mdio_mdc_mdc : out STD_LOGIC;
    eth_mdio_mdc_mdio_i : in STD_LOGIC;
    eth_mdio_mdc_mdio_o : out STD_LOGIC;
    eth_mdio_mdc_mdio_t : out STD_LOGIC;
    reset : in STD_LOGIC;
    eth_ref_clk : out STD_LOGIC;
    sys_clock : in STD_LOGIC
  );
  end component design_1;
  component IOBUF is
  port (
    I : in STD_LOGIC;
    O : out STD_LOGIC;
    T : in STD_LOGIC;
    IO : inout STD_LOGIC
  );
  end component IOBUF;
  signal cellular_ram_dq_i_0 : STD_LOGIC_VECTOR ( 0 to 0 );
  signal cellular_ram_dq_i_1 : STD_LOGIC_VECTOR ( 1 to 1 );
  signal cellular_ram_dq_i_10 : STD_LOGIC_VECTOR ( 10 to 10 );
  signal cellular_ram_dq_i_11 : STD_LOGIC_VECTOR ( 11 to 11 );
  signal cellular_ram_dq_i_12 : STD_LOGIC_VECTOR ( 12 to 12 );
  signal cellular_ram_dq_i_13 : STD_LOGIC_VECTOR ( 13 to 13 );
  signal cellular_ram_dq_i_14 : STD_LOGIC_VECTOR ( 14 to 14 );
  signal cellular_ram_dq_i_15 : STD_LOGIC_VECTOR ( 15 to 15 );
  signal cellular_ram_dq_i_2 : STD_LOGIC_VECTOR ( 2 to 2 );
  signal cellular_ram_dq_i_3 : STD_LOGIC_VECTOR ( 3 to 3 );
  signal cellular_ram_dq_i_4 : STD_LOGIC_VECTOR ( 4 to 4 );
  signal cellular_ram_dq_i_5 : STD_LOGIC_VECTOR ( 5 to 5 );
  signal cellular_ram_dq_i_6 : STD_LOGIC_VECTOR ( 6 to 6 );
  signal cellular_ram_dq_i_7 : STD_LOGIC_VECTOR ( 7 to 7 );
  signal cellular_ram_dq_i_8 : STD_LOGIC_VECTOR ( 8 to 8 );
  signal cellular_ram_dq_i_9 : STD_LOGIC_VECTOR ( 9 to 9 );
  signal cellular_ram_dq_io_0 : STD_LOGIC_VECTOR ( 0 to 0 );
  signal cellular_ram_dq_io_1 : STD_LOGIC_VECTOR ( 1 to 1 );
  signal cellular_ram_dq_io_10 : STD_LOGIC_VECTOR ( 10 to 10 );
  signal cellular_ram_dq_io_11 : STD_LOGIC_VECTOR ( 11 to 11 );
  signal cellular_ram_dq_io_12 : STD_LOGIC_VECTOR ( 12 to 12 );
  signal cellular_ram_dq_io_13 : STD_LOGIC_VECTOR ( 13 to 13 );
  signal cellular_ram_dq_io_14 : STD_LOGIC_VECTOR ( 14 to 14 );
  signal cellular_ram_dq_io_15 : STD_LOGIC_VECTOR ( 15 to 15 );
  signal cellular_ram_dq_io_2 : STD_LOGIC_VECTOR ( 2 to 2 );
  signal cellular_ram_dq_io_3 : STD_LOGIC_VECTOR ( 3 to 3 );
  signal cellular_ram_dq_io_4 : STD_LOGIC_VECTOR ( 4 to 4 );
  signal cellular_ram_dq_io_5 : STD_LOGIC_VECTOR ( 5 to 5 );
  signal cellular_ram_dq_io_6 : STD_LOGIC_VECTOR ( 6 to 6 );
  signal cellular_ram_dq_io_7 : STD_LOGIC_VECTOR ( 7 to 7 );
  signal cellular_ram_dq_io_8 : STD_LOGIC_VECTOR ( 8 to 8 );
  signal cellular_ram_dq_io_9 : STD_LOGIC_VECTOR ( 9 to 9 );
  signal cellular_ram_dq_o_0 : STD_LOGIC_VECTOR ( 0 to 0 );
  signal cellular_ram_dq_o_1 : STD_LOGIC_VECTOR ( 1 to 1 );
  signal cellular_ram_dq_o_10 : STD_LOGIC_VECTOR ( 10 to 10 );
  signal cellular_ram_dq_o_11 : STD_LOGIC_VECTOR ( 11 to 11 );
  signal cellular_ram_dq_o_12 : STD_LOGIC_VECTOR ( 12 to 12 );
  signal cellular_ram_dq_o_13 : STD_LOGIC_VECTOR ( 13 to 13 );
  signal cellular_ram_dq_o_14 : STD_LOGIC_VECTOR ( 14 to 14 );
  signal cellular_ram_dq_o_15 : STD_LOGIC_VECTOR ( 15 to 15 );
  signal cellular_ram_dq_o_2 : STD_LOGIC_VECTOR ( 2 to 2 );
  signal cellular_ram_dq_o_3 : STD_LOGIC_VECTOR ( 3 to 3 );
  signal cellular_ram_dq_o_4 : STD_LOGIC_VECTOR ( 4 to 4 );
  signal cellular_ram_dq_o_5 : STD_LOGIC_VECTOR ( 5 to 5 );
  signal cellular_ram_dq_o_6 : STD_LOGIC_VECTOR ( 6 to 6 );
  signal cellular_ram_dq_o_7 : STD_LOGIC_VECTOR ( 7 to 7 );
  signal cellular_ram_dq_o_8 : STD_LOGIC_VECTOR ( 8 to 8 );
  signal cellular_ram_dq_o_9 : STD_LOGIC_VECTOR ( 9 to 9 );
  signal cellular_ram_dq_t_0 : STD_LOGIC_VECTOR ( 0 to 0 );
  signal cellular_ram_dq_t_1 : STD_LOGIC_VECTOR ( 1 to 1 );
  signal cellular_ram_dq_t_10 : STD_LOGIC_VECTOR ( 10 to 10 );
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
      cellular_ram_dq_t(0) => cellular_ram_dq_t_0(0),
      cellular_ram_oen => cellular_ram_oen,
      cellular_ram_wait => cellular_ram_wait,
      cellular_ram_wen => cellular_ram_wen,
      eth_mdio_mdc_mdc => eth_mdio_mdc_mdc,
      eth_mdio_mdc_mdio_i => eth_mdio_mdc_mdio_i,
      eth_mdio_mdc_mdio_o => eth_mdio_mdc_mdio_o,
      eth_mdio_mdc_mdio_t => eth_mdio_mdc_mdio_t,
      eth_ref_clk => eth_ref_clk,
      eth_rmii_crs_dv => eth_rmii_crs_dv,
      eth_rmii_rx_er => eth_rmii_rx_er,
      eth_rmii_rxd(1 downto 0) => eth_rmii_rxd(1 downto 0),
      eth_rmii_tx_en => eth_rmii_tx_en,
      eth_rmii_txd(1 downto 0) => eth_rmii_txd(1 downto 0),
      reset => reset,
      sys_clock => sys_clock,
      usb_uart_rxd => usb_uart_rxd,
      usb_uart_txd => usb_uart_txd
    );
eth_mdio_mdc_mdio_iobuf: component IOBUF
     port map (
      I => eth_mdio_mdc_mdio_o,
      IO => eth_mdio_mdc_mdio_io,
      O => eth_mdio_mdc_mdio_i,
      T => eth_mdio_mdc_mdio_t
    );
end STRUCTURE;
