AlistairCheeseman/WindTunnelApparatus/Firmware/Tests/FPGA/FPGAEchoExample/GSMBS2015.2.srcs/sources_1/bd/design_1/ip/design_1_mdm_1_0/synth/design_1_mdm_1_0.vhd

-- (c) Copyright 1995-2015 Xilinx, Inc. All rights reserved.
-- 
-- This file contains confidential and proprietary information
-- of Xilinx, Inc. and is protected under U.S. and
-- international copyright and other intellectual property
-- laws.
-- 
-- DISCLAIMER
-- This disclaimer is not a license and does not grant any
-- rights to the materials distributed herewith. Except as
-- otherwise provided in a valid license issued to you by
-- Xilinx, and to the maximum extent permitted by applicable
-- law: (1) THESE MATERIALS ARE MADE AVAILABLE "AS IS" AND
-- WITH ALL FAULTS, AND XILINX HEREBY DISCLAIMS ALL WARRANTIES
-- AND CONDITIONS, EXPRESS, IMPLIED, OR STATUTORY, INCLUDING
-- BUT NOT LIMITED TO WARRANTIES OF MERCHANTABILITY, NON-
-- INFRINGEMENT, OR FITNESS FOR ANY PARTICULAR PURPOSE; and
-- (2) Xilinx shall not be liable (whether in contract or tort,
-- including negligence, or under any other theory of
-- liability) for any loss or damage of any kind or nature
-- related to, arising under or in connection with these
-- materials, including for any direct, or any indirect,
-- special, incidental, or consequential loss or damage
-- (including loss of data, profits, goodwill, or any type of
-- loss or damage suffered as a result of any action brought
-- by a third party) even if such damage or loss was
-- reasonably foreseeable or Xilinx had been advised of the
-- possibility of the same.
-- 
-- CRITICAL APPLICATIONS
-- Xilinx products are not designed or intended to be fail-
-- safe, or for use in any application requiring fail-safe
-- performance, such as life-support or safety devices or
-- systems, Class III medical devices, nuclear facilities,
-- applications related to the deployment of airbags, or any
-- other applications that could lead to death, personal
-- injury, or severe property or environmental damage
-- (individually and collectively, "Critical
-- Applications"). Customer assumes the sole risk and
-- liability of any use of Xilinx products in Critical
-- Applications, subject only to applicable laws and
-- regulations governing limitations on product liability.
-- 
-- THIS COPYRIGHT NOTICE AND DISCLAIMER MUST BE RETAINED AS
-- PART OF THIS FILE AT ALL TIMES.
-- 
-- DO NOT MODIFY THIS FILE.

-- IP VLNV: xilinx.com:ip:mdm:3.2
-- IP Revision: 3

LIBRARY ieee;
USE ieee.std_logic_1164.ALL;
USE ieee.numeric_std.ALL;

LIBRARY mdm_v3_2;
USE mdm_v3_2.MDM;

ENTITY design_1_mdm_1_0 IS
  PORT (
    Debug_SYS_Rst : OUT STD_LOGIC;
    Dbg_Clk_0 : OUT STD_LOGIC;
    Dbg_TDI_0 : OUT STD_LOGIC;
    Dbg_TDO_0 : IN STD_LOGIC;
    Dbg_Reg_En_0 : OUT STD_LOGIC_VECTOR(0 TO 7);
    Dbg_Capture_0 : OUT STD_LOGIC;
    Dbg_Shift_0 : OUT STD_LOGIC;
    Dbg_Update_0 : OUT STD_LOGIC;
    Dbg_Rst_0 : OUT STD_LOGIC
  );
END design_1_mdm_1_0;

ARCHITECTURE design_1_mdm_1_0_arch OF design_1_mdm_1_0 IS
  ATTRIBUTE DowngradeIPIdentifiedWarnings : string;
  ATTRIBUTE DowngradeIPIdentifiedWarnings OF design_1_mdm_1_0_arch: ARCHITECTURE IS "yes";

  COMPONENT MDM IS
    GENERIC (
      C_FAMILY : STRING;
      C_JTAG_CHAIN : INTEGER;
      C_USE_BSCAN : INTEGER;
      C_USE_CONFIG_RESET : INTEGER;
      C_INTERCONNECT : INTEGER;
      C_MB_DBG_PORTS : INTEGER;
      C_USE_UART : INTEGER;
      C_DBG_REG_ACCESS : INTEGER;
      C_DBG_MEM_ACCESS : INTEGER;
      C_USE_CROSS_TRIGGER : INTEGER;
      C_TRACE_OUTPUT : INTEGER;
      C_TRACE_DATA_WIDTH : INTEGER;
      C_TRACE_CLK_FREQ_HZ : INTEGER;
      C_TRACE_CLK_OUT_PHASE : INTEGER;
      C_S_AXI_ADDR_WIDTH : INTEGER;
      C_S_AXI_DATA_WIDTH : INTEGER;
      C_S_AXI_ACLK_FREQ_HZ : INTEGER;
      C_M_AXI_ADDR_WIDTH : INTEGER;
      C_M_AXI_DATA_WIDTH : INTEGER;
      C_M_AXI_THREAD_ID_WIDTH : INTEGER;
      C_DATA_SIZE : INTEGER;
      C_M_AXIS_DATA_WIDTH : INTEGER;
      C_M_AXIS_ID_WIDTH : INTEGER
    );
    PORT (
      Config_Reset : IN STD_LOGIC;
      Scan_Reset : IN STD_LOGIC;
      Scan_Reset_Sel : IN STD_LOGIC;
      S_AXI_ACLK : IN STD_LOGIC;
      S_AXI_ARESETN : IN STD_LOGIC;
      M_AXI_ACLK : IN STD_LOGIC;
      M_AXI_ARESETN : IN STD_LOGIC;
      M_AXIS_ACLK : IN STD_LOGIC;
      M_AXIS_ARESETN : IN STD_LOGIC;
      Interrupt : OUT STD_LOGIC;
      Ext_BRK : OUT STD_LOGIC;
      Ext_NM_BRK : OUT STD_LOGIC;
      Debug_SYS_Rst : OUT STD_LOGIC;
      Trig_In_0 : IN STD_LOGIC;
      Trig_Ack_In_0 : OUT STD_LOGIC;
      Trig_Out_0 : OUT STD_LOGIC;
      Trig_Ack_Out_0 : IN STD_LOGIC;
      Trig_In_1 : IN STD_LOGIC;
      Trig_Ack_In_1 : OUT STD_LOGIC;
      Trig_Out_1 : OUT STD_LOGIC;
      Trig_Ack_Out_1 : IN STD_LOGIC;
      Trig_In_2 : IN STD_LOGIC;
      Trig_Ack_In_2 : OUT STD_LOGIC;
      Trig_Out_2 : OUT STD_LOGIC;
      Trig_Ack_Out_2 : IN STD_LOGIC;
      Trig_In_3 : IN STD_LOGIC;
      Trig_Ack_In_3 : OUT STD_LOGIC;
      Trig_Out_3 : OUT STD_LOGIC;
      Trig_Ack_Out_3 : IN STD_LOGIC;
      S_AXI_AWADDR : IN STD_LOGIC_VECTOR(31 DOWNTO 0);
      S_AXI_AWVALID : IN STD_LOGIC;
      S_AXI_AWREADY : OUT STD_LOGIC;
      S_AXI_WDATA : IN STD_LOGIC_VECTOR(31 DOWNTO 0);
      S_AXI_WSTRB : IN STD_LOGIC_VECTOR(3 DOWNTO 0);
      S_AXI_WVALID : IN STD_LOGIC;
      S_AXI_WREADY : OUT STD_LOGIC;
      S_AXI_BRESP : OUT STD_LOGIC_VECTOR(1 DOWNTO 0);
      S_AXI_BVALID : OUT STD_LOGIC;
      S_AXI_BREADY : IN STD_LOGIC;
      S_AXI_ARADDR : IN STD_LOGIC_VECTOR(31 DOWNTO 0);
      S_AXI_ARVALID : IN STD_LOGIC;
      S_AXI_ARREADY : OUT STD_LOGIC;
      S_AXI_RDATA : OUT STD_LOGIC_VECTOR(31 DOWNTO 0);
      S_AXI_RRESP : OUT STD_LOGIC_VECTOR(1 DOWNTO 0);
      S_AXI_RVALID : OUT STD_LOGIC;
      S_AXI_RREADY : IN STD_LOGIC;
      M_AXI_AWID : OUT STD_LOGIC_VECTOR(0 DOWNTO 0);
      M_AXI_AWADDR : OUT STD_LOGIC_VECTOR(31 DOWNTO 0);
      M_AXI_AWLEN : OUT STD_LOGIC_VECTOR(7 DOWNTO 0);
      M_AXI_AWSIZE : OUT STD_LOGIC_VECTOR(2 DOWNTO 0);
      M_AXI_AWBURST : OUT STD_LOGIC_VECTOR(1 DOWNTO 0);
      M_AXI_AWLOCK : OUT STD_LOGIC;
      M_AXI_AWCACHE : OUT STD_LOGIC_VECTOR(3 DOWNTO 0);
      M_AXI_AWPROT : OUT STD_LOGIC_VECTOR(2 DOWNTO 0);
      M_AXI_AWQOS : OUT STD_LOGIC_VECTOR(3 DOWNTO 0);
      M_AXI_AWVALID : OUT STD_LOGIC;
      M_AXI_AWREADY : IN STD_LOGIC;
      M_AXI_WDATA : OUT STD_LOGIC_VECTOR(31 DOWNTO 0);
      M_AXI_WSTRB : OUT STD_LOGIC_VECTOR(3 DOWNTO 0);
      M_AXI_WLAST : OUT STD_LOGIC;
      M_AXI_WVALID : OUT STD_LOGIC;
      M_AXI_WREADY : IN STD_LOGIC;
      M_AXI_BRESP : IN STD_LOGIC_VECTOR(1 DOWNTO 0);
      M_AXI_BID : IN STD_LOGIC_VECTOR(0 DOWNTO 0);
      M_AXI_BVALID : IN STD_LOGIC;
      M_AXI_BREADY : OUT STD_LOGIC;
      M_AXI_ARID : OUT STD_LOGIC_VECTOR(0 DOWNTO 0);
      M_AXI_ARADDR : OUT STD_LOGIC_VECTOR(31 DOWNTO 0);
      M_AXI_ARLEN : OUT STD_LOGIC_VECTOR(7 DOWNTO 0);
      M_AXI_ARSIZE : OUT STD_LOGIC_VECTOR(2 DOWNTO 0);
      M_AXI_ARBURST : OUT STD_LOGIC_VECTOR(1 DOWNTO 0);
      M_AXI_ARLOCK : OUT STD_LOGIC;
      M_AXI_ARCACHE : OUT STD_LOGIC_VECTOR(3 DOWNTO 0);
      M_AXI_ARPROT : OUT STD_LOGIC_VECTOR(2 DOWNTO 0);
      M_AXI_ARQOS : OUT STD_LOGIC_VECTOR(3 DOWNTO 0);
      M_AXI_ARVALID : OUT STD_LOGIC;
      M_AXI_ARREADY : IN STD_LOGIC;
      M_AXI_RID : IN STD_LOGIC_VECTOR(0 DOWNTO 0);
      M_AXI_RDATA : IN STD_LOGIC_VECTOR(31 DOWNTO 0);
      M_AXI_RRESP : IN STD_LOGIC_VECTOR(1 DOWNTO 0);
      M_AXI_RLAST : IN STD_LOGIC;
      M_AXI_RVALID : IN STD_LOGIC;
      M_AXI_RREADY : OUT STD_LOGIC;
      LMB_Data_Addr_0 : OUT STD_LOGIC_VECTOR(0 TO 31);
      LMB_Addr_Strobe_0 : OUT STD_LOGIC;
      LMB_Ready_0 : IN STD_LOGIC;
      LMB_Byte_Enable_0 : OUT STD_LOGIC_VECTOR(0 TO 3);
      LMB_Data_Read_0 : IN STD_LOGIC_VECTOR(0 TO 31);
      LMB_Data_Write_0 : OUT STD_LOGIC_VECTOR(0 TO 31);
      LMB_Read_Strobe_0 : OUT STD_LOGIC;
      LMB_Write_Strobe_0 : OUT STD_LOGIC;
      LMB_CE_0 : IN STD_LOGIC;
      LMB_UE_0 : IN STD_LOGIC;
      LMB_Wait_0 : IN STD_LOGIC;
      LMB_Data_Addr_1 : OUT STD_LOGIC_VECTOR(0 TO 31);
      LMB_Addr_Strobe_1 : OUT STD_LOGIC;
      LMB_Ready_1 : IN STD_LOGIC;
      LMB_Byte_Enable_1 : OUT STD_LOGIC_VECTOR(0 TO 3);
      LMB_Data_Read_1 : IN STD_LOGIC_VECTOR(0 TO 31);
      LMB_Data_Write_1 : OUT STD_LOGIC_VECTOR(0 TO 31);
      LMB_Read_Strobe_1 : OUT STD_LOGIC;
      LMB_Write_Strobe_1 : OUT STD_LOGIC;
      LMB_CE_1 : IN STD_LOGIC;
      LMB_UE_1 : IN STD_LOGIC;
      LMB_Wait_1 : IN STD_LOGIC;
      LMB_Data_Addr_2 : OUT STD_LOGIC_VECTOR(0 TO 31);
      LMB_Addr_Strobe_2 : OUT STD_LOGIC;
      LMB_Ready_2 : IN STD_LOGIC;
      LMB_Byte_Enable_2 : OUT STD_LOGIC_VECTOR(0 TO 3);
      LMB_Data_Read_2 : IN STD_LOGIC_VECTOR(0 TO 31);
      LMB_Data_Write_2 : OUT STD_LOGIC_VECTOR(0 TO 31);
      LMB_Read_Strobe_2 : OUT STD_LOGIC;
      LMB_Write_Strobe_2 : OUT STD_LOGIC;
      LMB_CE_2 : IN STD_LOGIC;
      LMB_UE_2 : IN STD_LOGIC;
      LMB_Wait_2 : IN STD_LOGIC;
      LMB_Data_Addr_3 : OUT STD_LOGIC_VECTOR(0 TO 31);
      LMB_Addr_Strobe_3 : OUT STD_LOGIC;
      LMB_Ready_3 : IN STD_LOGIC;
      LMB_Byte_Enable_3 : OUT STD_LOGIC_VECTOR(0 TO 3);
      LMB_Data_Read_3 : IN STD_LOGIC_VECTOR(0 TO 31);
      LMB_Data_Write_3 : OUT STD_LOGIC_VECTOR(0 TO 31);
      LMB_Read_Strobe_3 : OUT STD_LOGIC;
      LMB_Write_Strobe_3 : OUT STD_LOGIC;
      LMB_CE_3 : IN STD_LOGIC;
      LMB_UE_3 : IN STD_LOGIC;
      LMB_Wait_3 : IN STD_LOGIC;
      LMB_Data_Addr_4 : OUT STD_LOGIC_VECTOR(0 TO 31);
      LMB_Addr_Strobe_4 : OUT STD_LOGIC;
      LMB_Ready_4 : IN STD_LOGIC;
      LMB_Byte_Enable_4 : OUT STD_LOGIC_VECTOR(0 TO 3);
      LMB_Data_Read_4 : IN STD_LOGIC_VECTOR(0 TO 31);
      LMB_Data_Write_4 : OUT STD_LOGIC_VECTOR(0 TO 31);
      LMB_Read_Strobe_4 : OUT STD_LOGIC;
      LMB_Write_Strobe_4 : OUT STD_LOGIC;
      LMB_CE_4 : IN STD_LOGIC;
      LMB_UE_4 : IN STD_LOGIC;
      LMB_Wait_4 : IN STD_LOGIC;
      LMB_Data_Addr_5 : OUT STD_LOGIC_VECTOR(0 TO 31);
      LMB_Addr_Strobe_5 : OUT STD_LOGIC;
      LMB_Ready_5 : IN STD_LOGIC;
      LMB_Byte_Enable_5 : OUT STD_LOGIC_VECTOR(0 TO 3);
      LMB_Data_Read_5 : IN STD_LOGIC_VECTOR(0 TO 31);
      LMB_Data_Write_5 : OUT STD_LOGIC_VECTOR(0 TO 31);
      LMB_Read_Strobe_5 : OUT STD_LOGIC;
      LMB_Write_Strobe_5 : OUT STD_LOGIC;
      LMB_CE_5 : IN STD_LOGIC;
      LMB_UE_5 : IN STD_LOGIC;
      LMB_Wait_5 : IN STD_LOGIC;
      LMB_Data_Addr_6 : OUT STD_LOGIC_VECTOR(0 TO 31);
      LMB_Addr_Strobe_6 : OUT STD_LOGIC;
      LMB_Ready_6 : IN STD_LOGIC;
      LMB_Byte_Enable_6 : OUT STD_LOGIC_VECTOR(0 TO 3);
      LMB_Data_Read_6 : IN STD_LOGIC_VECTOR(0 TO 31);
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
      LMB_Data_Write_27 : OUT STD_LOGIC_VECTOR(0 TO 31);
      LMB_Read_Strobe_27 : OUT STD_LOGIC;
      LMB_Write_Strobe_27 : OUT STD_LOGIC;
      LMB_CE_27 : IN STD_LOGIC;
      LMB_UE_27 : IN STD_LOGIC;
      LMB_Wait_27 : IN STD_LOGIC;
      LMB_Data_Addr_28 : OUT STD_LOGIC_VECTOR(0 TO 31);
      LMB_Addr_Strobe_28 : OUT STD_LOGIC;
      LMB_Ready_28 : IN STD_LOGIC;
      LMB_Byte_Enable_28 : OUT STD_LOGIC_VECTOR(0 TO 3);
      LMB_Data_Read_28 : IN STD_LOGIC_VECTOR(0 TO 31);
      LMB_Data_Write_28 : OUT STD_LOGIC_VECTOR(0 TO 31);
      LMB_Read_Strobe_28 : OUT STD_LOGIC;
      LMB_Write_Strobe_28 : OUT STD_LOGIC;
      LMB_CE_28 : IN STD_LOGIC;
      LMB_UE_28 : IN STD_LOGIC;
      LMB_Wait_28 : IN STD_LOGIC;
      LMB_Data_Addr_29 : OUT STD_LOGIC_VECTOR(0 TO 31);
      LMB_Addr_Strobe_29 : OUT STD_LOGIC;
      LMB_Ready_29 : IN STD_LOGIC;
      LMB_Byte_Enable_29 : OUT STD_LOGIC_VECTOR(0 TO 3);
      LMB_Data_Read_29 : IN STD_LOGIC_VECTOR(0 TO 31);
      LMB_Data_Write_29 : OUT STD_LOGIC_VECTOR(0 TO 31);
      LMB_Read_Strobe_29 : OUT STD_LOGIC;
      LMB_Write_Strobe_29 : OUT STD_LOGIC;
      LMB_CE_29 : IN STD_LOGIC;
      LMB_UE_29 : IN STD_LOGIC;
      LMB_Wait_29 : IN STD_LOGIC;
      LMB_Data_Addr_30 : OUT STD_LOGIC_VECTOR(0 TO 31);
      LMB_Addr_Strobe_30 : OUT STD_LOGIC;
      LMB_Ready_30 : IN STD_LOGIC;
      LMB_Byte_Enable_30 : OUT STD_LOGIC_VECTOR(0 TO 3);
      LMB_Data_Read_30 : IN STD_LOGIC_VECTOR(0 TO 31);
      LMB_Data_Write_30 : OUT STD_LOGIC_VECTOR(0 TO 31);
      LMB_Read_Strobe_30 : OUT STD_LOGIC;
      LMB_Write_Strobe_30 : OUT STD_LOGIC;
      LMB_CE_30 : IN STD_LOGIC;
      LMB_UE_30 : IN STD_LOGIC;
      LMB_Wait_30 : IN STD_LOGIC;
      LMB_Data_Addr_31 : OUT STD_LOGIC_VECTOR(0 TO 31);
      LMB_Addr_Strobe_31 : OUT STD_LOGIC;
      LMB_Ready_31 : IN STD_LOGIC;
      LMB_Byte_Enable_31 : OUT STD_LOGIC_VECTOR(0 TO 3);
      LMB_Data_Read_31 : IN STD_LOGIC_VECTOR(0 TO 31);
      LMB_Data_Write_31 : OUT STD_LOGIC_VECTOR(0 TO 31);
      LMB_Read_Strobe_31 : OUT STD_LOGIC;
      LMB_Write_Strobe_31 : OUT STD_LOGIC;
      LMB_CE_31 : IN STD_LOGIC;
      LMB_UE_31 : IN STD_LOGIC;
      LMB_Wait_31 : IN STD_LOGIC;
      M_AXIS_TDATA : OUT STD_LOGIC_VECTOR(31 DOWNTO 0);
      M_AXIS_TID : OUT STD_LOGIC_VECTOR(6 DOWNTO 0);
      M_AXIS_TREADY : IN STD_LOGIC;
      M_AXIS_TVALID : OUT STD_LOGIC;
      TRACE_CLK_OUT : OUT STD_LOGIC;
      TRACE_CLK : IN STD_LOGIC;
      TRACE_CTL : OUT STD_LOGIC;
      TRACE_DATA : OUT STD_LOGIC_VECTOR(31 DOWNTO 0);
      Dbg_Clk_0 : OUT STD_LOGIC;
      Dbg_TDI_0 : OUT STD_LOGIC;
      Dbg_TDO_0 : IN STD_LOGIC;
      Dbg_Reg_En_0 : OUT STD_LOGIC_VECTOR(0 TO 7);
      Dbg_Capture_0 : OUT STD_LOGIC;
      Dbg_Shift_0 : OUT STD_LOGIC;
      Dbg_Update_0 : OUT STD_LOGIC;
      Dbg_Rst_0 : OUT STD_LOGIC;
      Dbg_Trig_In_0 : IN STD_LOGIC_VECTOR(0 TO 7);
      Dbg_Trig_Ack_In_0 : OUT STD_LOGIC_VECTOR(0 TO 7);
      Dbg_Trig_Out_0 : OUT STD_LOGIC_VECTOR(0 TO 7);
      Dbg_Trig_Ack_Out_0 : IN STD_LOGIC_VECTOR(0 TO 7);
      Dbg_TrClk_0 : OUT STD_LOGIC;
      Dbg_TrData_0 : IN STD_LOGIC_VECTOR(0 TO 35);
      Dbg_TrReady_0 : OUT STD_LOGIC;
      Dbg_TrValid_0 : IN STD_LOGIC;
      Dbg_Clk_1 : OUT STD_LOGIC;
      Dbg_TDI_1 : OUT STD_LOGIC;
      Dbg_TDO_1 : IN STD_LOGIC;
      Dbg_Reg_En_1 : OUT STD_LOGIC_VECTOR(0 TO 7);
      Dbg_Capture_1 : OUT STD_LOGIC;
      Dbg_Shift_1 : OUT STD_LOGIC;
      Dbg_Update_1 : OUT STD_LOGIC;
      Dbg_Rst_1 : OUT STD_LOGIC;
      Dbg_Trig_In_1 : IN STD_LOGIC_VECTOR(0 TO 7);
      Dbg_Trig_Ack_In_1 : OUT STD_LOGIC_VECTOR(0 TO 7);
      Dbg_Trig_Out_1 : OUT STD_LOGIC_VECTOR(0 TO 7);
      Dbg_Trig_Ack_Out_1 : IN STD_LOGIC_VECTOR(0 TO 7);
      Dbg_TrClk_1 : OUT STD_LOGIC;
      Dbg_TrData_1 : IN STD_LOGIC_VECTOR(0 TO 35);
      Dbg_TrReady_1 : OUT STD_LOGIC;
      Dbg_TrValid_1 : IN STD_LOGIC;
      Dbg_Clk_2 : OUT STD_LOGIC;
      Dbg_TDI_2 : OUT STD_LOGIC;
      Dbg_TDO_2 : IN STD_LOGIC;
      Dbg_Reg_En_2 : OUT STD_LOGIC_VECTOR(0 TO 7);
      Dbg_Capture_2 : OUT STD_LOGIC;
      Dbg_Shift_2 : OUT STD_LOGIC;
      Dbg_Update_2 : OUT STD_LOGIC;
      Dbg_Rst_2 : OUT STD_LOGIC;
      Dbg_Trig_In_2 : IN STD_LOGIC_VECTOR(0 TO 7);
      Dbg_Trig_Ack_In_2 : OUT STD_LOGIC_VECTOR(0 TO 7);
      Dbg_Trig_Out_2 : OUT STD_LOGIC_VECTOR(0 TO 7);
      Dbg_Trig_Ack_Out_2 : IN STD_LOGIC_VECTOR(0 TO 7);
      Dbg_TrClk_2 : OUT STD_LOGIC;
      Dbg_TrData_2 : IN STD_LOGIC_VECTOR(0 TO 35);
      Dbg_TrReady_2 : OUT STD_LOGIC;
      Dbg_TrValid_2 : IN STD_LOGIC;
      Dbg_Clk_3 : OUT STD_LOGIC;
      Dbg_TDI_3 : OUT STD_LOGIC;
      Dbg_TDO_3 : IN STD_LOGIC;
      Dbg_Reg_En_3 : OUT STD_LOGIC_VECTOR(0 TO 7);
      Dbg_Capture_3 : OUT STD_LOGIC;
      Dbg_Shift_3 : OUT STD_LOGIC;
      Dbg_Update_3 : OUT STD_LOGIC;
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
      Dbg_TDO_27 : IN STD_LOGIC;
      Dbg_Reg_En_27 : OUT STD_LOGIC_VECTOR(0 TO 7);
      Dbg_Capture_27 : OUT STD_LOGIC;
      Dbg_Shift_27 : OUT STD_LOGIC;
      Dbg_Update_27 : OUT STD_LOGIC;
      Dbg_Rst_27 : OUT STD_LOGIC;
      Dbg_Trig_In_27 : IN STD_LOGIC_VECTOR(0 TO 7);
      Dbg_Trig_Ack_In_27 : OUT STD_LOGIC_VECTOR(0 TO 7);
      Dbg_Trig_Out_27 : OUT STD_LOGIC_VECTOR(0 TO 7);
      Dbg_Trig_Ack_Out_27 : IN STD_LOGIC_VECTOR(0 TO 7);
      Dbg_TrClk_27 : OUT STD_LOGIC;
      Dbg_TrData_27 : IN STD_LOGIC_VECTOR(0 TO 35);
      Dbg_TrReady_27 : OUT STD_LOGIC;
      Dbg_TrValid_27 : IN STD_LOGIC;
      Dbg_Clk_28 : OUT STD_LOGIC;
      Dbg_TDI_28 : OUT STD_LOGIC;
      Dbg_TDO_28 : IN STD_LOGIC;
      Dbg_Reg_En_28 : OUT STD_LOGIC_VECTOR(0 TO 7);
      Dbg_Capture_28 : OUT STD_LOGIC;
      Dbg_Shift_28 : OUT STD_LOGIC;
      Dbg_Update_28 : OUT STD_LOGIC;
      Dbg_Rst_28 : OUT STD_LOGIC;
      Dbg_Trig_In_28 : IN STD_LOGIC_VECTOR(0 TO 7);
      Dbg_Trig_Ack_In_28 : OUT STD_LOGIC_VECTOR(0 TO 7);
      Dbg_Trig_Out_28 : OUT STD_LOGIC_VECTOR(0 TO 7);
      Dbg_Trig_Ack_Out_28 : IN STD_LOGIC_VECTOR(0 TO 7);
      Dbg_TrClk_28 : OUT STD_LOGIC;
      Dbg_TrData_28 : IN STD_LOGIC_VECTOR(0 TO 35);
      Dbg_TrReady_28 : OUT STD_LOGIC;
      Dbg_TrValid_28 : IN STD_LOGIC;
      Dbg_Clk_29 : OUT STD_LOGIC;
      Dbg_TDI_29 : OUT STD_LOGIC;
      Dbg_TDO_29 : IN STD_LOGIC;
      Dbg_Reg_En_29 : OUT STD_LOGIC_VECTOR(0 TO 7);
      Dbg_Capture_29 : OUT STD_LOGIC;
      Dbg_Shift_29 : OUT STD_LOGIC;
      Dbg_Update_29 : OUT STD_LOGIC;
      Dbg_Rst_29 : OUT STD_LOGIC;
      Dbg_Trig_In_29 : IN STD_LOGIC_VECTOR(0 TO 7);
      Dbg_Trig_Ack_In_29 : OUT STD_LOGIC_VECTOR(0 TO 7);
      Dbg_Trig_Out_29 : OUT STD_LOGIC_VECTOR(0 TO 7);
      Dbg_Trig_Ack_Out_29 : IN STD_LOGIC_VECTOR(0 TO 7);
      Dbg_TrClk_29 : OUT STD_LOGIC;
      Dbg_TrData_29 : IN STD_LOGIC_VECTOR(0 TO 35);
      Dbg_TrReady_29 : OUT STD_LOGIC;
      Dbg_TrValid_29 : IN STD_LOGIC;
      Dbg_Clk_30 : OUT STD_LOGIC;
      Dbg_TDI_30 : OUT STD_LOGIC;
      Dbg_TDO_30 : IN STD_LOGIC;
      Dbg_Reg_En_30 : OUT STD_LOGIC_VECTOR(0 TO 7);
      Dbg_Capture_30 : OUT STD_LOGIC;
      Dbg_Shift_30 : OUT STD_LOGIC;
      Dbg_Update_30 : OUT STD_LOGIC;
      Dbg_Rst_30 : OUT STD_LOGIC;
      Dbg_Trig_In_30 : IN STD_LOGIC_VECTOR(0 TO 7);
      Dbg_Trig_Ack_In_30 : OUT STD_LOGIC_VECTOR(0 TO 7);
      Dbg_Trig_Out_30 : OUT STD_LOGIC_VECTOR(0 TO 7);
      Dbg_Trig_Ack_Out_30 : IN STD_LOGIC_VECTOR(0 TO 7);
      Dbg_TrClk_30 : OUT STD_LOGIC;
      Dbg_TrData_30 : IN STD_LOGIC_VECTOR(0 TO 35);
      Dbg_TrReady_30 : OUT STD_LOGIC;
      Dbg_TrValid_30 : IN STD_LOGIC;
      Dbg_Clk_31 : OUT STD_LOGIC;
      Dbg_TDI_31 : OUT STD_LOGIC;
      Dbg_TDO_31 : IN STD_LOGIC;
      Dbg_Reg_En_31 : OUT STD_LOGIC_VECTOR(0 TO 7);
      Dbg_Capture_31 : OUT STD_LOGIC;
      Dbg_Shift_31 : OUT STD_LOGIC;
      Dbg_Update_31 : OUT STD_LOGIC;
      Dbg_Rst_31 : OUT STD_LOGIC;
      Dbg_Trig_In_31 : IN STD_LOGIC_VECTOR(0 TO 7);
      Dbg_Trig_Ack_In_31 : OUT STD_LOGIC_VECTOR(0 TO 7);
      Dbg_Trig_Out_31 : OUT STD_LOGIC_VECTOR(0 TO 7);
      Dbg_Trig_Ack_Out_31 : IN STD_LOGIC_VECTOR(0 TO 7);
      Dbg_TrClk_31 : OUT STD_LOGIC;
      Dbg_TrData_31 : IN STD_LOGIC_VECTOR(0 TO 35);
      Dbg_TrReady_31 : OUT STD_LOGIC;
      Dbg_TrValid_31 : IN STD_LOGIC;
      bscan_ext_tdi : IN STD_LOGIC;
      bscan_ext_reset : IN STD_LOGIC;
      bscan_ext_shift : IN STD_LOGIC;
      bscan_ext_update : IN STD_LOGIC;
      bscan_ext_capture : IN STD_LOGIC;
      bscan_ext_sel : IN STD_LOGIC;
      bscan_ext_drck : IN STD_LOGIC;
      bscan_ext_tdo : OUT STD_LOGIC;
      Ext_JTAG_DRCK : OUT STD_LOGIC;
      Ext_JTAG_RESET : OUT STD_LOGIC;
      Ext_JTAG_SEL : OUT STD_LOGIC;
      Ext_JTAG_CAPTURE : OUT STD_LOGIC;
      Ext_JTAG_SHIFT : OUT STD_LOGIC;
      Ext_JTAG_UPDATE : OUT STD_LOGIC;
      Ext_JTAG_TDI : OUT STD_LOGIC;
      Ext_JTAG_TDO : IN STD_LOGIC
    );
  END COMPONENT MDM;
  ATTRIBUTE X_CORE_INFO : STRING;
  ATTRIBUTE X_CORE_INFO OF design_1_mdm_1_0_arch: ARCHITECTURE IS "MDM,Vivado 2015.2";
  ATTRIBUTE CHECK_LICENSE_TYPE : STRING;
  ATTRIBUTE CHECK_LICENSE_TYPE OF design_1_mdm_1_0_arch : ARCHITECTURE IS "design_1_mdm_1_0,MDM,{}";
  ATTRIBUTE CORE_GENERATION_INFO : STRING;
  ATTRIBUTE CORE_GENERATION_INFO OF design_1_mdm_1_0_arch: ARCHITECTURE IS "design_1_mdm_1_0,MDM,{x_ipProduct=Vivado 2015.2,x_ipVendor=xilinx.com,x_ipLibrary=ip,x_ipName=mdm,x_ipVersion=3.2,x_ipCoreRevision=3,x_ipLanguage=VHDL,x_ipSimLanguage=MIXED,C_FAMILY=artix7,C_JTAG_CHAIN=2,C_USE_BSCAN=0,C_USE_CONFIG_RESET=0,C_INTERCONNECT=2,C_MB_DBG_PORTS=1,C_USE_UART=0,C_DBG_REG_ACCESS=0,C_DBG_MEM_ACCESS=0,C_USE_CROSS_TRIGGER=0,C_TRACE_OUTPUT=0,C_TRACE_DATA_WIDTH=32,C_TRACE_CLK_FREQ_HZ=200000000,C_TRACE_CLK_OUT_PHASE=90,C_S_AXI_ADDR_WIDTH=32,C_S_AXI_DATA_WIDTH=32,C_S_AXI_ACLK_FREQ_HZ=100000000,C_M_AXI_ADDR_WIDTH=32,C_M_AXI_DATA_WIDTH=32,C_M_AXI_THREAD_ID_WIDTH=1,C_DATA_SIZE=32,C_M_AXIS_DATA_WIDTH=32,C_M_AXIS_ID_WIDTH=7}";
  ATTRIBUTE X_INTERFACE_INFO : STRING;
  ATTRIBUTE X_INTERFACE_INFO OF Debug_SYS_Rst: SIGNAL IS "xilinx.com:signal:reset:1.0 RST.Debug_SYS_Rst RST";
  ATTRIBUTE X_INTERFACE_INFO OF Dbg_Clk_0: SIGNAL IS "xilinx.com:interface:mbdebug:3.0 MBDEBUG_0 CLK";
  ATTRIBUTE X_INTERFACE_INFO OF Dbg_TDI_0: SIGNAL IS "xilinx.com:interface:mbdebug:3.0 MBDEBUG_0 TDI";
  ATTRIBUTE X_INTERFACE_INFO OF Dbg_TDO_0: SIGNAL IS "xilinx.com:interface:mbdebug:3.0 MBDEBUG_0 TDO";
  ATTRIBUTE X_INTERFACE_INFO OF Dbg_Reg_En_0: SIGNAL IS "xilinx.com:interface:mbdebug:3.0 MBDEBUG_0 REG_EN";
  ATTRIBUTE X_INTERFACE_INFO OF Dbg_Capture_0: SIGNAL IS "xilinx.com:interface:mbdebug:3.0 MBDEBUG_0 CAPTURE";
  ATTRIBUTE X_INTERFACE_INFO OF Dbg_Shift_0: SIGNAL IS "xilinx.com:interface:mbdebug:3.0 MBDEBUG_0 SHIFT";
  ATTRIBUTE X_INTERFACE_INFO OF Dbg_Update_0: SIGNAL IS "xilinx.com:interface:mbdebug:3.0 MBDEBUG_0 UPDATE";
  ATTRIBUTE X_INTERFACE_INFO OF Dbg_Rst_0: SIGNAL IS "xilinx.com:interface:mbdebug:3.0 MBDEBUG_0 RST";
BEGIN
  U0 : MDM
    GENERIC MAP (
      C_FAMILY => "artix7",
      C_JTAG_CHAIN => 2,
      C_USE_BSCAN => 0,
      C_USE_CONFIG_RESET => 0,
      C_INTERCONNECT => 2,
      C_MB_DBG_PORTS => 1,
      C_USE_UART => 0,
      C_DBG_REG_ACCESS => 0,
      C_DBG_MEM_ACCESS => 0,
      C_USE_CROSS_TRIGGER => 0,
      C_TRACE_OUTPUT => 0,
      C_TRACE_DATA_WIDTH => 32,
      C_TRACE_CLK_FREQ_HZ => 200000000,
      C_TRACE_CLK_OUT_PHASE => 90,
      C_S_AXI_ADDR_WIDTH => 32,
      C_S_AXI_DATA_WIDTH => 32,
      C_S_AXI_ACLK_FREQ_HZ => 100000000,
      C_M_AXI_ADDR_WIDTH => 32,
      C_M_AXI_DATA_WIDTH => 32,
      C_M_AXI_THREAD_ID_WIDTH => 1,
      C_DATA_SIZE => 32,
      C_M_AXIS_DATA_WIDTH => 32,
      C_M_AXIS_ID_WIDTH => 7
    )
    PORT MAP (
      Config_Reset => '0',
      Scan_Reset => '0',
      Scan_Reset_Sel => '0',
      S_AXI_ACLK => '0',
      S_AXI_ARESETN => '0',
      M_AXI_ACLK => '0',
      M_AXI_ARESETN => '0',
      M_AXIS_ACLK => '0',
      M_AXIS_ARESETN => '0',
      Debug_SYS_Rst => Debug_SYS_Rst,
      Trig_In_0 => '0',
      Trig_Ack_Out_0 => '0',
      Trig_In_1 => '0',
      Trig_Ack_Out_1 => '0',
      Trig_In_2 => '0',
      Trig_Ack_Out_2 => '0',
      Trig_In_3 => '0',
      Trig_Ack_Out_3 => '0',
      S_AXI_AWADDR => STD_LOGIC_VECTOR(TO_UNSIGNED(0, 32)),
      S_AXI_AWVALID => '0',
      S_AXI_WDATA => STD_LOGIC_VECTOR(TO_UNSIGNED(0, 32)),
      S_AXI_WSTRB => STD_LOGIC_VECTOR(TO_UNSIGNED(0, 4)),
      S_AXI_WVALID => '0',
      S_AXI_BREADY => '0',
      S_AXI_ARADDR => STD_LOGIC_VECTOR(TO_UNSIGNED(0, 32)),
      S_AXI_ARVALID => '0',
      S_AXI_RREADY => '0',
      M_AXI_AWREADY => '0',
      M_AXI_WREADY => '0',
      M_AXI_BRESP => STD_LOGIC_VECTOR(TO_UNSIGNED(0, 2)),
      M_AXI_BID => STD_LOGIC_VECTOR(TO_UNSIGNED(0, 1)),
      M_AXI_BVALID => '0',
      M_AXI_ARREADY => '0',
      M_AXI_RID => STD_LOGIC_VECTOR(TO_UNSIGNED(0, 1)),
      M_AXI_RDATA => STD_LOGIC_VECTOR(TO_UNSIGNED(0, 32)),
      M_AXI_RRESP => STD_LOGIC_VECTOR(TO_UNSIGNED(0, 2)),
      M_AXI_RLAST => '0',
      M_AXI_RVALID => '0',
      LMB_Ready_0 => '0',
      LMB_Data_Read_0 => STD_LOGIC_VECTOR(TO_UNSIGNED(0, 32)),
      LMB_CE_0 => '0',
      LMB_UE_0 => '0',
      LMB_Wait_0 => '0',
      LMB_Ready_1 => '0',
      LMB_Data_Read_1 => STD_LOGIC_VECTOR(TO_UNSIGNED(0, 32)),
      LMB_CE_1 => '0',
      LMB_UE_1 => '0',
      LMB_Wait_1 => '0',
      LMB_Ready_2 => '0',
      LMB_Data_Read_2 => STD_LOGIC_VECTOR(TO_UNSIGNED(0, 32)),
      LMB_CE_2 => '0',
      LMB_UE_2 => '0',
      LMB_Wait_2 => '0',
      LMB_Ready_3 => '0',
      LMB_Data_Read_3 => STD_LOGIC_VECTOR(TO_UNSIGNED(0, 32)),
      LMB_CE_3 => '0',
      LMB_UE_3 => '0',
      LMB_Wait_3 => '0',
      LMB_Ready_4 => '0',
      LMB_Data_Read_4 => STD_LOGIC_VECTOR(TO_UNSIGNED(0, 32)),
      LMB_CE_4 => '0',
      LMB_UE_4 => '0',
      LMB_Wait_4 => '0',
      LMB_Ready_5 => '0',
      LMB_Data_Read_5 => STD_LOGIC_VECTOR(TO_UNSIGNED(0, 32)),
      LMB_CE_5 => '0',
      LMB_UE_5 => '0',
      LMB_Wait_5 => '0',
      LMB_Ready_6 => '0',
      LMB_Data_Read_6 => STD_LOGIC_VECTOR(TO_UNSIGNED(0, 32)),
      LMB_CE_6 => '0',
      LMB_UE_6 => '0',
      LMB_Wait_6 => '0',
      LMB_Ready_7 => '0',
      LMB_Data_Read_7 => STD_LOGIC_VECTOR(TO_UNSIGNED(0, 32)),
      LMB_CE_7 => '0',
      LMB_UE_7 => '0',
      LMB_Wait_7 => '0',
      LMB_Ready_8 => '0',
      LMB_Data_Read_8 => STD_LOGIC_VECTOR(TO_UNSIGNED(0, 32)),
      LMB_CE_8 => '0',
      LMB_UE_8 => '0',
      LMB_Wait_8 => '0',
      LMB_Ready_9 => '0',
      LMB_Data_Read_9 => STD_LOGIC_VECTOR(TO_UNSIGNED(0, 32)),
      LMB_CE_9 => '0',
      LMB_UE_9 => '0',
      LMB_Wait_9 => '0',
      LMB_Ready_10 => '0',
      LMB_Data_Read_10 => STD_LOGIC_VECTOR(TO_UNSIGNED(0, 32)),
      LMB_CE_10 => '0',
      LMB_UE_10 => '0',
      LMB_Wait_10 => '0',
      LMB_Ready_11 => '0',
      LMB_Data_Read_11 => STD_LOGIC_VECTOR(TO_UNSIGNED(0, 32)),
      LMB_CE_11 => '0',
      LMB_UE_11 => '0',
      LMB_Wait_11 => '0',
      LMB_Ready_12 => '0',
      LMB_Data_Read_12 => STD_LOGIC_VECTOR(TO_UNSIGNED(0, 32)),
      LMB_CE_12 => '0',
      LMB_UE_12 => '0',
      LMB_Wait_12 => '0',
      LMB_Ready_13 => '0',
      LMB_Data_Read_13 => STD_LOGIC_VECTOR(TO_UNSIGNED(0, 32)),
      LMB_CE_13 => '0',
      LMB_UE_13 => '0',
      LMB_Wait_13 => '0',
      LMB_Ready_14 => '0',
      LMB_Data_Read_14 => STD_LOGIC_VECTOR(TO_UNSIGNED(0, 32)),
      LMB_CE_14 => '0',
      LMB_UE_14 => '0',
      LMB_Wait_14 => '0',
      LMB_Ready_15 => '0',
      LMB_Data_Read_15 => STD_LOGIC_VECTOR(TO_UNSIGNED(0, 32)),
      LMB_CE_15 => '0',
      LMB_UE_15 => '0',
      LMB_Wait_15 => '0',
      LMB_Ready_16 => '0',
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
      Dbg_Trig_Ack_Out_30 => STD_LOGIC_VECTOR(TO_UNSIGNED(0, 8)),
      Dbg_TrData_30 => STD_LOGIC_VECTOR(TO_UNSIGNED(0, 36)),
      Dbg_TrValid_30 => '0',
      Dbg_TDO_31 => '0',
      Dbg_Trig_In_31 => STD_LOGIC_VECTOR(TO_UNSIGNED(0, 8)),
      Dbg_Trig_Ack_Out_31 => STD_LOGIC_VECTOR(TO_UNSIGNED(0, 8)),
      Dbg_TrData_31 => STD_LOGIC_VECTOR(TO_UNSIGNED(0, 36)),
      Dbg_TrValid_31 => '0',
      bscan_ext_tdi => '0',
      bscan_ext_reset => '0',
      bscan_ext_shift => '0',
      bscan_ext_update => '0',
      bscan_ext_capture => '0',
      bscan_ext_sel => '0',
      bscan_ext_drck => '0',
      Ext_JTAG_TDO => '0'
    );
END design_1_mdm_1_0_arch;
