AlistairCheeseman/WindTunnelApparatus/Firmware/Tests/FPGA/FPGAEchoExample/GSMBS2015.2.srcs/sources_1/bd/design_1/ip/design_1_xbar_1/synth/design_1_xbar_1.v

// (c) Copyright 1995-2015 Xilinx, Inc. All rights reserved.
// 
// This file contains confidential and proprietary information
// of Xilinx, Inc. and is protected under U.S. and
// international copyright and other intellectual property
// laws.
// 
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
// CRITICAL APPLICATIONS
// Xilinx products are not designed or intended to be fail-
// safe, or for use in any application requiring fail-safe
// performance, such as life-support or safety devices or
// systems, Class III medical devices, nuclear facilities,
// applications related to the deployment of airbags, or any
// other applications that could lead to death, personal
// injury, or severe property or environmental damage
// (individually and collectively, "Critical
// Applications"). Customer assumes the sole risk and
// liability of any use of Xilinx products in Critical
// Applications, subject only to applicable laws and
// regulations governing limitations on product liability.
// 
// THIS COPYRIGHT NOTICE AND DISCLAIMER MUST BE RETAINED AS
// PART OF THIS FILE AT ALL TIMES.
// 
// DO NOT MODIFY THIS FILE.


// IP VLNV: xilinx.com:ip:axi_crossbar:2.1
// IP Revision: 6

(* X_CORE_INFO = "axi_crossbar_v2_1_axi_crossbar,Vivado 2015.2" *)
(* CHECK_LICENSE_TYPE = "design_1_xbar_1,axi_crossbar_v2_1_axi_crossbar,{}" *)
(* CORE_GENERATION_INFO = "design_1_xbar_1,axi_crossbar_v2_1_axi_crossbar,{x_ipProduct=Vivado 2015.2,x_ipVendor=xilinx.com,x_ipLibrary=ip,x_ipName=axi_crossbar,x_ipVersion=2.1,x_ipCoreRevision=6,x_ipLanguage=VHDL,x_ipSimLanguage=MIXED,C_FAMILY=artix7,C_NUM_SLAVE_SLOTS=1,C_NUM_MASTER_SLOTS=4,C_AXI_ID_WIDTH=1,C_AXI_ADDR_WIDTH=32,C_AXI_DATA_WIDTH=32,C_AXI_PROTOCOL=2,C_NUM_ADDR_RANGES=1,C_M_AXI_BASE_ADDR=0x0000000041c000000000000040e0000000000000406000000000000041200000,C_M_AXI_ADDR_WIDTH=0x00000010000000100000001000000010,C_S_AXI_BASE_ID=0x00000000,C_S_AXI_THREAD_ID_WIDTH=0x00000000,C_AXI_SUPPORTS_USER_SIGNALS=0,C_AXI_AWUSER_WIDTH=1,C_AXI_ARUSER_WIDTH=1,C_AXI_WUSER_WIDTH=1,C_AXI_RUSER_WIDTH=1,C_AXI_BUSER_WIDTH=1,C_M_AXI_WRITE_CONNECTIVITY=0x00000001000000010000000100000001,C_M_AXI_READ_CONNECTIVITY=0x00000001000000010000000100000001,C_R_REGISTER=1,C_S_AXI_SINGLE_THREAD=0x00000001,C_S_AXI_WRITE_ACCEPTANCE=0x00000001,C_S_AXI_READ_ACCEPTANCE=0x00000001,C_M_AXI_WRITE_ISSUING=0x00000001000000010000000100000001,C_M_AXI_READ_ISSUING=0x00000001000000010000000100000001,C_S_AXI_ARB_PRIORITY=0x00000000,C_M_AXI_SECURE=0x00000000000000000000000000000000,C_CONNECTIVITY_MODE=0}" *)
(* DowngradeIPIdentifiedWarnings = "yes" *)
module design_1_xbar_1 (
  aclk,
  aresetn,
  s_axi_awaddr,
  s_axi_awprot,
  s_axi_awvalid,
  s_axi_awready,
  s_axi_wdata,
  s_axi_wstrb,
  s_axi_wvalid,
  s_axi_wready,
  s_axi_bresp,
  s_axi_bvalid,
  s_axi_bready,
  s_axi_araddr,
  s_axi_arprot,
  s_axi_arvalid,
  s_axi_arready,
  s_axi_rdata,
  s_axi_rresp,
  s_axi_rvalid,
  s_axi_rready,
  m_axi_awaddr,
  m_axi_awprot,
  m_axi_awvalid,
  m_axi_awready,
  m_axi_wdata,
  m_axi_wstrb,
  m_axi_wvalid,
  m_axi_wready,
  m_axi_bresp,
  m_axi_bvalid,
  m_axi_bready,
  m_axi_araddr,
  m_axi_arprot,
  m_axi_arvalid,
  m_axi_arready,
  m_axi_rdata,
  m_axi_rresp,
  m_axi_rvalid,
  m_axi_rready
);

(* X_INTERFACE_INFO = "xilinx.com:signal:clock:1.0 CLKIF CLK" *)
input wire aclk;
(* X_INTERFACE_INFO = "xilinx.com:signal:reset:1.0 RSTIF RST" *)
input wire aresetn;
(* X_INTERFACE_INFO = "xilinx.com:interface:aximm:1.0 S00_AXI AWADDR" *)
input wire [31 : 0] s_axi_awaddr;
(* X_INTERFACE_INFO = "xilinx.com:interface:aximm:1.0 S00_AXI AWPROT" *)
input wire [2 : 0] s_axi_awprot;
(* X_INTERFACE_INFO = "xilinx.com:interface:aximm:1.0 S00_AXI AWVALID" *)
input wire [0 : 0] s_axi_awvalid;
(* X_INTERFACE_INFO = "xilinx.com:interface:aximm:1.0 S00_AXI AWREADY" *)
output wire [0 : 0] s_axi_awready;
(* X_INTERFACE_INFO = "xilinx.com:interface:aximm:1.0 S00_AXI WDATA" *)
input wire [31 : 0] s_axi_wdata;
(* X_INTERFACE_INFO = "xilinx.com:interface:aximm:1.0 S00_AXI WSTRB" *)
input wire [3 : 0] s_axi_wstrb;
(* X_INTERFACE_INFO = "xilinx.com:interface:aximm:1.0 S00_AXI WVALID" *)
input wire [0 : 0] s_axi_wvalid;
(* X_INTERFACE_INFO = "xilinx.com:interface:aximm:1.0 S00_AXI WREADY" *)
output wire [0 : 0] s_axi_wready;
(* X_INTERFACE_INFO = "xilinx.com:interface:aximm:1.0 S00_AXI BRESP" *)
output wire [1 : 0] s_axi_bresp;
(* X_INTERFACE_INFO = "xilinx.com:interface:aximm:1.0 S00_AXI BVALID" *)
output wire [0 : 0] s_axi_bvalid;
(* X_INTERFACE_INFO = "xilinx.com:interface:aximm:1.0 S00_AXI BREADY" *)
input wire [0 : 0] s_axi_bready;
(* X_INTERFACE_INFO = "xilinx.com:interface:aximm:1.0 S00_AXI ARADDR" *)
input wire [31 : 0] s_axi_araddr;
(* X_INTERFACE_INFO = "xilinx.com:interface:aximm:1.0 S00_AXI ARPROT" *)
input wire [2 : 0] s_axi_arprot;
(* X_INTERFACE_INFO = "xilinx.com:interface:aximm:1.0 S00_AXI ARVALID" *)
input wire [0 : 0] s_axi_arvalid;
(* X_INTERFACE_INFO = "xilinx.com:interface:aximm:1.0 S00_AXI ARREADY" *)
output wire [0 : 0] s_axi_arready;
(* X_INTERFACE_INFO = "xilinx.com:interface:aximm:1.0 S00_AXI RDATA" *)
output wire [31 : 0] s_axi_rdata;
(* X_INTERFACE_INFO = "xilinx.com:interface:aximm:1.0 S00_AXI RRESP" *)
output wire [1 : 0] s_axi_rresp;
(* X_INTERFACE_INFO = "xilinx.com:interface:aximm:1.0 S00_AXI RVALID" *)
output wire [0 : 0] s_axi_rvalid;
(* X_INTERFACE_INFO = "xilinx.com:interface:aximm:1.0 S00_AXI RREADY" *)
input wire [0 : 0] s_axi_rready;
(* X_INTERFACE_INFO = "xilinx.com:interface:aximm:1.0 M00_AXI AWADDR [31:0] [31:0], xilinx.com:interface:aximm:1.0 M01_AXI AWADDR [31:0] [63:32], xilinx.com:interface:aximm:1.0 M02_AXI AWADDR [31:0] [95:64], xilinx.com:interface:aximm:1.0 M03_AXI AWADDR [31:0] [127:96]" *)
output wire [127 : 0] m_axi_awaddr;
(* X_INTERFACE_INFO = "xilinx.com:interface:aximm:1.0 M00_AXI AWPROT [2:0] [2:0], xilinx.com:interface:aximm:1.0 M01_AXI AWPROT [2:0] [5:3], xilinx.com:interface:aximm:1.0 M02_AXI AWPROT [2:0] [8:6], xilinx.com:interface:aximm:1.0 M03_AXI AWPROT [2:0] [11:9]" *)
output wire [11 : 0] m_axi_awprot;
(* X_INTERFACE_INFO = "xilinx.com:interface:aximm:1.0 M00_AXI AWVALID [0:0] [0:0], xilinx.com:interface:aximm:1.0 M01_AXI AWVALID [0:0] [1:1], xilinx.com:interface:aximm:1.0 M02_AXI AWVALID [0:0] [2:2], xilinx.com:interface:aximm:1.0 M03_AXI AWVALID [0:0] [3:3]" *)
output wire [3 : 0] m_axi_awvalid;
(* X_INTERFACE_INFO = "xilinx.com:interface:aximm:1.0 M00_AXI AWREADY [0:0] [0:0], xilinx.com:interface:aximm:1.0 M01_AXI AWREADY [0:0] [1:1], xilinx.com:interface:aximm:1.0 M02_AXI AWREADY [0:0] [2:2], xilinx.com:interface:aximm:1.0 M03_AXI AWREADY [0:0] [3:3]" *)
input wire [3 : 0] m_axi_awready;
(* X_INTERFACE_INFO = "xilinx.com:interface:aximm:1.0 M00_AXI WDATA [31:0] [31:0], xilinx.com:interface:aximm:1.0 M01_AXI WDATA [31:0] [63:32], xilinx.com:interface:aximm:1.0 M02_AXI WDATA [31:0] [95:64], xilinx.com:interface:aximm:1.0 M03_AXI WDATA [31:0] [127:96]" *)
output wire [127 : 0] m_axi_wdata;
(* X_INTERFACE_INFO = "xilinx.com:interface:aximm:1.0 M00_AXI WSTRB [3:0] [3:0], xilinx.com:interface:aximm:1.0 M01_AXI WSTRB [3:0] [7:4], xilinx.com:interface:aximm:1.0 M02_AXI WSTRB [3:0] [11:8], xilinx.com:interface:aximm:1.0 M03_AXI WSTRB [3:0] [15:12]" *)
output wire [15 : 0] m_axi_wstrb;
(* X_INTERFACE_INFO = "xilinx.com:interface:aximm:1.0 M00_AXI WVALID [0:0] [0:0], xilinx.com:interface:aximm:1.0 M01_AXI WVALID [0:0] [1:1], xilinx.com:interface:aximm:1.0 M02_AXI WVALID [0:0] [2:2], xilinx.com:interface:aximm:1.0 M03_AXI WVALID [0:0] [3:3]" *)
output wire [3 : 0] m_axi_wvalid;
(* X_INTERFACE_INFO = "xilinx.com:interface:aximm:1.0 M00_AXI WREADY [0:0] [0:0], xilinx.com:interface:aximm:1.0 M01_AXI WREADY [0:0] [1:1], xilinx.com:interface:aximm:1.0 M02_AXI WREADY [0:0] [2:2], xilinx.com:interface:aximm:1.0 M03_AXI WREADY [0:0] [3:3]" *)
input wire [3 : 0] m_axi_wready;
(* X_INTERFACE_INFO = "xilinx.com:interface:aximm:1.0 M00_AXI BRESP [1:0] [1:0], xilinx.com:interface:aximm:1.0 M01_AXI BRESP [1:0] [3:2], xilinx.com:interface:aximm:1.0 M02_AXI BRESP [1:0] [5:4], xilinx.com:interface:aximm:1.0 M03_AXI BRESP [1:0] [7:6]" *)
input wire [7 : 0] m_axi_bresp;
(* X_INTERFACE_INFO = "xilinx.com:interface:aximm:1.0 M00_AXI BVALID [0:0] [0:0], xilinx.com:interface:aximm:1.0 M01_AXI BVALID [0:0] [1:1], xilinx.com:interface:aximm:1.0 M02_AXI BVALID [0:0] [2:2], xilinx.com:interface:aximm:1.0 M03_AXI BVALID [0:0] [3:3]" *)
input wire [3 : 0] m_axi_bvalid;
(* X_INTERFACE_INFO = "xilinx.com:interface:aximm:1.0 M00_AXI BREADY [0:0] [0:0], xilinx.com:interface:aximm:1.0 M01_AXI BREADY [0:0] [1:1], xilinx.com:interface:aximm:1.0 M02_AXI BREADY [0:0] [2:2], xilinx.com:interface:aximm:1.0 M03_AXI BREADY [0:0] [3:3]" *)
output wire [3 : 0] m_axi_bready;
(* X_INTERFACE_INFO = "xilinx.com:interface:aximm:1.0 M00_AXI ARADDR [31:0] [31:0], xilinx.com:interface:aximm:1.0 M01_AXI ARADDR [31:0] [63:32], xilinx.com:interface:aximm:1.0 M02_AXI ARADDR [31:0] [95:64], xilinx.com:interface:aximm:1.0 M03_AXI ARADDR [31:0] [127:96]" *)
output wire [127 : 0] m_axi_araddr;
(* X_INTERFACE_INFO = "xilinx.com:interface:aximm:1.0 M00_AXI ARPROT [2:0] [2:0], xilinx.com:interface:aximm:1.0 M01_AXI ARPROT [2:0] [5:3], xilinx.com:interface:aximm:1.0 M02_AXI ARPROT [2:0] [8:6], xilinx.com:interface:aximm:1.0 M03_AXI ARPROT [2:0] [11:9]" *)
output wire [11 : 0] m_axi_arprot;
(* X_INTERFACE_INFO = "xilinx.com:interface:aximm:1.0 M00_AXI ARVALID [0:0] [0:0], xilinx.com:interface:aximm:1.0 M01_AXI ARVALID [0:0] [1:1], xilinx.com:interface:aximm:1.0 M02_AXI ARVALID [0:0] [2:2], xilinx.com:interface:aximm:1.0 M03_AXI ARVALID [0:0] [3:3]" *)
output wire [3 : 0] m_axi_arvalid;
(* X_INTERFACE_INFO = "xilinx.com:interface:aximm:1.0 M00_AXI ARREADY [0:0] [0:0], xilinx.com:interface:aximm:1.0 M01_AXI ARREADY [0:0] [1:1], xilinx.com:interface:aximm:1.0 M02_AXI ARREADY [0:0] [2:2], xilinx.com:interface:aximm:1.0 M03_AXI ARREADY [0:0] [3:3]" *)
input wire [3 : 0] m_axi_arready;
(* X_INTERFACE_INFO = "xilinx.com:interface:aximm:1.0 M00_AXI RDATA [31:0] [31:0], xilinx.com:interface:aximm:1.0 M01_AXI RDATA [31:0] [63:32], xilinx.com:interface:aximm:1.0 M02_AXI RDATA [31:0] [95:64], xilinx.com:interface:aximm:1.0 M03_AXI RDATA [31:0] [127:96]" *)
input wire [127 : 0] m_axi_rdata;
(* X_INTERFACE_INFO = "xilinx.com:interface:aximm:1.0 M00_AXI RRESP [1:0] [1:0], xilinx.com:interface:aximm:1.0 M01_AXI RRESP [1:0] [3:2], xilinx.com:interface:aximm:1.0 M02_AXI RRESP [1:0] [5:4], xilinx.com:interface:aximm:1.0 M03_AXI RRESP [1:0] [7:6]" *)
input wire [7 : 0] m_axi_rresp;
(* X_INTERFACE_INFO = "xilinx.com:interface:aximm:1.0 M00_AXI RVALID [0:0] [0:0], xilinx.com:interface:aximm:1.0 M01_AXI RVALID [0:0] [1:1], xilinx.com:interface:aximm:1.0 M02_AXI RVALID [0:0] [2:2], xilinx.com:interface:aximm:1.0 M03_AXI RVALID [0:0] [3:3]" *)
input wire [3 : 0] m_axi_rvalid;
(* X_INTERFACE_INFO = "xilinx.com:interface:aximm:1.0 M00_AXI RREADY [0:0] [0:0], xilinx.com:interface:aximm:1.0 M01_AXI RREADY [0:0] [1:1], xilinx.com:interface:aximm:1.0 M02_AXI RREADY [0:0] [2:2], xilinx.com:interface:aximm:1.0 M03_AXI RREADY [0:0] [3:3]" *)
output wire [3 : 0] m_axi_rready;

  axi_crossbar_v2_1_axi_crossbar #(
    .C_FAMILY("artix7"),
    .C_NUM_SLAVE_SLOTS(1),
    .C_NUM_MASTER_SLOTS(4),
    .C_AXI_ID_WIDTH(1),
    .C_AXI_ADDR_WIDTH(32),
    .C_AXI_DATA_WIDTH(32),
    .C_AXI_PROTOCOL(2),
    .C_NUM_ADDR_RANGES(1),
    .C_M_AXI_BASE_ADDR(256'H0000000041c000000000000040e0000000000000406000000000000041200000),
    .C_M_AXI_ADDR_WIDTH(128'H00000010000000100000001000000010),
    .C_S_AXI_BASE_ID(32'H00000000),
    .C_S_AXI_THREAD_ID_WIDTH(32'H00000000),
    .C_AXI_SUPPORTS_USER_SIGNALS(0),
    .C_AXI_AWUSER_WIDTH(1),
    .C_AXI_ARUSER_WIDTH(1),
    .C_AXI_WUSER_WIDTH(1),
    .C_AXI_RUSER_WIDTH(1),
    .C_AXI_BUSER_WIDTH(1),
    .C_M_AXI_WRITE_CONNECTIVITY(128'H00000001000000010000000100000001),
    .C_M_AXI_READ_CONNECTIVITY(128'H00000001000000010000000100000001),
    .C_R_REGISTER(1),
    .C_S_AXI_SINGLE_THREAD(32'H00000001),
    .C_S_AXI_WRITE_ACCEPTANCE(32'H00000001),
    .C_S_AXI_READ_ACCEPTANCE(32'H00000001),
    .C_M_AXI_WRITE_ISSUING(128'H00000001000000010000000100000001),
    .C_M_AXI_READ_ISSUING(128'H00000001000000010000000100000001),
    .C_S_AXI_ARB_PRIORITY(32'H00000000),
    .C_M_AXI_SECURE(128'H00000000000000000000000000000000),
    .C_CONNECTIVITY_MODE(0)
  ) inst (
    .aclk(aclk),
    .aresetn(aresetn),
    .s_axi_awid(1'H0),
    .s_axi_awaddr(s_axi_awaddr),
    .s_axi_awlen(8'H00),
    .s_axi_awsize(3'H0),
    .s_axi_awburst(2'H0),
    .s_axi_awlock(1'H0),
    .s_axi_awcache(4'H0),
    .s_axi_awprot(s_axi_awprot),
    .s_axi_awqos(4'H0),
    .s_axi_awuser(1'H0),
    .s_axi_awvalid(s_axi_awvalid),
    .s_axi_awready(s_axi_awready),
    .s_axi_wid(1'H0),
    .s_axi_wdata(s_axi_wdata),
    .s_axi_wstrb(s_axi_wstrb),
    .s_axi_wlast(1'H1),
    .s_axi_wuser(1'H0),
    .s_axi_wvalid(s_axi_wvalid),
    .s_axi_wready(s_axi_wready),
    .s_axi_bid(),
    .s_axi_bresp(s_axi_bresp),
    .s_axi_buser(),
    .s_axi_bvalid(s_axi_bvalid),
    .s_axi_bready(s_axi_bready),
    .s_axi_arid(1'H0),
    .s_axi_araddr(s_axi_araddr),
    .s_axi_arlen(8'H00),
    .s_axi_arsize(3'H0),
    .s_axi_arburst(2'H0),
    .s_axi_arlock(1'H0),
    .s_axi_arcache(4'H0),
    .s_axi_arprot(s_axi_arprot),
    .s_axi_arqos(4'H0),
    .s_axi_aruser(1'H0),
    .s_axi_arvalid(s_axi_arvalid),
    .s_axi_arready(s_axi_arready),
    .s_axi_rid(),
    .s_axi_rdata(s_axi_rdata),
    .s_axi_rresp(s_axi_rresp),
    .s_axi_rlast(),
    .s_axi_ruser(),
    .s_axi_rvalid(s_axi_rvalid),
    .s_axi_rready(s_axi_rready),
    .m_axi_awid(),
    .m_axi_awaddr(m_axi_awaddr),
    .m_axi_awlen(),
    .m_axi_awsize(),
    .m_axi_awburst(),
    .m_axi_awlock(),
    .m_axi_awcache(),
    .m_axi_awprot(m_axi_awprot),
    .m_axi_awregion(),
    .m_axi_awqos(),
    .m_axi_awuser(),
    .m_axi_awvalid(m_axi_awvalid),
    .m_axi_awready(m_axi_awready),
    .m_axi_wid(),
    .m_axi_wdata(m_axi_wdata),
    .m_axi_wstrb(m_axi_wstrb),
    .m_axi_wlast(),
    .m_axi_wuser(),
    .m_axi_wvalid(m_axi_wvalid),
    .m_axi_wready(m_axi_wready),
    .m_axi_bid(4'H0),
    .m_axi_bresp(m_axi_bresp),
    .m_axi_buser(4'H0),
    .m_axi_bvalid(m_axi_bvalid),
    .m_axi_bready(m_axi_bready),
    .m_axi_arid(),
    .m_axi_araddr(m_axi_araddr),
    .m_axi_arlen(),
    .m_axi_arsize(),
    .m_axi_arburst(),
    .m_axi_arlock(),
    .m_axi_arcache(),
    .m_axi_arprot(m_axi_arprot),
    .m_axi_arregion(),
    .m_axi_arqos(),
    .m_axi_aruser(),
    .m_axi_arvalid(m_axi_arvalid),
    .m_axi_arready(m_axi_arready),
    .m_axi_rid(4'H0),
    .m_axi_rdata(m_axi_rdata),
    .m_axi_rresp(m_axi_rresp),
    .m_axi_rlast(4'HF),
    .m_axi_ruser(4'H0),
    .m_axi_rvalid(m_axi_rvalid),
    .m_axi_rready(m_axi_rready)
  );
endmodule
