AlistairCheeseman/WindTunnelApparatus/Firmware/Tests/FPGA/FPGAEchoExample/GSMBS2015.2.srcs/sources_1/bd/design_1/hdl/design_1.v

//Copyright 1986-2015 Xilinx, Inc. All Rights Reserved.
//--------------------------------------------------------------------------------
//Tool Version: Vivado v.2015.2 (win64) Build 1266856 Fri Jun 26 16:35:25 MDT 2015
//Date        : Sun Nov 15 11:47:59 2015
//Host        : ALI-WORKSTATION running 64-bit major release  (build 9200)
//Command     : generate_target design_1.bd
//Design      : design_1
//Purpose     : IP block netlist
//--------------------------------------------------------------------------------
`timescale 1 ps / 1 ps

(* CORE_GENERATION_INFO = "design_1,IP_Integrator,{x_ipProduct=Vivado 2015.2,x_ipVendor=xilinx.com,x_ipLibrary=BlockDiagram,x_ipName=design_1,x_ipVersion=1.00.a,x_ipLanguage=VERILOG,numBlks=29,numReposBlks=18,numNonXlnxBlks=0,numHierBlks=11,maxHierDepth=1,da_axi4_cnt=4,da_board_cnt=8,da_mb_cnt=1,synth_mode=Global}" *) (* HW_HANDOFF = "design_1.hwdef" *) 
module design_1
   (cellular_ram_addr,
    cellular_ram_adv_ldn,
    cellular_ram_ben,
    cellular_ram_ce_n,
    cellular_ram_cre,
    cellular_ram_dq_i,
    cellular_ram_dq_o,
    cellular_ram_dq_t,
    cellular_ram_oen,
    cellular_ram_wait,
    cellular_ram_wen,
    eth_mdio_mdc_mdc,
    eth_mdio_mdc_mdio_i,
    eth_mdio_mdc_mdio_o,
    eth_mdio_mdc_mdio_t,
    eth_ref_clk,
    eth_rmii_crs_dv,
    eth_rmii_rx_er,
    eth_rmii_rxd,
    eth_rmii_tx_en,
    eth_rmii_txd,
    reset,
    sys_clock,
    usb_uart_rxd,
    usb_uart_txd);
  output [22:0]cellular_ram_addr;
  output cellular_ram_adv_ldn;
  output [1:0]cellular_ram_ben;
  output cellular_ram_ce_n;
  output cellular_ram_cre;
  input [15:0]cellular_ram_dq_i;
  output [15:0]cellular_ram_dq_o;
  output [15:0]cellular_ram_dq_t;
  output cellular_ram_oen;
  input cellular_ram_wait;
  output cellular_ram_wen;
  output eth_mdio_mdc_mdc;
  input eth_mdio_mdc_mdio_i;
  output eth_mdio_mdc_mdio_o;
  output eth_mdio_mdc_mdio_t;
  output eth_ref_clk;
  input eth_rmii_crs_dv;
  input eth_rmii_rx_er;
  input [1:0]eth_rmii_rxd;
  output eth_rmii_tx_en;
  output [1:0]eth_rmii_txd;
  input reset;
  input sys_clock;
  input usb_uart_rxd;
  output usb_uart_txd;

  wire GND_1;
  wire VCC_1;
  wire [22:0]axi_emc_0_EMC_INTF_ADDR;
  wire axi_emc_0_EMC_INTF_ADV_LDN;
  wire [1:0]axi_emc_0_EMC_INTF_BEN;
  wire [0:0]axi_emc_0_EMC_INTF_CE_N;
  wire axi_emc_0_EMC_INTF_CRE;
  wire [15:0]axi_emc_0_EMC_INTF_DQ_I;
  wire [15:0]axi_emc_0_EMC_INTF_DQ_O;
  wire [15:0]axi_emc_0_EMC_INTF_DQ_T;
  wire [0:0]axi_emc_0_EMC_INTF_OEN;
  wire axi_emc_0_EMC_INTF_WAIT;
  wire axi_emc_0_EMC_INTF_WEN;
  wire axi_ethernetlite_0_MDIO_MDC;
  wire axi_ethernetlite_0_MDIO_MDIO_I;
  wire axi_ethernetlite_0_MDIO_MDIO_O;
  wire axi_ethernetlite_0_MDIO_MDIO_T;
  wire axi_ethernetlite_0_MII_COL;
  wire axi_ethernetlite_0_MII_CRS;
  wire [3:0]axi_ethernetlite_0_MII_RXD;
  wire axi_ethernetlite_0_MII_RX_CLK;
  wire axi_ethernetlite_0_MII_RX_DV;
  wire axi_ethernetlite_0_MII_RX_ER;
  wire [3:0]axi_ethernetlite_0_MII_TXD;
  wire axi_ethernetlite_0_MII_TX_CLK;
  wire axi_ethernetlite_0_MII_TX_EN;
  wire axi_ethernetlite_0_ip2intc_irpt;
  wire [31:0]axi_mem_intercon_M00_AXI_ARADDR;
  wire [1:0]axi_mem_intercon_M00_AXI_ARBURST;
  wire [3:0]axi_mem_intercon_M00_AXI_ARCACHE;
  wire [0:0]axi_mem_intercon_M00_AXI_ARID;
  wire [7:0]axi_mem_intercon_M00_AXI_ARLEN;
  wire [0:0]axi_mem_intercon_M00_AXI_ARLOCK;
  wire [2:0]axi_mem_intercon_M00_AXI_ARPROT;
  wire axi_mem_intercon_M00_AXI_ARREADY;
  wire [2:0]axi_mem_intercon_M00_AXI_ARSIZE;
  wire [0:0]axi_mem_intercon_M00_AXI_ARVALID;
  wire [31:0]axi_mem_intercon_M00_AXI_AWADDR;
  wire [1:0]axi_mem_intercon_M00_AXI_AWBURST;
  wire [3:0]axi_mem_intercon_M00_AXI_AWCACHE;
  wire [0:0]axi_mem_intercon_M00_AXI_AWID;
  wire [7:0]axi_mem_intercon_M00_AXI_AWLEN;
  wire [0:0]axi_mem_intercon_M00_AXI_AWLOCK;
  wire [2:0]axi_mem_intercon_M00_AXI_AWPROT;
  wire axi_mem_intercon_M00_AXI_AWREADY;
  wire [2:0]axi_mem_intercon_M00_AXI_AWSIZE;
  wire [0:0]axi_mem_intercon_M00_AXI_AWVALID;
  wire [0:0]axi_mem_intercon_M00_AXI_BID;
  wire [0:0]axi_mem_intercon_M00_AXI_BREADY;
  wire [1:0]axi_mem_intercon_M00_AXI_BRESP;
  wire axi_mem_intercon_M00_AXI_BVALID;
  wire [31:0]axi_mem_intercon_M00_AXI_RDATA;
  wire [0:0]axi_mem_intercon_M00_AXI_RID;
  wire axi_mem_intercon_M00_AXI_RLAST;
  wire [0:0]axi_mem_intercon_M00_AXI_RREADY;
  wire [1:0]axi_mem_intercon_M00_AXI_RRESP;
  wire axi_mem_intercon_M00_AXI_RVALID;
  wire [31:0]axi_mem_intercon_M00_AXI_WDATA;
  wire [0:0]axi_mem_intercon_M00_AXI_WLAST;
  wire axi_mem_intercon_M00_AXI_WREADY;
  wire [3:0]axi_mem_intercon_M00_AXI_WSTRB;
  wire [0:0]axi_mem_intercon_M00_AXI_WVALID;
  wire axi_timer_0_interrupt;
  wire axi_uartlite_0_UART_RxD;
  wire axi_uartlite_0_UART_TxD;
  wire clk_wiz_1_clk_out2;
  wire clk_wiz_1_locked;
  wire mdm_1_debug_sys_rst;
  wire microblaze_0_Clk;
  wire [31:0]microblaze_0_M_AXI_DC_ARADDR;
  wire [1:0]microblaze_0_M_AXI_DC_ARBURST;
  wire [3:0]microblaze_0_M_AXI_DC_ARCACHE;
  wire [0:0]microblaze_0_M_AXI_DC_ARID;
  wire [7:0]microblaze_0_M_AXI_DC_ARLEN;
  wire microblaze_0_M_AXI_DC_ARLOCK;
  wire [2:0]microblaze_0_M_AXI_DC_ARPROT;
  wire [3:0]microblaze_0_M_AXI_DC_ARQOS;
  wire [0:0]microblaze_0_M_AXI_DC_ARREADY;
  wire [2:0]microblaze_0_M_AXI_DC_ARSIZE;
  wire microblaze_0_M_AXI_DC_ARVALID;
  wire [31:0]microblaze_0_M_AXI_DC_AWADDR;
  wire [1:0]microblaze_0_M_AXI_DC_AWBURST;
  wire [3:0]microblaze_0_M_AXI_DC_AWCACHE;
  wire [0:0]microblaze_0_M_AXI_DC_AWID;
  wire [7:0]microblaze_0_M_AXI_DC_AWLEN;
  wire microblaze_0_M_AXI_DC_AWLOCK;
  wire [2:0]microblaze_0_M_AXI_DC_AWPROT;
  wire [3:0]microblaze_0_M_AXI_DC_AWQOS;
  wire [0:0]microblaze_0_M_AXI_DC_AWREADY;
  wire [2:0]microblaze_0_M_AXI_DC_AWSIZE;
  wire microblaze_0_M_AXI_DC_AWVALID;
  wire [0:0]microblaze_0_M_AXI_DC_BID;
  wire microblaze_0_M_AXI_DC_BREADY;
  wire [1:0]microblaze_0_M_AXI_DC_BRESP;
  wire [0:0]microblaze_0_M_AXI_DC_BVALID;
  wire [31:0]microblaze_0_M_AXI_DC_RDATA;
  wire [0:0]microblaze_0_M_AXI_DC_RID;
  wire [0:0]microblaze_0_M_AXI_DC_RLAST;
  wire microblaze_0_M_AXI_DC_RREADY;
  wire [1:0]microblaze_0_M_AXI_DC_RRESP;
  wire [0:0]microblaze_0_M_AXI_DC_RVALID;
  wire [31:0]microblaze_0_M_AXI_DC_WDATA;
  wire microblaze_0_M_AXI_DC_WLAST;
  wire [0:0]microblaze_0_M_AXI_DC_WREADY;
  wire [3:0]microblaze_0_M_AXI_DC_WSTRB;
  wire microblaze_0_M_AXI_DC_WVALID;
  wire [31:0]microblaze_0_M_AXI_IC_ARADDR;
  wire [1:0]microblaze_0_M_AXI_IC_ARBURST;
  wire [3:0]microblaze_0_M_AXI_IC_ARCACHE;
  wire [0:0]microblaze_0_M_AXI_IC_ARID;
  wire [7:0]microblaze_0_M_AXI_IC_ARLEN;
  wire microblaze_0_M_AXI_IC_ARLOCK;
  wire [2:0]microblaze_0_M_AXI_IC_ARPROT;
  wire [3:0]microblaze_0_M_AXI_IC_ARQOS;
  wire [0:0]microblaze_0_M_AXI_IC_ARREADY;
  wire [2:0]microblaze_0_M_AXI_IC_ARSIZE;
  wire microblaze_0_M_AXI_IC_ARVALID;
  wire [31:0]microblaze_0_M_AXI_IC_AWADDR;
  wire [1:0]microblaze_0_M_AXI_IC_AWBURST;
  wire [3:0]microblaze_0_M_AXI_IC_AWCACHE;
  wire [0:0]microblaze_0_M_AXI_IC_AWID;
  wire [7:0]microblaze_0_M_AXI_IC_AWLEN;
  wire microblaze_0_M_AXI_IC_AWLOCK;
  wire [2:0]microblaze_0_M_AXI_IC_AWPROT;
  wire [3:0]microblaze_0_M_AXI_IC_AWQOS;
  wire [0:0]microblaze_0_M_AXI_IC_AWREADY;
  wire [2:0]microblaze_0_M_AXI_IC_AWSIZE;
  wire microblaze_0_M_AXI_IC_AWVALID;
  wire [0:0]microblaze_0_M_AXI_IC_BID;
  wire microblaze_0_M_AXI_IC_BREADY;
  wire [1:0]microblaze_0_M_AXI_IC_BRESP;
  wire [0:0]microblaze_0_M_AXI_IC_BVALID;
  wire [31:0]microblaze_0_M_AXI_IC_RDATA;
  wire [0:0]microblaze_0_M_AXI_IC_RID;
  wire [0:0]microblaze_0_M_AXI_IC_RLAST;
  wire microblaze_0_M_AXI_IC_RREADY;
  wire [1:0]microblaze_0_M_AXI_IC_RRESP;
  wire [0:0]microblaze_0_M_AXI_IC_RVALID;
  wire [31:0]microblaze_0_M_AXI_IC_WDATA;
  wire microblaze_0_M_AXI_IC_WLAST;
  wire [0:0]microblaze_0_M_AXI_IC_WREADY;
  wire [3:0]microblaze_0_M_AXI_IC_WSTRB;
  wire microblaze_0_M_AXI_IC_WVALID;
  wire [31:0]microblaze_0_axi_dp_ARADDR;
  wire [2:0]microblaze_0_axi_dp_ARPROT;
  wire [0:0]microblaze_0_axi_dp_ARREADY;
  wire microblaze_0_axi_dp_ARVALID;
  wire [31:0]microblaze_0_axi_dp_AWADDR;
  wire [2:0]microblaze_0_axi_dp_AWPROT;
  wire [0:0]microblaze_0_axi_dp_AWREADY;
  wire microblaze_0_axi_dp_AWVALID;
  wire microblaze_0_axi_dp_BREADY;
  wire [1:0]microblaze_0_axi_dp_BRESP;
  wire [0:0]microblaze_0_axi_dp_BVALID;
  wire [31:0]microblaze_0_axi_dp_RDATA;
  wire microblaze_0_axi_dp_RREADY;
  wire [1:0]microblaze_0_axi_dp_RRESP;
  wire [0:0]microblaze_0_axi_dp_RVALID;
  wire [31:0]microblaze_0_axi_dp_WDATA;
  wire [0:0]microblaze_0_axi_dp_WREADY;
  wire [3:0]microblaze_0_axi_dp_WSTRB;
  wire microblaze_0_axi_dp_WVALID;
  wire [3:0]microblaze_0_axi_periph_M01_AXI_ARADDR;
  wire microblaze_0_axi_periph_M01_AXI_ARREADY;
  wire microblaze_0_axi_periph_M01_AXI_ARVALID;
  wire [3:0]microblaze_0_axi_periph_M01_AXI_AWADDR;
  wire microblaze_0_axi_periph_M01_AXI_AWREADY;
  wire microblaze_0_axi_periph_M01_AXI_AWVALID;
  wire microblaze_0_axi_periph_M01_AXI_BREADY;
  wire [1:0]microblaze_0_axi_periph_M01_AXI_BRESP;
  wire microblaze_0_axi_periph_M01_AXI_BVALID;
  wire [31:0]microblaze_0_axi_periph_M01_AXI_RDATA;
  wire microblaze_0_axi_periph_M01_AXI_RREADY;
  wire [1:0]microblaze_0_axi_periph_M01_AXI_RRESP;
  wire microblaze_0_axi_periph_M01_AXI_RVALID;
  wire [31:0]microblaze_0_axi_periph_M01_AXI_WDATA;
  wire microblaze_0_axi_periph_M01_AXI_WREADY;
  wire [3:0]microblaze_0_axi_periph_M01_AXI_WSTRB;
  wire microblaze_0_axi_periph_M01_AXI_WVALID;
  wire [12:0]microblaze_0_axi_periph_M02_AXI_ARADDR;
  wire microblaze_0_axi_periph_M02_AXI_ARREADY;
  wire microblaze_0_axi_periph_M02_AXI_ARVALID;
  wire [12:0]microblaze_0_axi_periph_M02_AXI_AWADDR;
  wire microblaze_0_axi_periph_M02_AXI_AWREADY;
  wire microblaze_0_axi_periph_M02_AXI_AWVALID;
  wire microblaze_0_axi_periph_M02_AXI_BREADY;
  wire [1:0]microblaze_0_axi_periph_M02_AXI_BRESP;
  wire microblaze_0_axi_periph_M02_AXI_BVALID;
  wire [31:0]microblaze_0_axi_periph_M02_AXI_RDATA;
  wire microblaze_0_axi_periph_M02_AXI_RREADY;
  wire [1:0]microblaze_0_axi_periph_M02_AXI_RRESP;
  wire microblaze_0_axi_periph_M02_AXI_RVALID;
  wire [31:0]microblaze_0_axi_periph_M02_AXI_WDATA;
  wire microblaze_0_axi_periph_M02_AXI_WREADY;
  wire [3:0]microblaze_0_axi_periph_M02_AXI_WSTRB;
  wire microblaze_0_axi_periph_M02_AXI_WVALID;
  wire [4:0]microblaze_0_axi_periph_M03_AXI_ARADDR;
  wire microblaze_0_axi_periph_M03_AXI_ARREADY;
  wire microblaze_0_axi_periph_M03_AXI_ARVALID;
  wire [4:0]microblaze_0_axi_periph_M03_AXI_AWADDR;
  wire microblaze_0_axi_periph_M03_AXI_AWREADY;
  wire microblaze_0_axi_periph_M03_AXI_AWVALID;
  wire microblaze_0_axi_periph_M03_AXI_BREADY;
  wire [1:0]microblaze_0_axi_periph_M03_AXI_BRESP;
  wire microblaze_0_axi_periph_M03_AXI_BVALID;
  wire [31:0]microblaze_0_axi_periph_M03_AXI_RDATA;
  wire microblaze_0_axi_periph_M03_AXI_RREADY;
  wire [1:0]microblaze_0_axi_periph_M03_AXI_RRESP;
  wire microblaze_0_axi_periph_M03_AXI_RVALID;
  wire [31:0]microblaze_0_axi_periph_M03_AXI_WDATA;
  wire microblaze_0_axi_periph_M03_AXI_WREADY;
  wire [3:0]microblaze_0_axi_periph_M03_AXI_WSTRB;
  wire microblaze_0_axi_periph_M03_AXI_WVALID;
  wire microblaze_0_debug_CAPTURE;
  wire microblaze_0_debug_CLK;
  wire [0:7]microblaze_0_debug_REG_EN;
  wire microblaze_0_debug_RST;
  wire microblaze_0_debug_SHIFT;
  wire microblaze_0_debug_TDI;
  wire microblaze_0_debug_TDO;
  wire microblaze_0_debug_UPDATE;
  wire [0:31]microblaze_0_dlmb_1_ABUS;
  wire microblaze_0_dlmb_1_ADDRSTROBE;
  wire [0:3]microblaze_0_dlmb_1_BE;
  wire microblaze_0_dlmb_1_CE;
  wire [0:31]microblaze_0_dlmb_1_READDBUS;
  wire microblaze_0_dlmb_1_READSTROBE;
  wire microblaze_0_dlmb_1_READY;
  wire microblaze_0_dlmb_1_UE;
  wire microblaze_0_dlmb_1_WAIT;
  wire [0:31]microblaze_0_dlmb_1_WRITEDBUS;
  wire microblaze_0_dlmb_1_WRITESTROBE;
  wire [0:31]microblaze_0_ilmb_1_ABUS;
  wire microblaze_0_ilmb_1_ADDRSTROBE;
  wire microblaze_0_ilmb_1_CE;
  wire [0:31]microblaze_0_ilmb_1_READDBUS;
  wire microblaze_0_ilmb_1_READSTROBE;
  wire microblaze_0_ilmb_1_READY;
  wire microblaze_0_ilmb_1_UE;
  wire microblaze_0_ilmb_1_WAIT;
  wire [8:0]microblaze_0_intc_axi_ARADDR;
  wire microblaze_0_intc_axi_ARREADY;
  wire microblaze_0_intc_axi_ARVALID;
  wire [8:0]microblaze_0_intc_axi_AWADDR;
  wire microblaze_0_intc_axi_AWREADY;
  wire microblaze_0_intc_axi_AWVALID;
  wire microblaze_0_intc_axi_BREADY;
  wire [1:0]microblaze_0_intc_axi_BRESP;
  wire microblaze_0_intc_axi_BVALID;
  wire [31:0]microblaze_0_intc_axi_RDATA;
  wire microblaze_0_intc_axi_RREADY;
  wire [1:0]microblaze_0_intc_axi_RRESP;
  wire microblaze_0_intc_axi_RVALID;
  wire [31:0]microblaze_0_intc_axi_WDATA;
  wire microblaze_0_intc_axi_WREADY;
  wire [3:0]microblaze_0_intc_axi_WSTRB;
  wire microblaze_0_intc_axi_WVALID;
  wire [0:1]microblaze_0_interrupt_ACK;
  wire [31:0]microblaze_0_interrupt_ADDRESS;
  wire microblaze_0_interrupt_INTERRUPT;
  wire [1:0]microblaze_0_intr;
  wire mii_to_rmii_0_RMII_PHY_M_CRS_DV;
  wire [1:0]mii_to_rmii_0_RMII_PHY_M_RXD;
  wire mii_to_rmii_0_RMII_PHY_M_RX_ER;
  wire [1:0]mii_to_rmii_0_RMII_PHY_M_TXD;
  wire mii_to_rmii_0_RMII_PHY_M_TX_EN;
  wire reset_1;
  wire [0:0]rst_clk_wiz_1_100M_bus_struct_reset;
  wire [0:0]rst_clk_wiz_1_100M_interconnect_aresetn;
  wire rst_clk_wiz_1_100M_mb_reset;
  wire [0:0]rst_clk_wiz_1_100M_peripheral_aresetn;
  wire sys_clock_1;
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
